juan-felipe-castilla/TP2_Analogica/FotosMed/Barrido de amplitud/E1/1m.jpeg

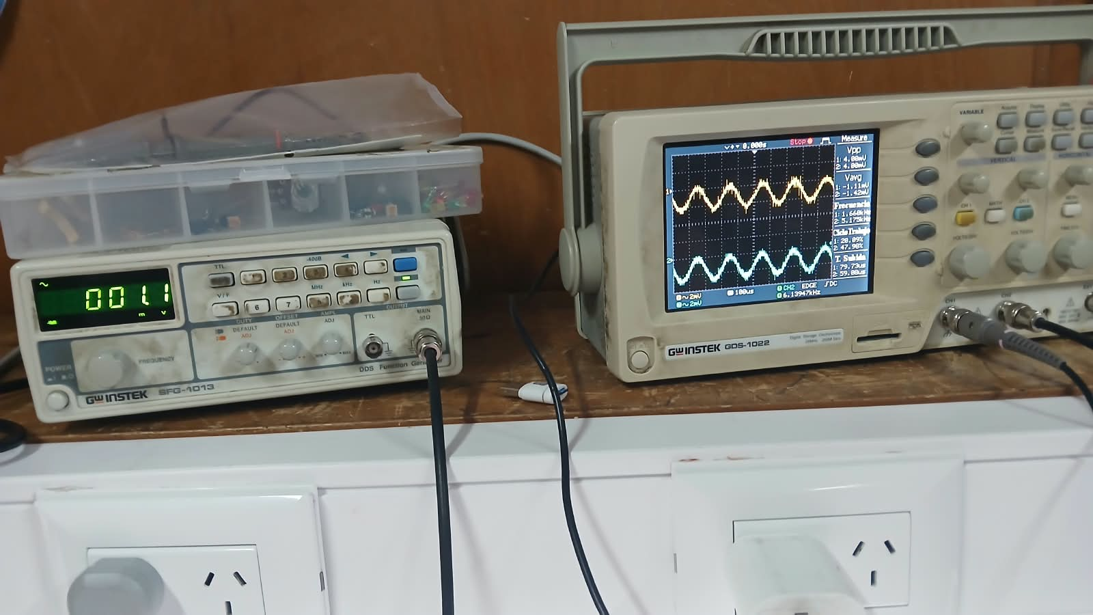
FotosMed/Barrido de amplitud/E1/1m.jpeg
