juan-felipe-castilla/TP2_Analogica/FotosMed/Barrido de amplitud/E1/2.5m.jpeg

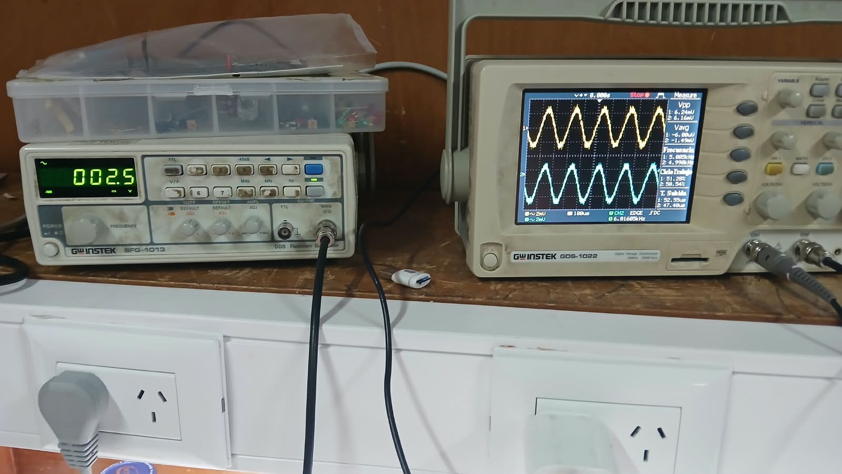
FotosMed/Barrido de amplitud/E1/2.5m.jpeg
