juan-felipe-castilla/TP2_Analogica/FotosMed/Barrido de amplitud/E1/5m.jpeg

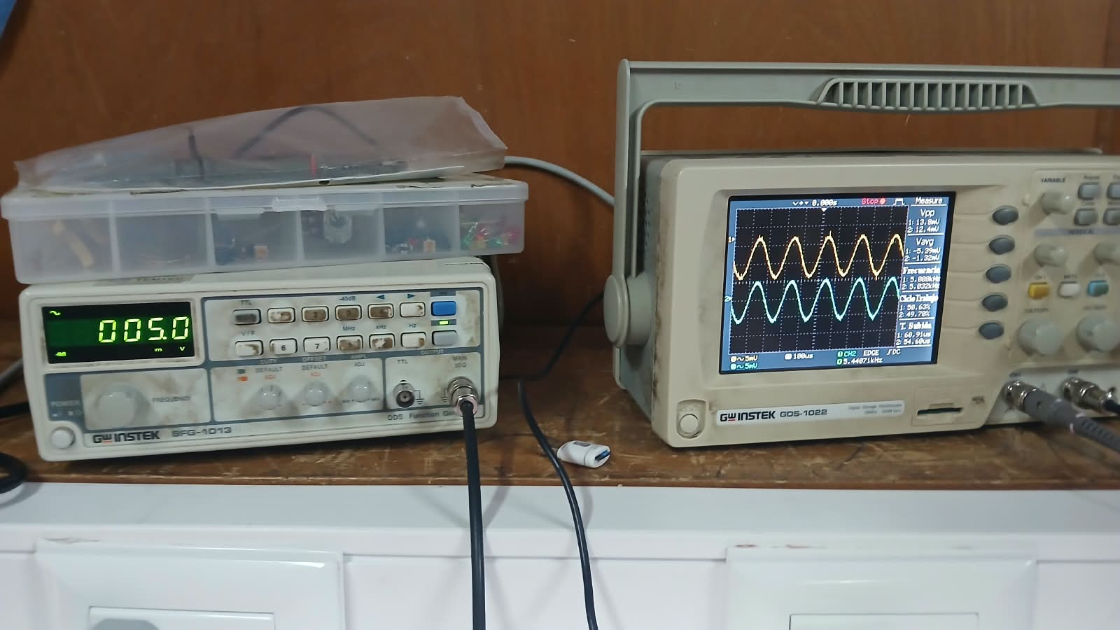
FotosMed/Barrido de amplitud/E1/5m.jpeg
