juan-felipe-castilla/TP2_Analogica/FotosMed/Barrido de amplitud/E1/7.5zoom.jpeg

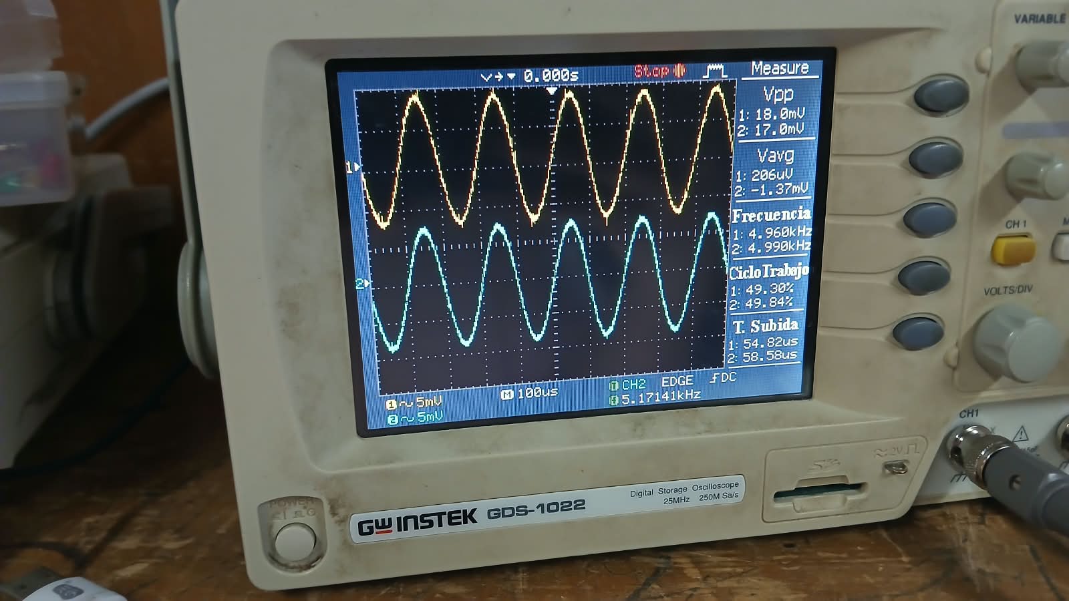
FotosMed/Barrido de amplitud/E1/7.5zoom.jpeg
