juan-felipe-castilla/TP2_Analogica/FotosMed/Barrido de amplitud/E1/10m.jpeg

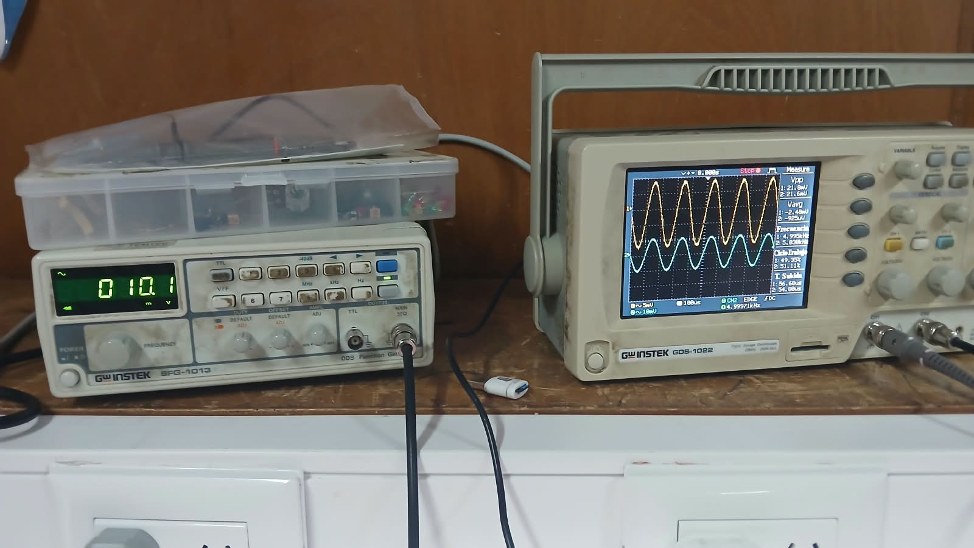
FotosMed/Barrido de amplitud/E1/10m.jpeg
