juan-felipe-castilla/TP2_Analogica/FotosMed/Barrido de amplitud/E1/12.jpeg

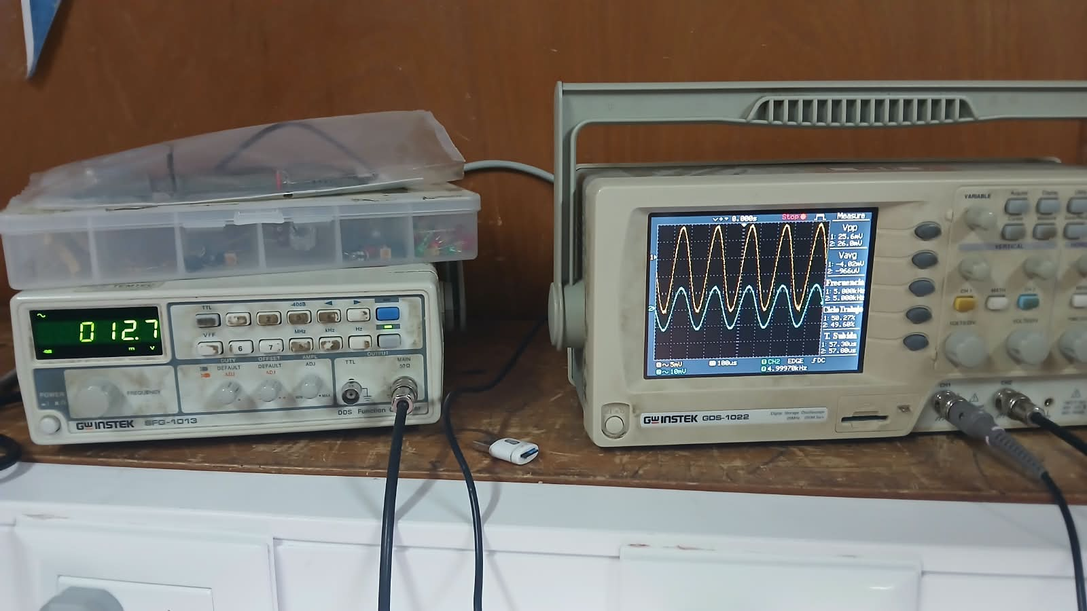
FotosMed/Barrido de amplitud/E1/12.jpeg
