juan-felipe-castilla/TP2_Analogica/FotosMed/Barrido de amplitud/E1/35m.jpeg

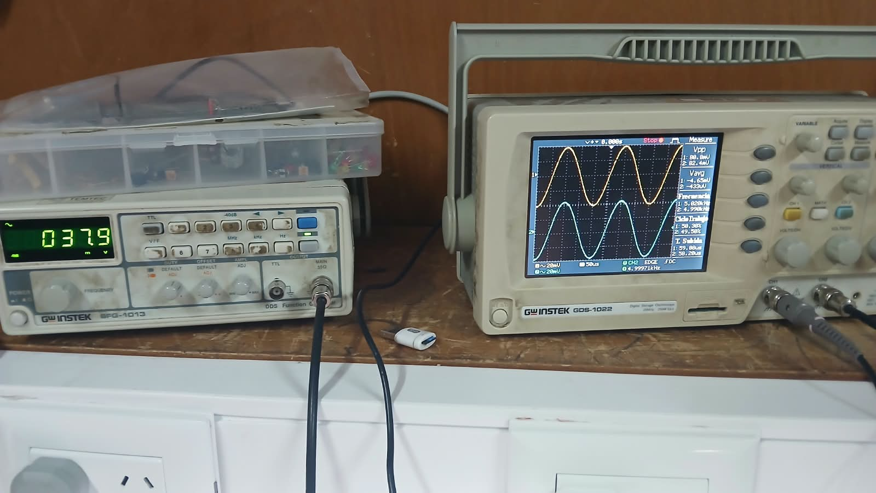
FotosMed/Barrido de amplitud/E1/35m.jpeg
