juan-felipe-castilla/TP2_Analogica/FotosMed/Barrido de amplitud/E1/37mzoom.jpeg

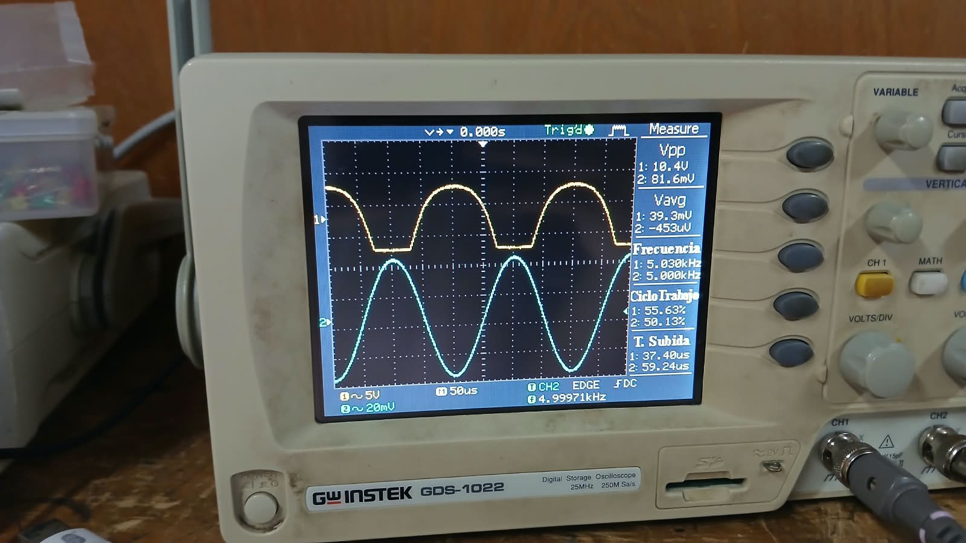
FotosMed/Barrido de amplitud/E1/37mzoom.jpeg
