juan-felipe-castilla/TP2_Analogica/FotosMed/Barrido de amplitud/E1/50m.jpeg

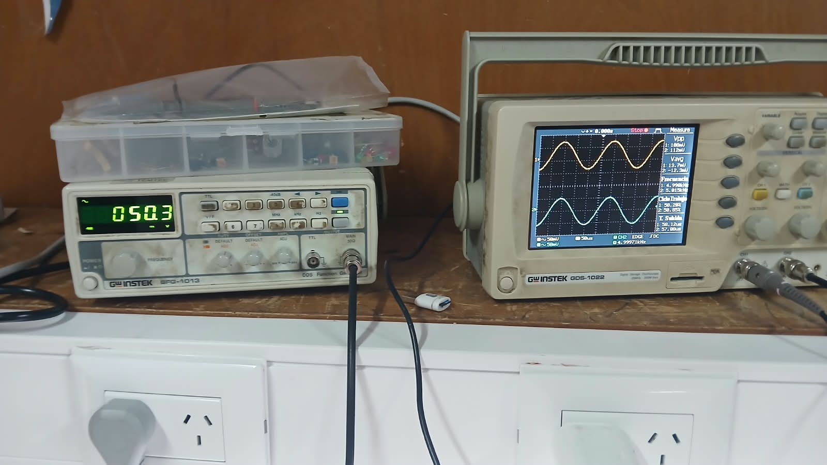
FotosMed/Barrido de amplitud/E1/50m.jpeg
