juan-felipe-castilla/TP2_Analogica/FotosMed/Barrido de amplitud/E12/1M.jpeg

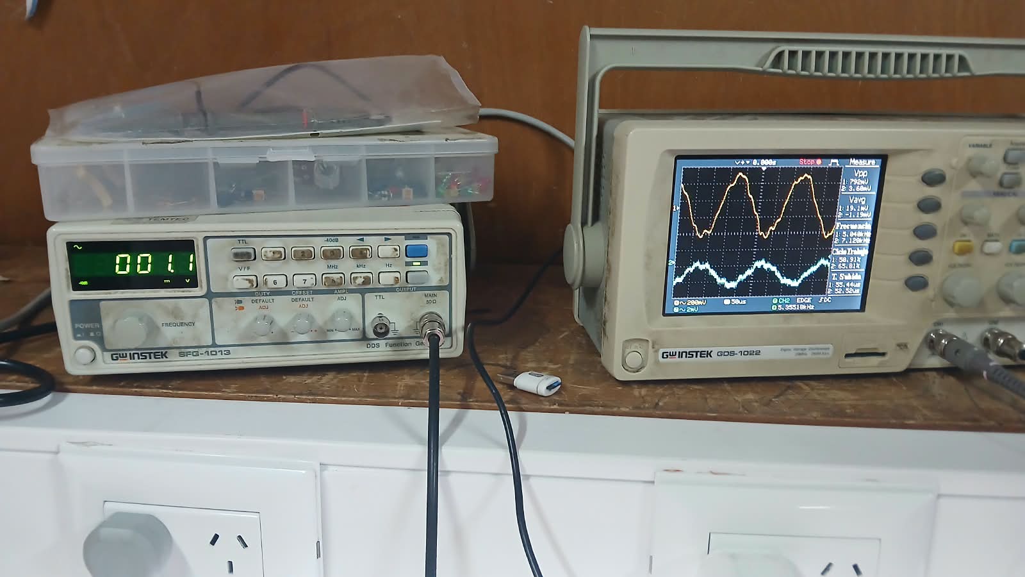
FotosMed/Barrido de amplitud/E12/1M.jpeg
