juan-felipe-castilla/TP2_Analogica/FotosMed/Barrido de amplitud/E12/5m.jpeg

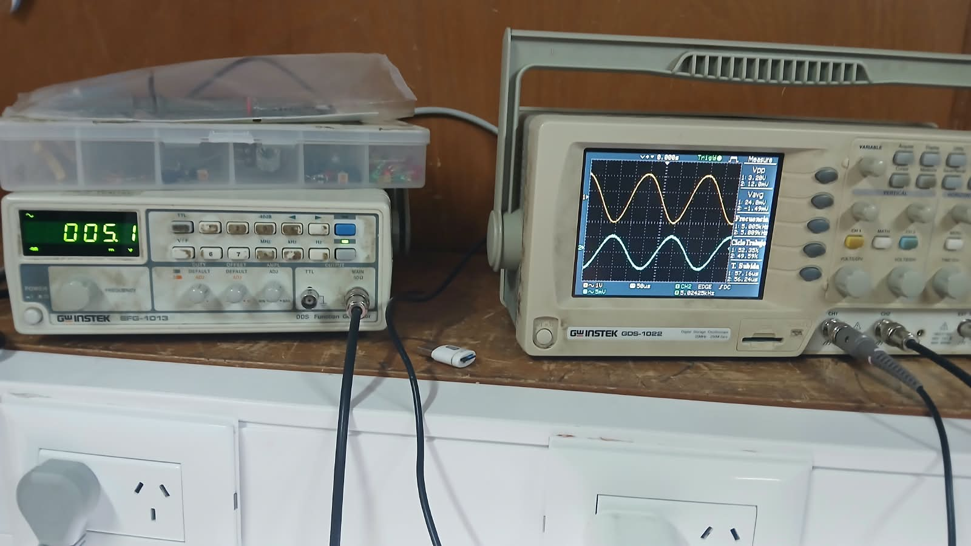
FotosMed/Barrido de amplitud/E12/5m.jpeg
