juan-felipe-castilla/TP2_Analogica/FotosMed/Barrido de amplitud/E12/7.5m.jpeg

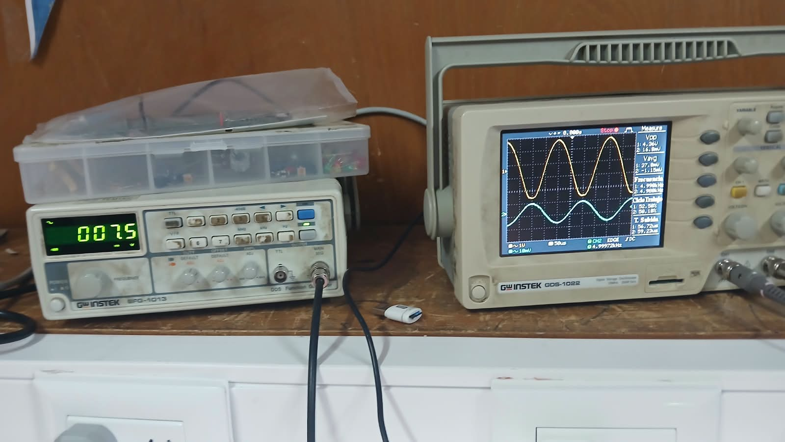
FotosMed/Barrido de amplitud/E12/7.5m.jpeg
