juan-felipe-castilla/TP2_Analogica/FotosMed/Barrido de amplitud/E12/8.5.jpeg

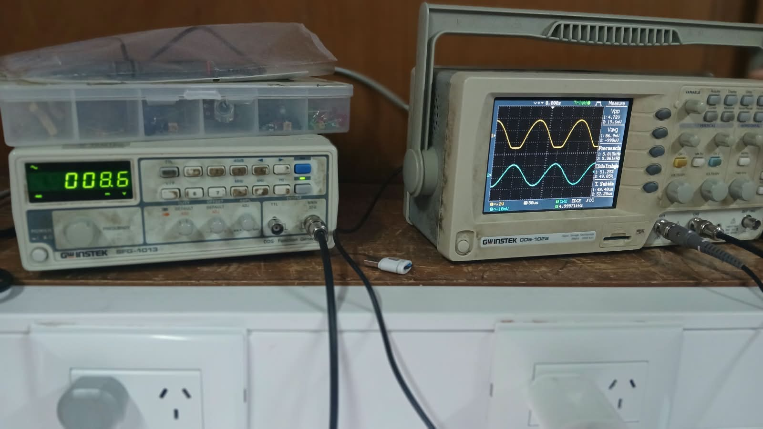
FotosMed/Barrido de amplitud/E12/8.5.jpeg
