juan-felipe-castilla/TP2_Analogica/FotosMed/Barrido de amplitud/E12/10mzoom.jpeg

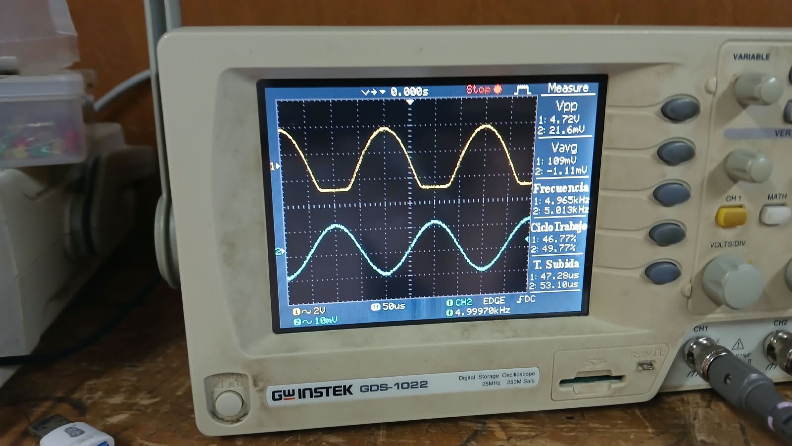
FotosMed/Barrido de amplitud/E12/10mzoom.jpeg
