juan-felipe-castilla/TP2_Analogica/FotosMed/Barrido de amplitud/E12/25m.jpeg

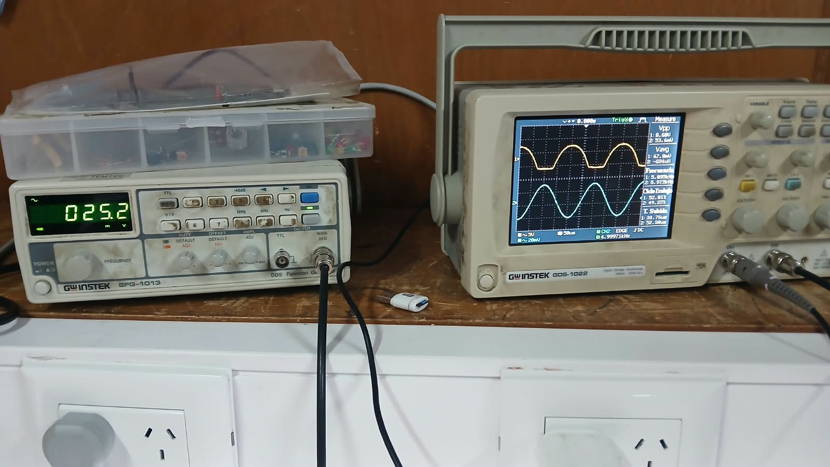
FotosMed/Barrido de amplitud/E12/25m.jpeg
