juan-felipe-castilla/TP2_Analogica/FotosMed/Barrido de amplitud/E12/50m.jpeg

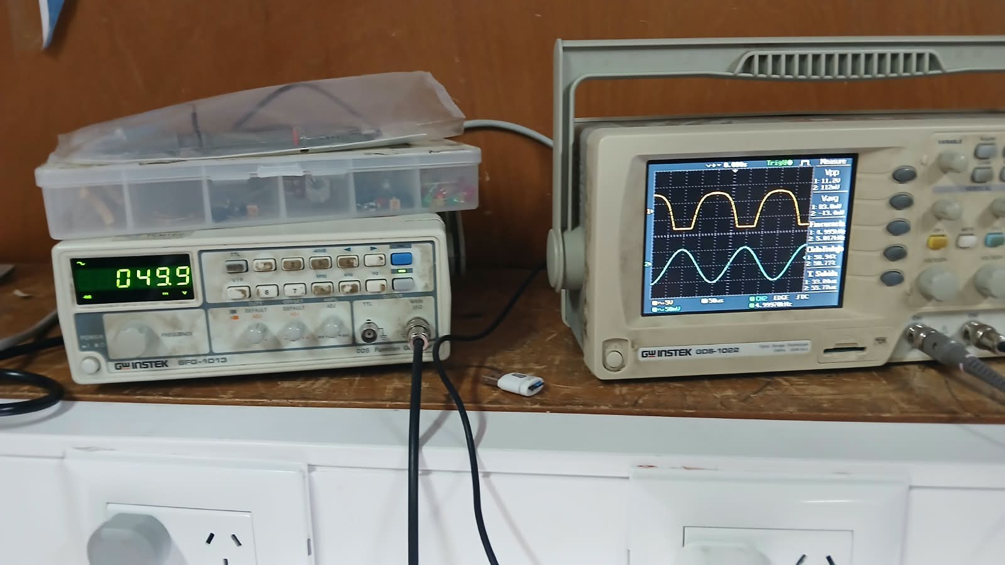
FotosMed/Barrido de amplitud/E12/50m.jpeg
