juan-felipe-castilla/TP2_Analogica/FotosMed/Barrido de amplitud/ETOTAL/1M.jpeg

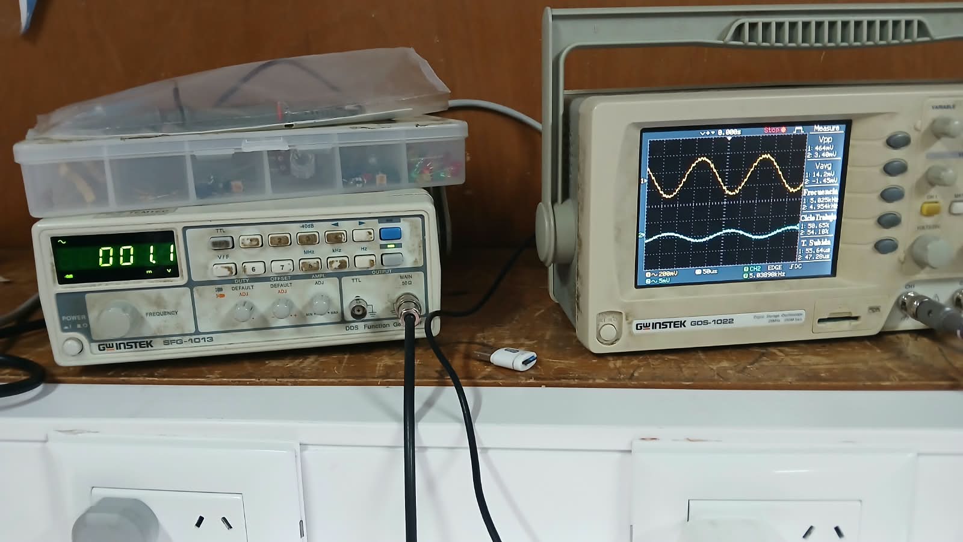
FotosMed/Barrido de amplitud/ETOTAL/1M.jpeg
