juan-felipe-castilla/TP2_Analogica/FotosMed/Barrido de amplitud/ETOTAL/1mzoom.jpeg

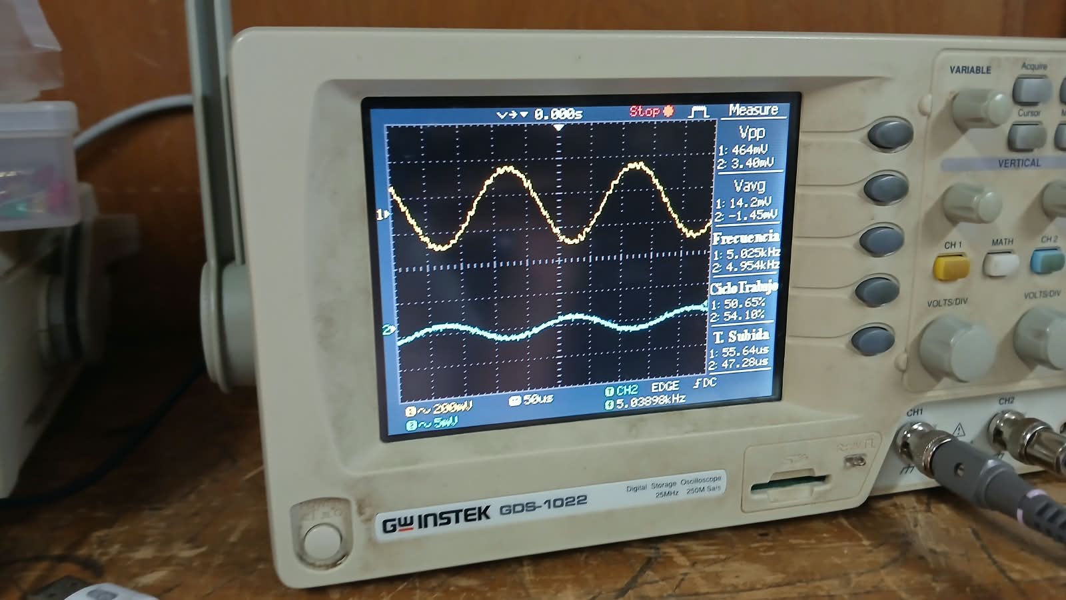
FotosMed/Barrido de amplitud/ETOTAL/1mzoom.jpeg
