juan-felipe-castilla/TP2_Analogica/FotosMed/Barrido de amplitud/ETOTAL/5m.jpeg

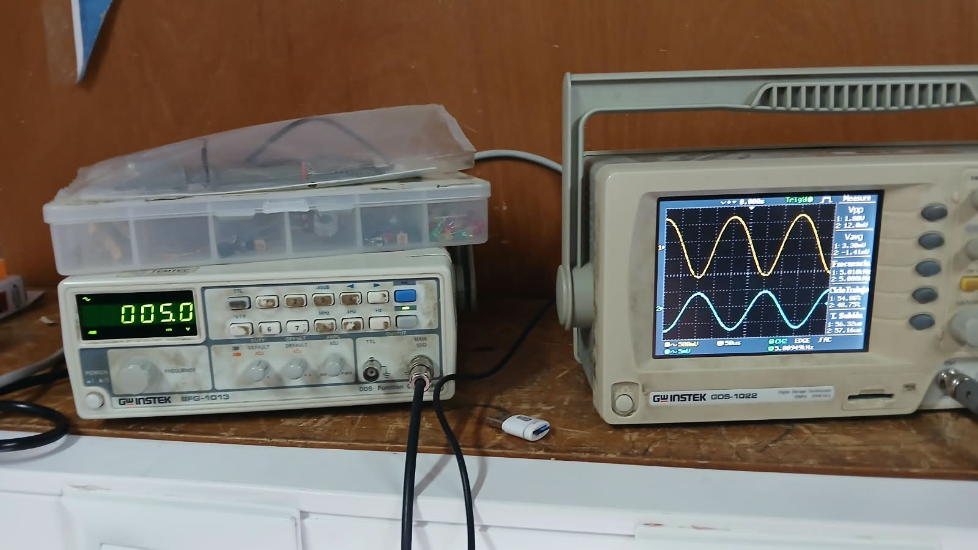
FotosMed/Barrido de amplitud/ETOTAL/5m.jpeg
