juan-felipe-castilla/TP2_Analogica/FotosMed/Barrido de amplitud/ETOTAL/7.5mzoom.jpeg

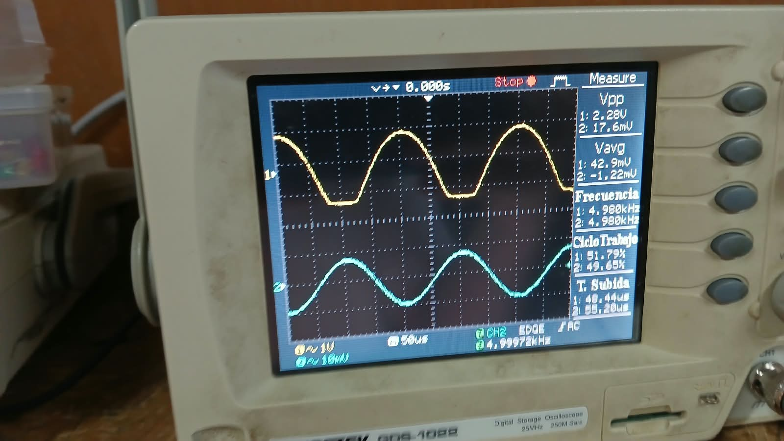
FotosMed/Barrido de amplitud/ETOTAL/7.5mzoom.jpeg
