juan-felipe-castilla/TP2_Analogica/FotosMed/Barrido de amplitud/ETOTAL/10m.jpeg

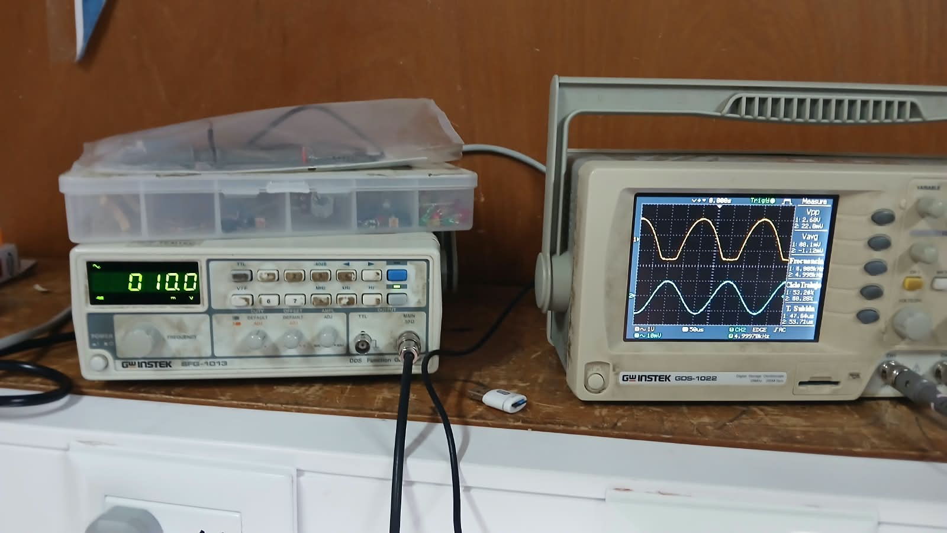
FotosMed/Barrido de amplitud/ETOTAL/10m.jpeg
