juan-felipe-castilla/TP2_Analogica/FotosMed/Barrido de amplitud/ETOTAL/12.5.jpeg

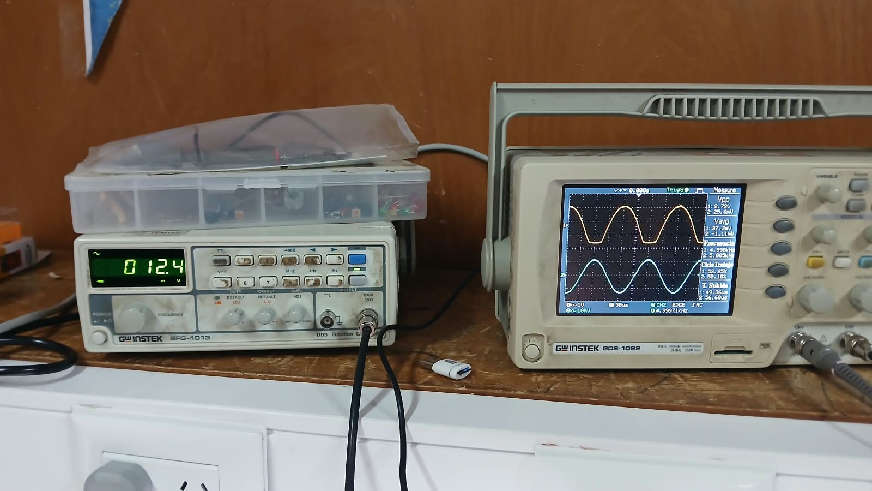
FotosMed/Barrido de amplitud/ETOTAL/12.5.jpeg
