juan-felipe-castilla/TP2_Analogica/FotosMed/Barrido de amplitud/ETOTAL/12.5zoom.jpeg

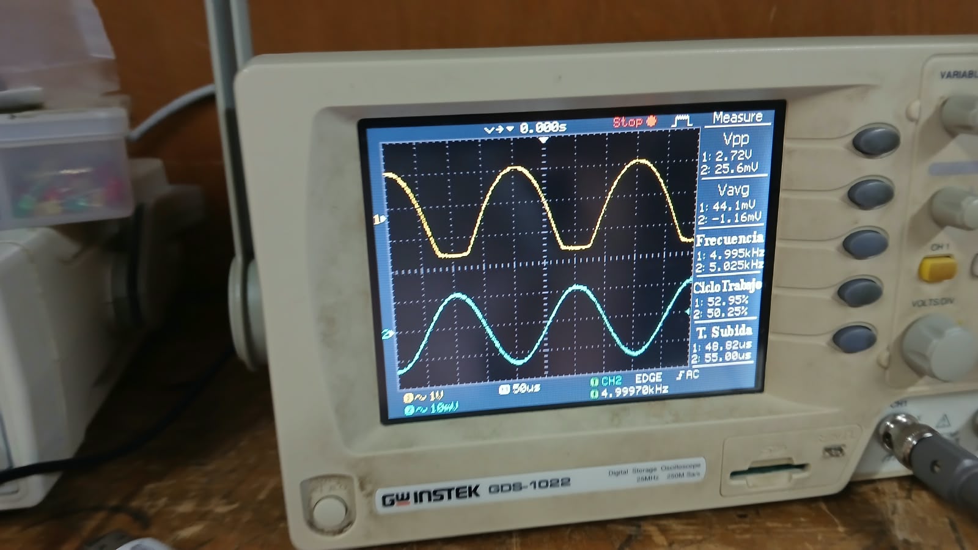
FotosMed/Barrido de amplitud/ETOTAL/12.5zoom.jpeg
