juan-felipe-castilla/TP2_Analogica/FotosMed/Barrido de amplitud/ETOTAL/25.jpeg

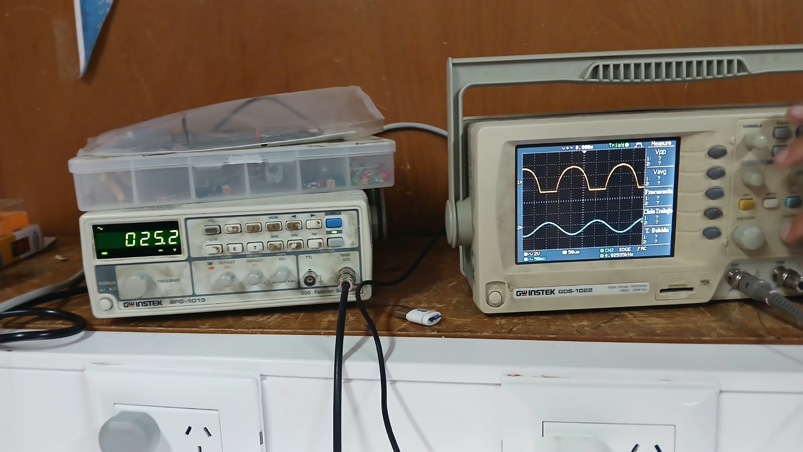
FotosMed/Barrido de amplitud/ETOTAL/25.jpeg
