juan-felipe-castilla/TP2_Analogica/FotosMed/Barrido de amplitud/ETOTAL/25zoom.jpeg

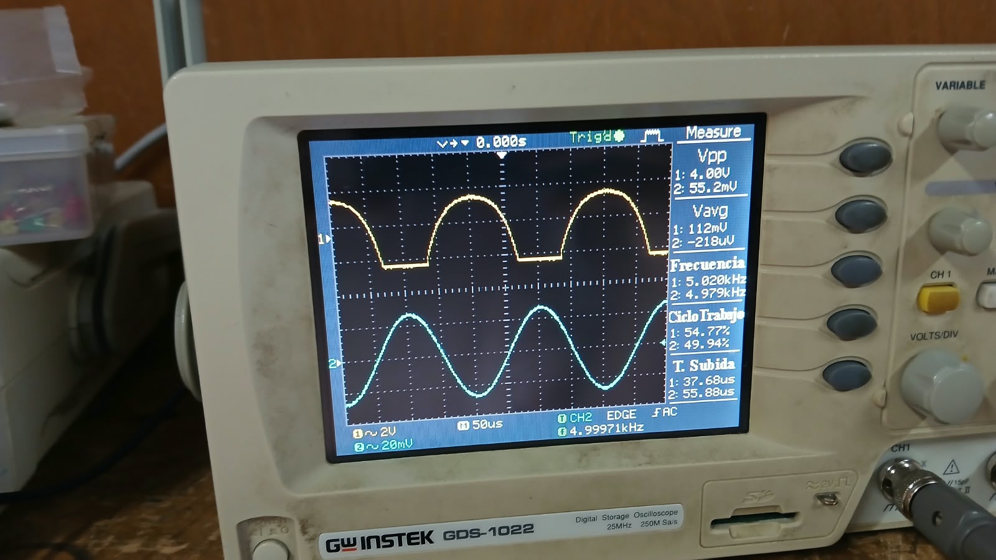
FotosMed/Barrido de amplitud/ETOTAL/25zoom.jpeg
