juan-felipe-castilla/TP2_Analogica/FotosMed/Barrido de amplitud/ETOTAL/37.5.jpeg

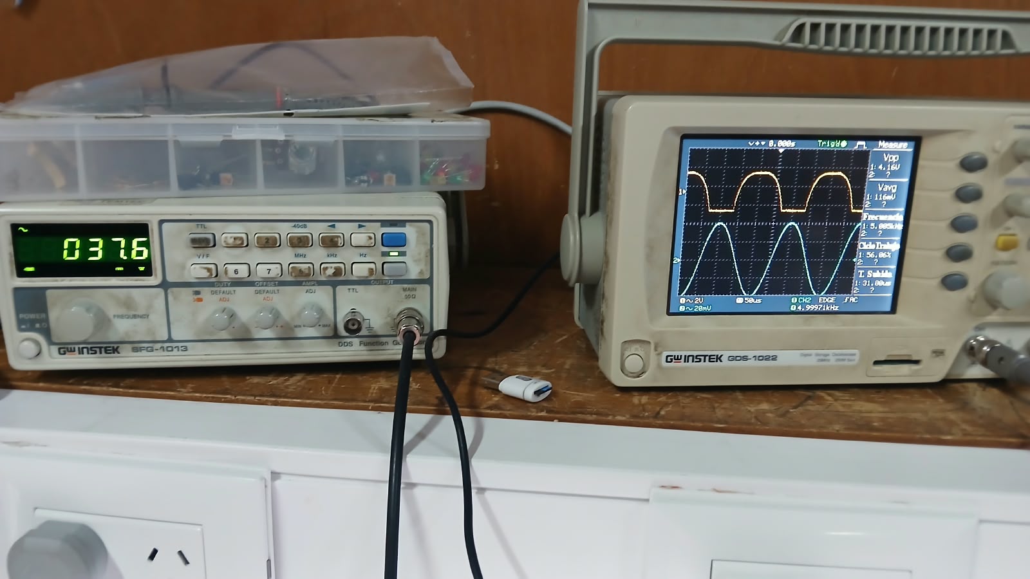
FotosMed/Barrido de amplitud/ETOTAL/37.5.jpeg
