juan-felipe-castilla/TP2_Analogica/FotosMed/Barrido de amplitud/ETOTAL/37.5zoom.jpeg

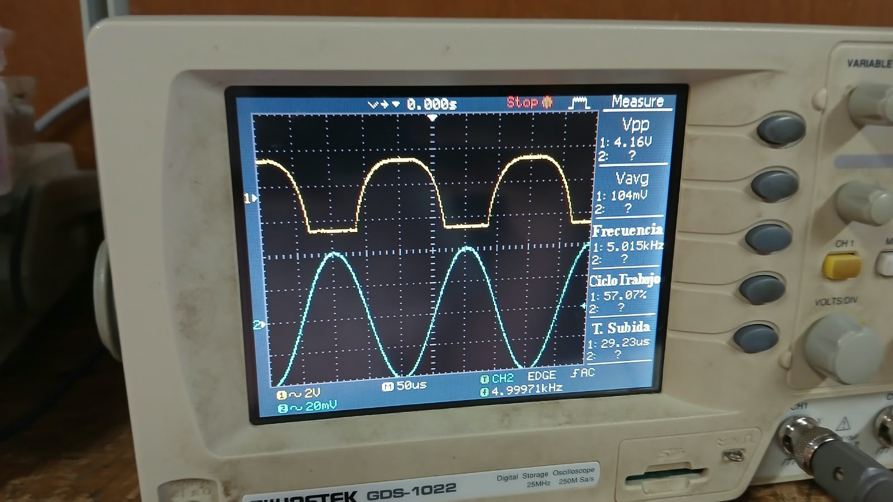
FotosMed/Barrido de amplitud/ETOTAL/37.5zoom.jpeg
