juan-felipe-castilla/TP2_Analogica/FotosMed/Barrido de amplitud/ETOTAL/50m.jpeg

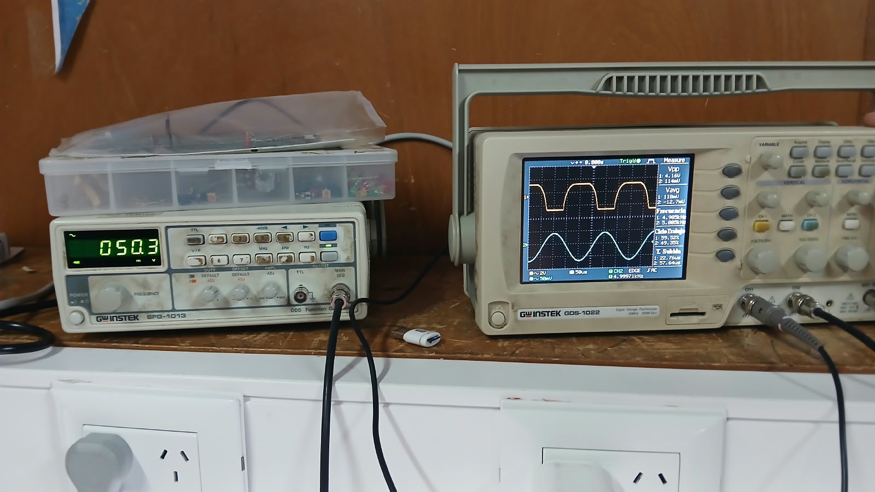
FotosMed/Barrido de amplitud/ETOTAL/50m.jpeg
