juan-felipe-castilla/TP2_Analogica/FotosMed/Barrido de frecuencia/Completo/1khzzoom.jpeg

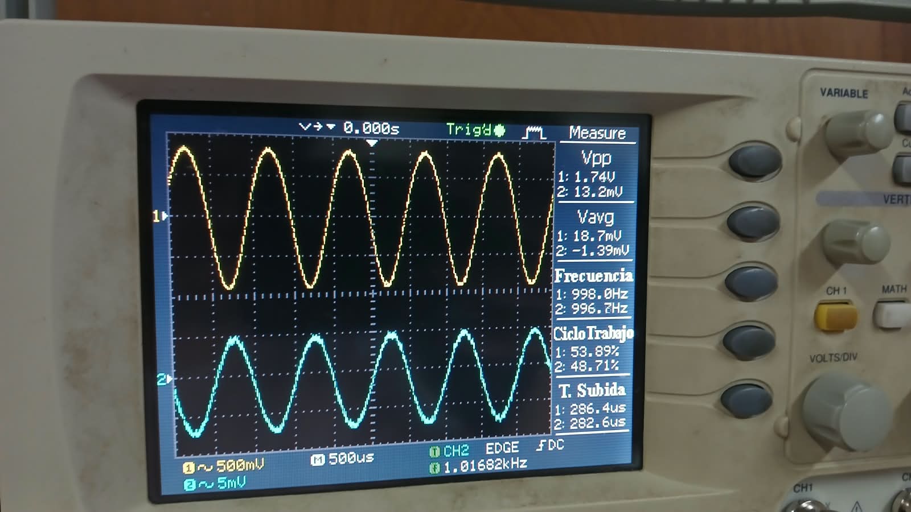
FotosMed/Barrido de frecuencia/Completo/1khzzoom.jpeg
