juan-felipe-castilla/TP2_Analogica/FotosMed/Barrido de frecuencia/Completo/1Mhz.jpeg

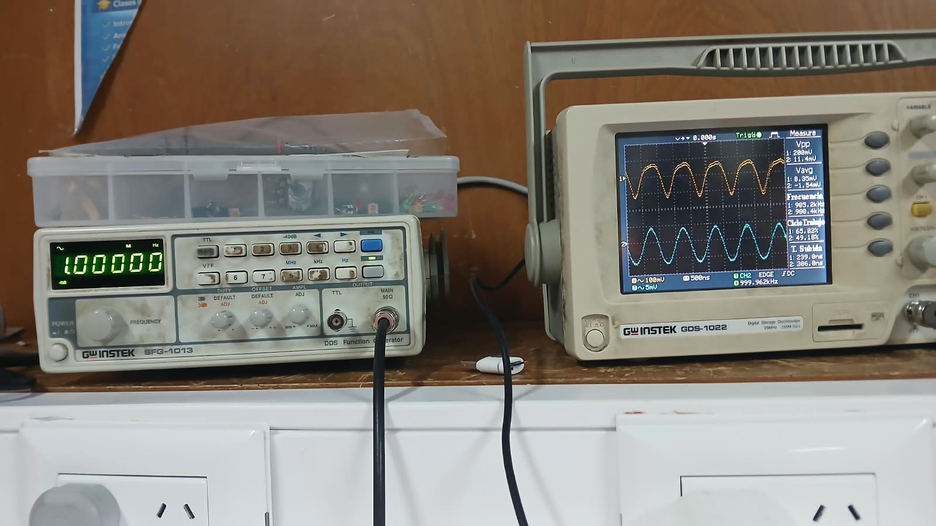
FotosMed/Barrido de frecuencia/Completo/1Mhz.jpeg
