juan-felipe-castilla/TP2_Analogica/FotosMed/Barrido de frecuencia/Completo/3M.jpeg

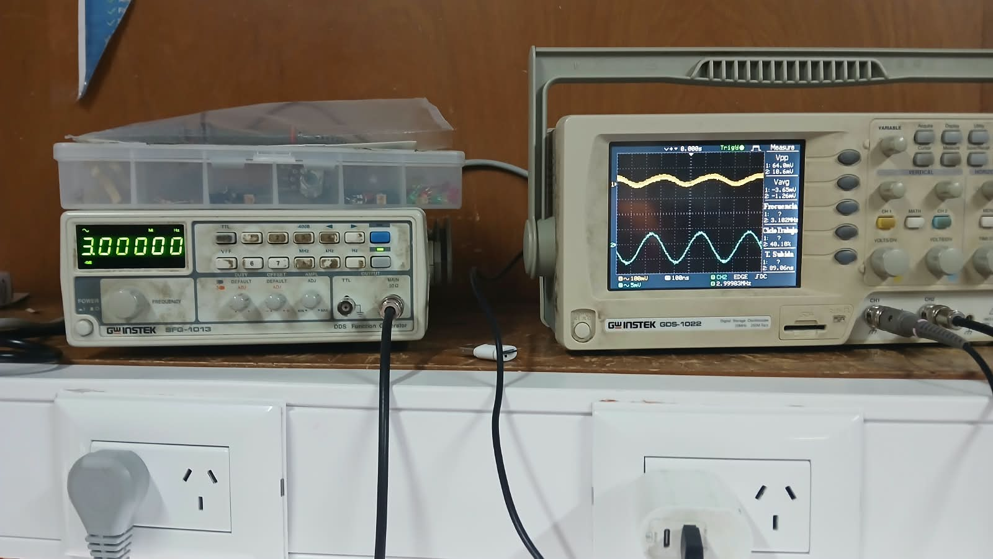
FotosMed/Barrido de frecuencia/Completo/3M.jpeg
