juan-felipe-castilla/TP2_Analogica/FotosMed/Barrido de frecuencia/Completo/10hz.jpeg

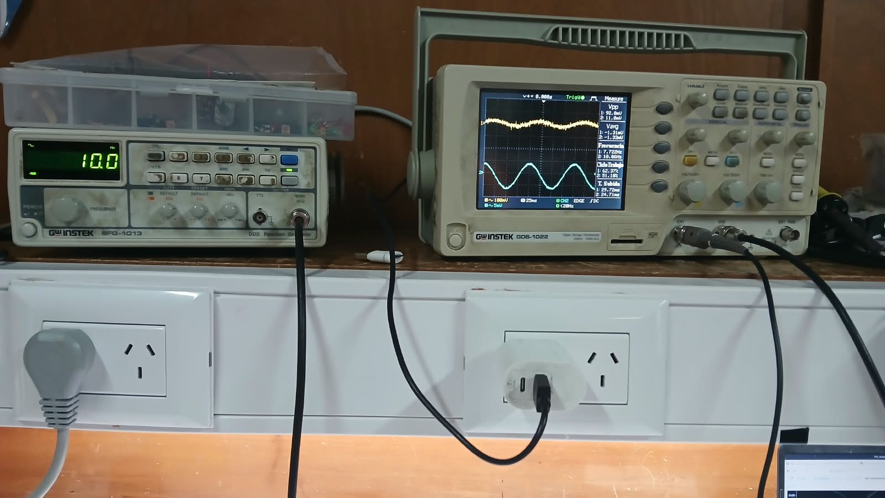
FotosMed/Barrido de frecuencia/Completo/10hz.jpeg
