juan-felipe-castilla/TP2_Analogica/FotosMed/Barrido de frecuencia/Completo/100hz.jpeg

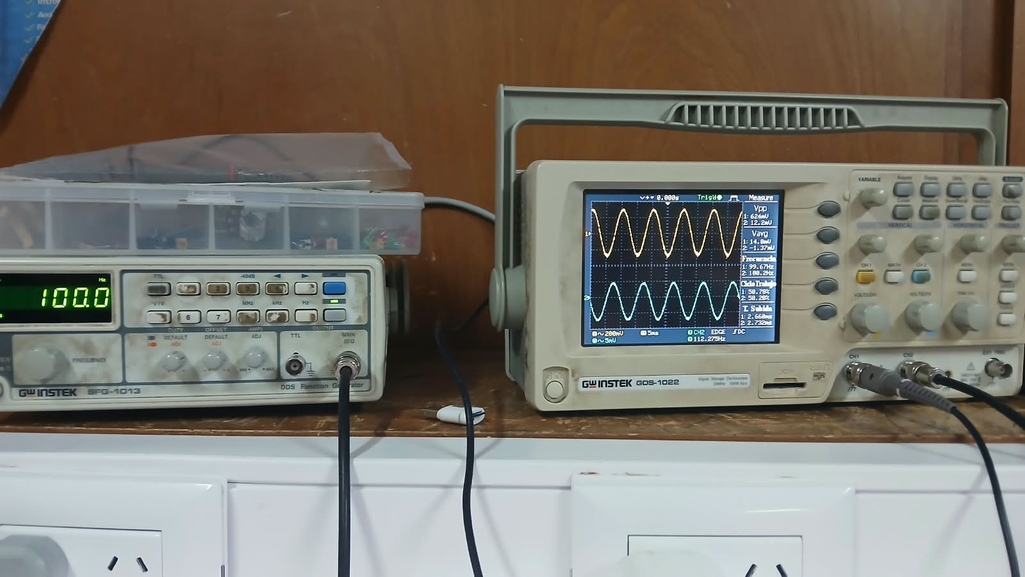
FotosMed/Barrido de frecuencia/Completo/100hz.jpeg
