juan-felipe-castilla/TP2_Analogica/FotosMed/Barrido de frecuencia/Completo/100hzzoom.jpeg

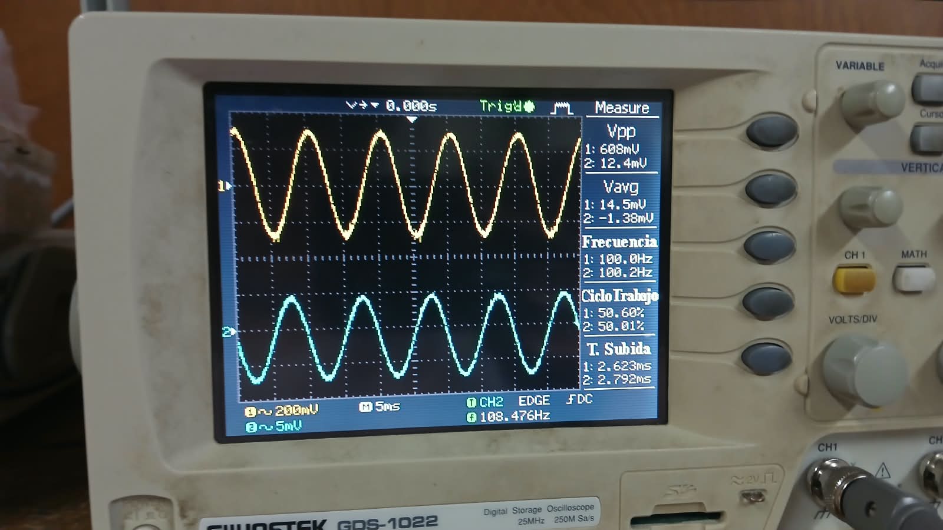
FotosMed/Barrido de frecuencia/Completo/100hzzoom.jpeg
