juan-felipe-castilla/TP2_Analogica/FotosMed/Barrido de frecuencia/E1/1kzoom.jpeg

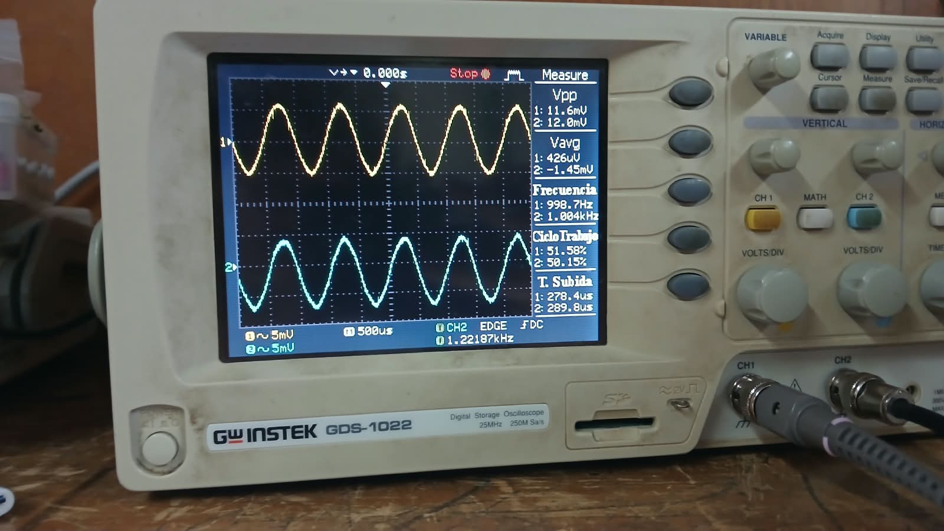
FotosMed/Barrido de frecuencia/E1/1kzoom.jpeg
