juan-felipe-castilla/TP2_Analogica/FotosMed/Barrido de frecuencia/E1/3m.jpeg

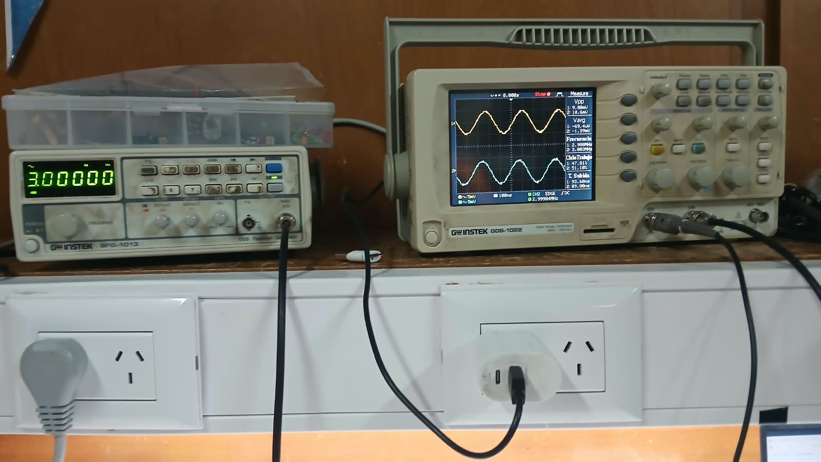
FotosMed/Barrido de frecuencia/E1/3m.jpeg
