juan-felipe-castilla/TP2_Analogica/FotosMed/Barrido de frecuencia/E1/10kzoom.jpeg

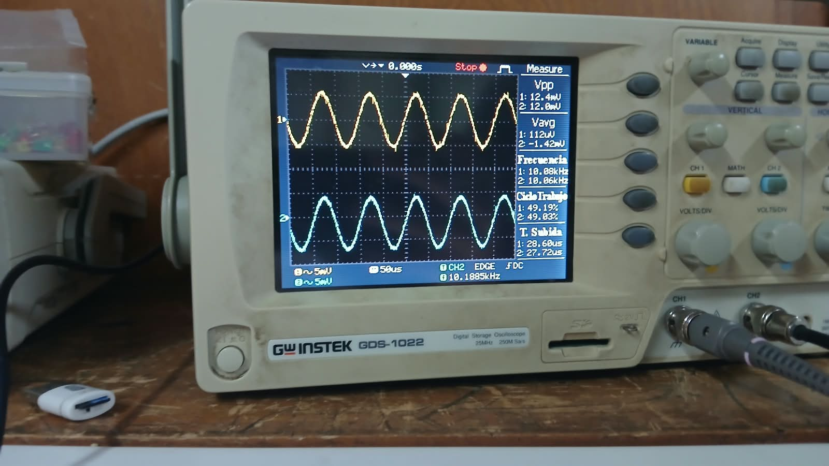
FotosMed/Barrido de frecuencia/E1/10kzoom.jpeg
