juan-felipe-castilla/TP2_Analogica/FotosMed/Barrido de frecuencia/E1/100k.jpeg

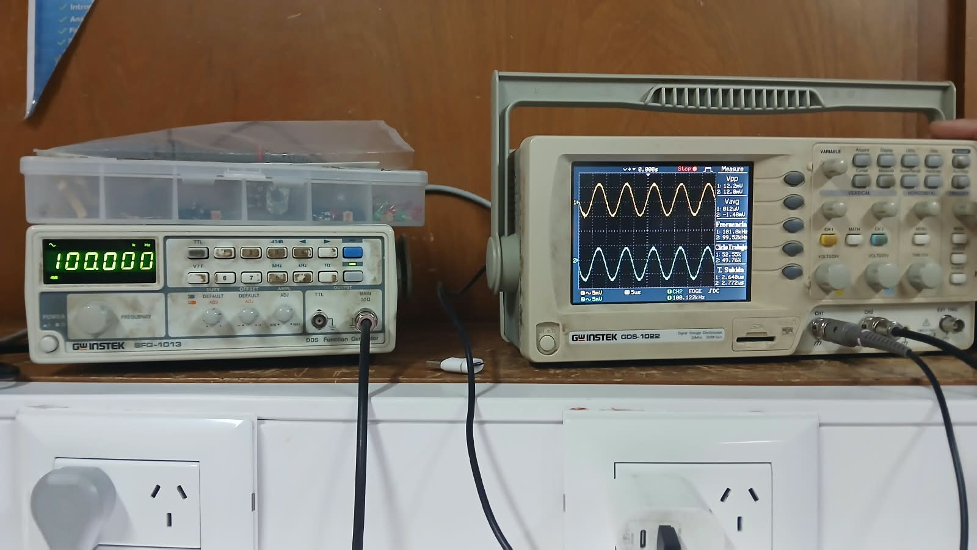
FotosMed/Barrido de frecuencia/E1/100k.jpeg
