juan-felipe-castilla/TP2_Analogica/FotosMed/Barrido de frecuencia/E1/forma de medir.jpeg

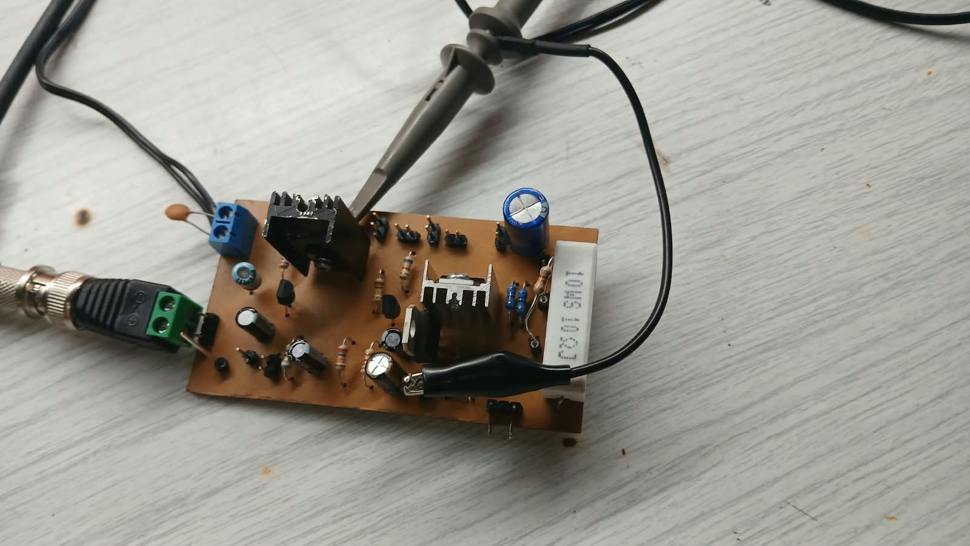
FotosMed/Barrido de frecuencia/E1/forma de medir.jpeg
