juan-felipe-castilla/TP2_Analogica/FotosMed/Barrido de frecuencia/E12/1M.jpeg

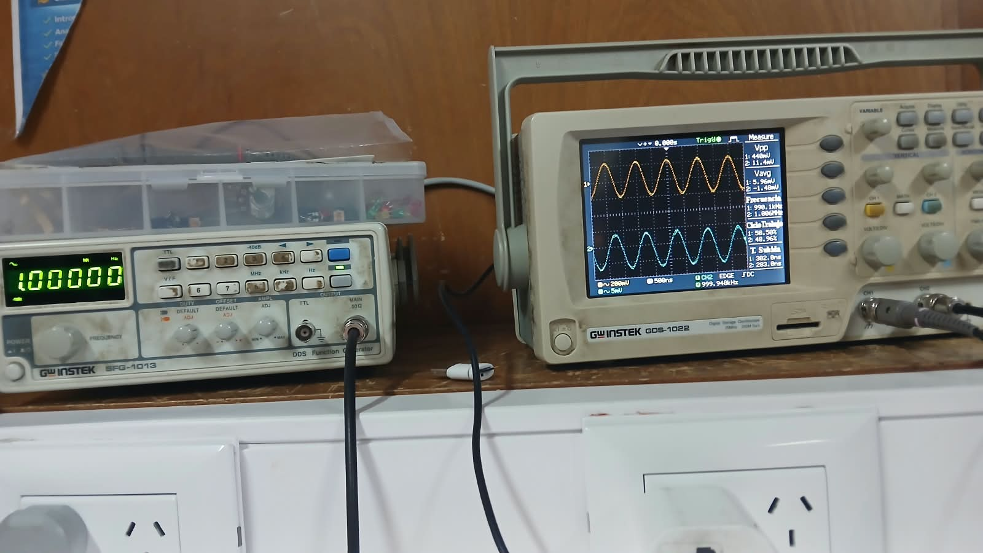
FotosMed/Barrido de frecuencia/E12/1M.jpeg
