juan-felipe-castilla/TP2_Analogica/FotosMed/Barrido de frecuencia/E12/3m.jpeg

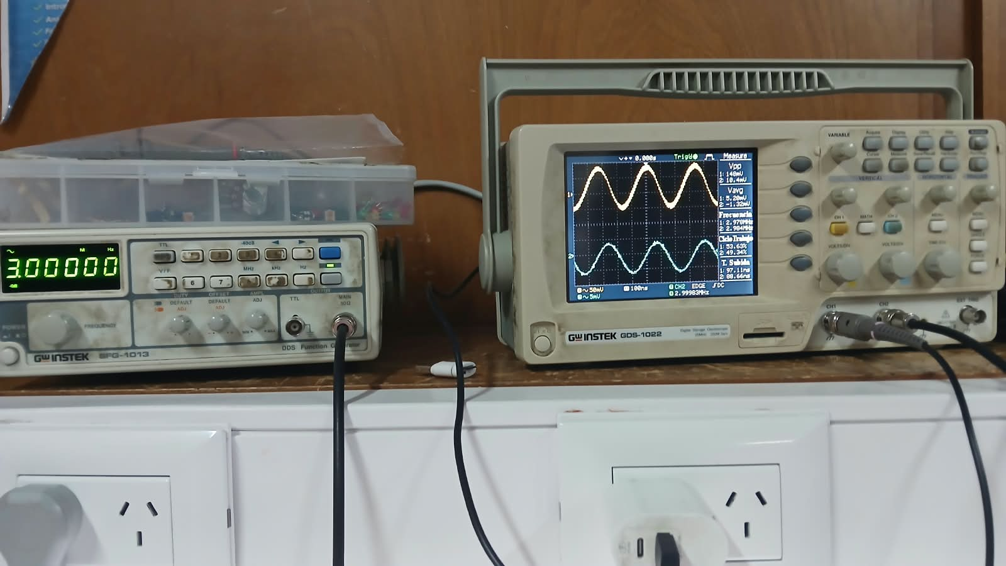
FotosMed/Barrido de frecuencia/E12/3m.jpeg
