juan-felipe-castilla/TP2_Analogica/FotosMed/Barrido de frecuencia/E12/10HZ.jpeg

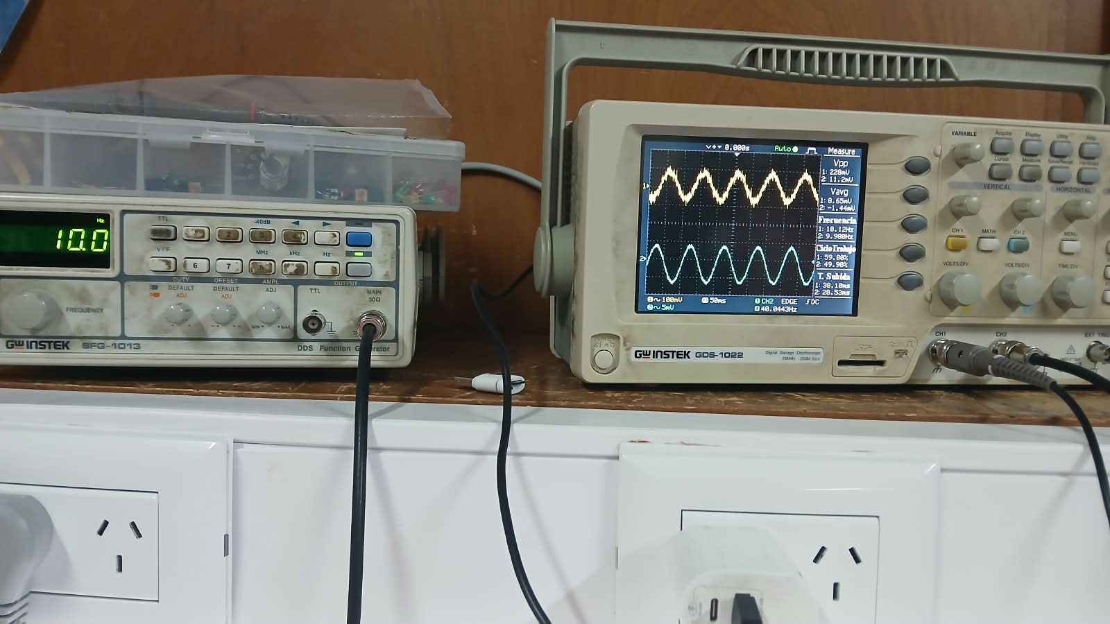
FotosMed/Barrido de frecuencia/E12/10HZ.jpeg
