juan-felipe-castilla/TP2_Analogica/FotosMed/Barrido de frecuencia/E12/10HZZOOM.jpeg

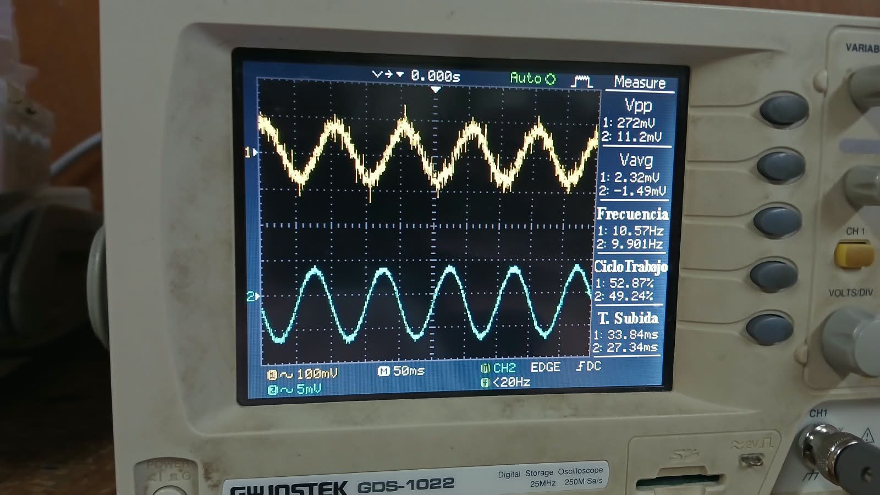
FotosMed/Barrido de frecuencia/E12/10HZZOOM.jpeg
