juan-felipe-castilla/TP2_Analogica/FotosMed/Barrido de frecuencia/E12/100hz.jpeg

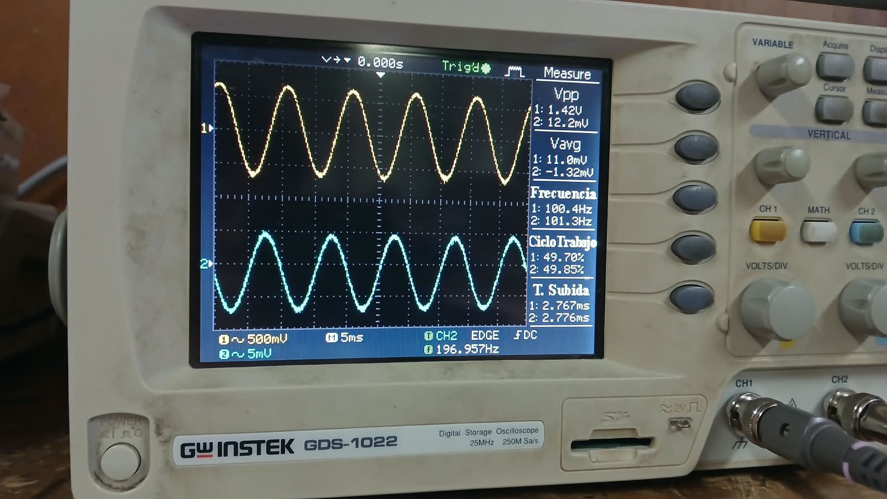
FotosMed/Barrido de frecuencia/E12/100hz.jpeg
