juan-felipe-castilla/TP2_Analogica/FotosMed/Barrido de frecuencia/E12/100k.jpeg

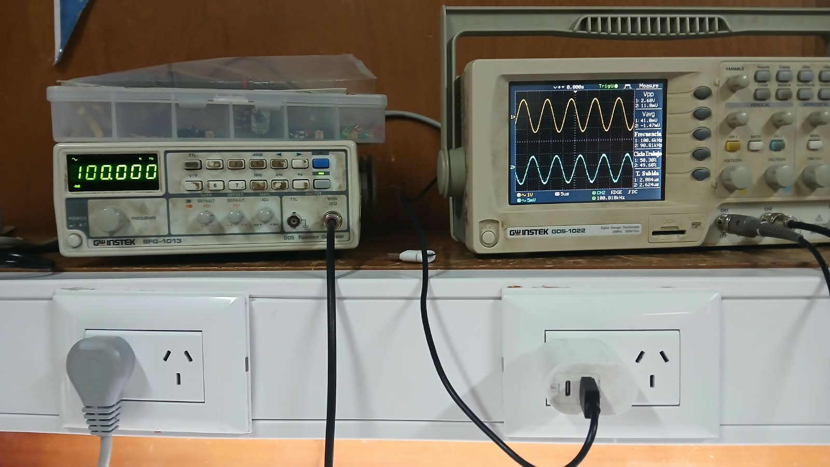
FotosMed/Barrido de frecuencia/E12/100k.jpeg
