juan-felipe-castilla/TP2_Analogica/FotosMed/FFT/Completo/2.5comzoom (2).jpeg

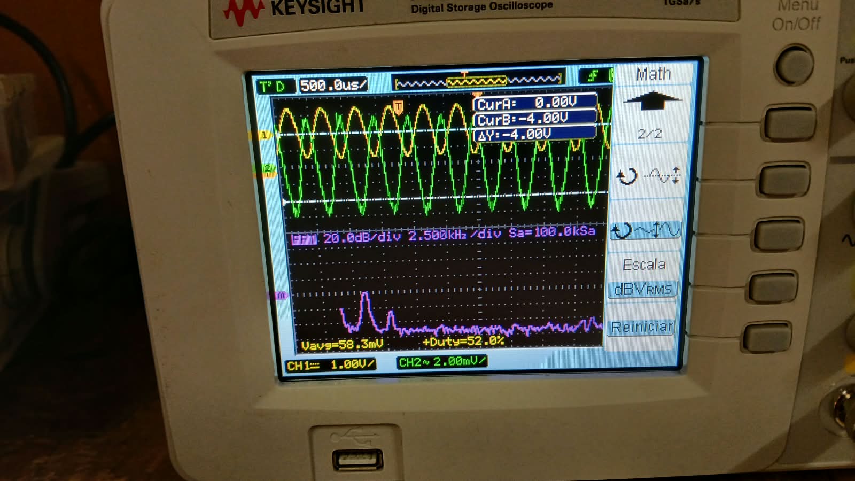
FotosMed/FFT/Completo/2.5comzoom (2).jpeg
