juan-felipe-castilla/TP2_Analogica/FotosMed/FFT/Completo/2.5comzoom.jpeg

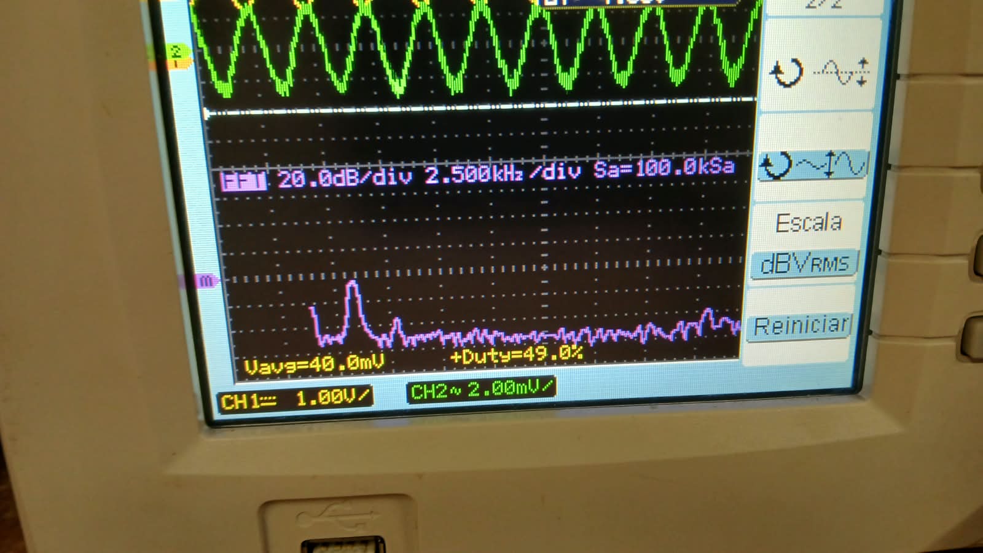
FotosMed/FFT/Completo/2.5comzoom.jpeg
