juan-felipe-castilla/TP2_Analogica/FotosMed/FFT/Completo/5com.jpeg

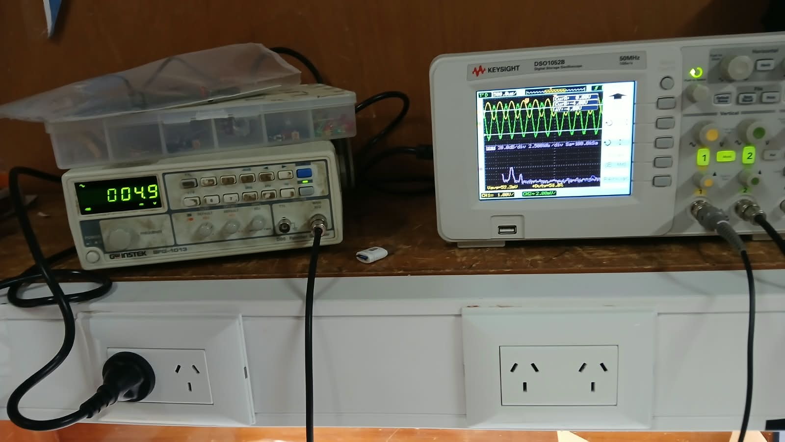
FotosMed/FFT/Completo/5com.jpeg
