juan-felipe-castilla/TP2_Analogica/FotosMed/FFT/Completo/5comzoom.jpeg

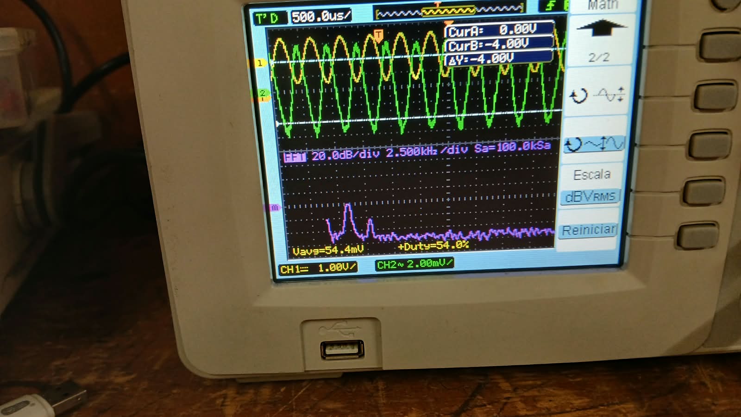
FotosMed/FFT/Completo/5comzoom.jpeg
