juan-felipe-castilla/TP2_Analogica/FotosMed/FFT/Completo/10comzoom.jpeg

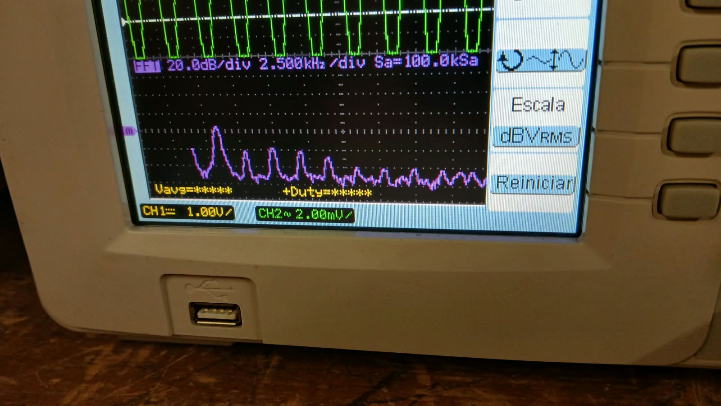
FotosMed/FFT/Completo/10comzoom.jpeg
