juan-felipe-castilla/TP2_Analogica/FotosMed/FFT/Completo/10zom.jpeg

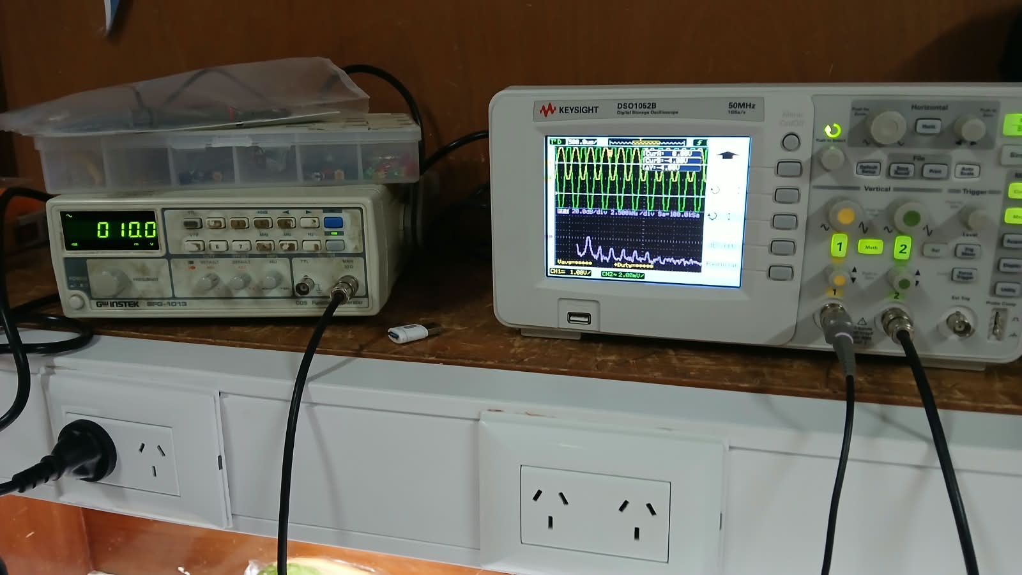
FotosMed/FFT/Completo/10zom.jpeg
