juan-felipe-castilla/TP2_Analogica/FotosMed/FFT/Completo/25com.jpeg

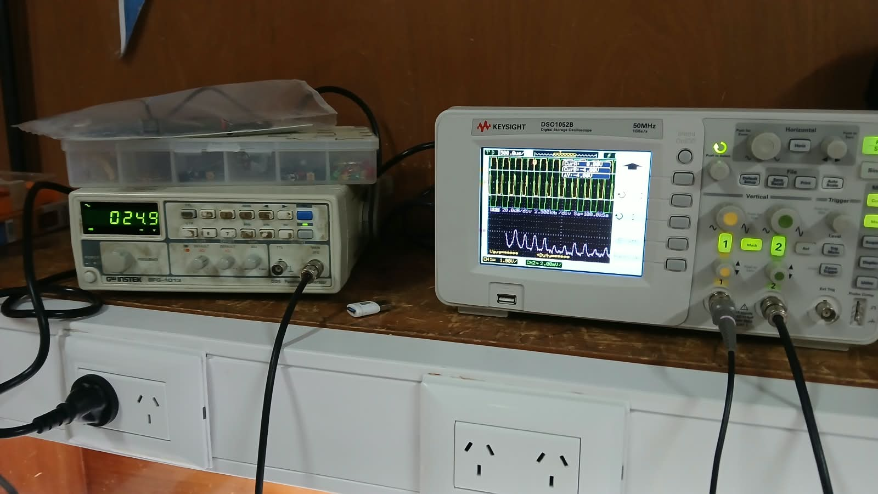
FotosMed/FFT/Completo/25com.jpeg
