juan-felipe-castilla/TP2_Analogica/FotosMed/FFT/Completo/25comzoom.jpeg

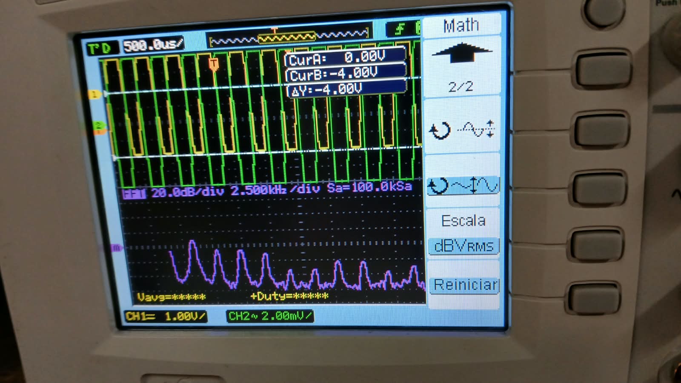
FotosMed/FFT/Completo/25comzoom.jpeg
