juan-felipe-castilla/TP2_Analogica/FotosMed/FFT/Completo/50com.jpeg

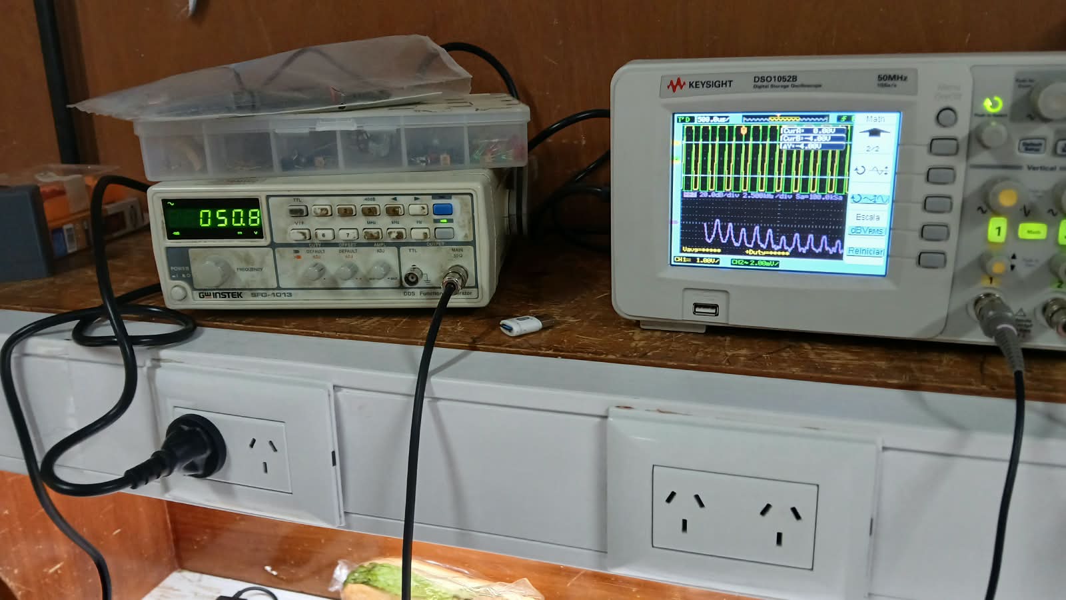
FotosMed/FFT/Completo/50com.jpeg
