juan-felipe-castilla/TP2_Analogica/FotosMed/FFT/Completo/50comzoom.jpeg

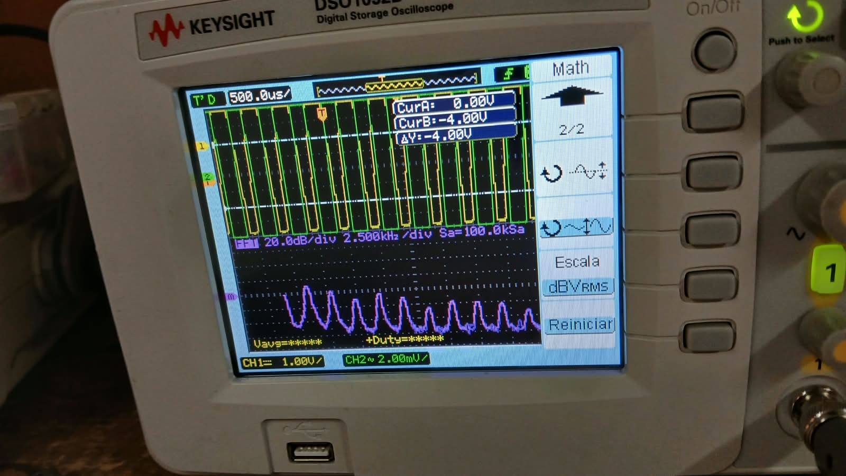
FotosMed/FFT/Completo/50comzoom.jpeg
