juan-felipe-castilla/TP2_Analogica/FotosMed/FFT/Dar/2.5Dar.jpeg

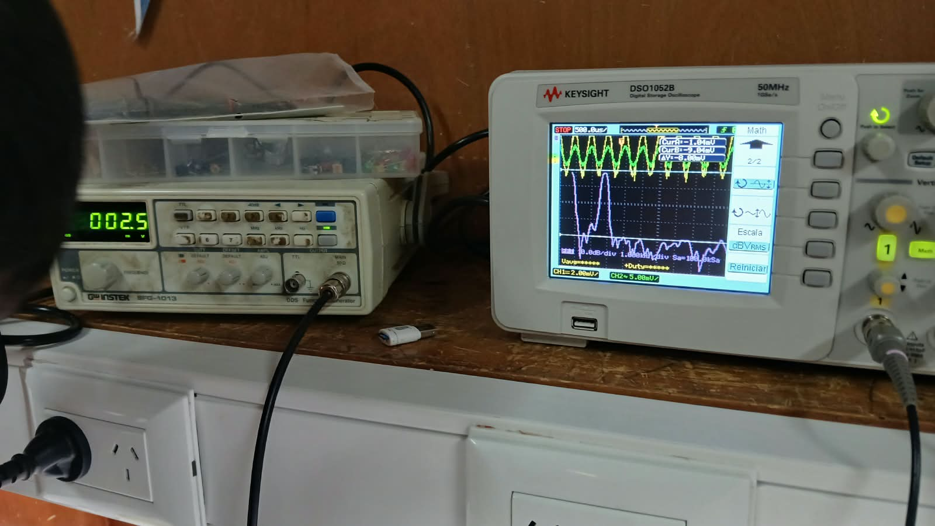
FotosMed/FFT/Dar/2.5Dar.jpeg
