juan-felipe-castilla/TP2_Analogica/FotosMed/FFT/Dar/5dar.jpeg

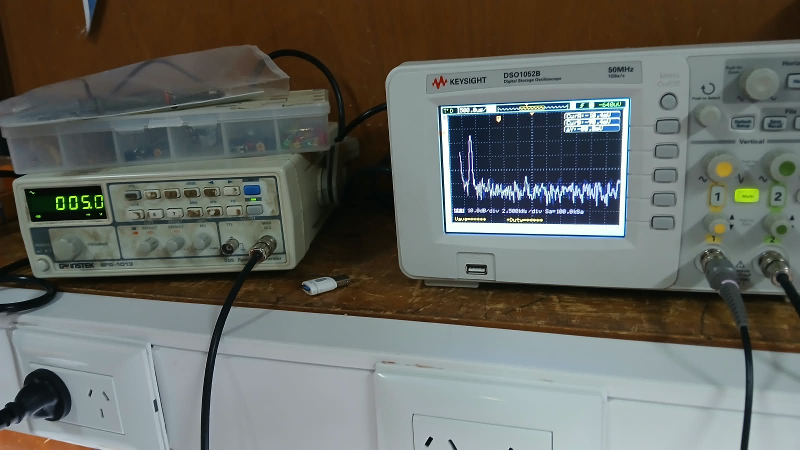
FotosMed/FFT/Dar/5dar.jpeg
