juan-felipe-castilla/TP2_Analogica/FotosMed/FFT/Dar/10Dar.jpeg

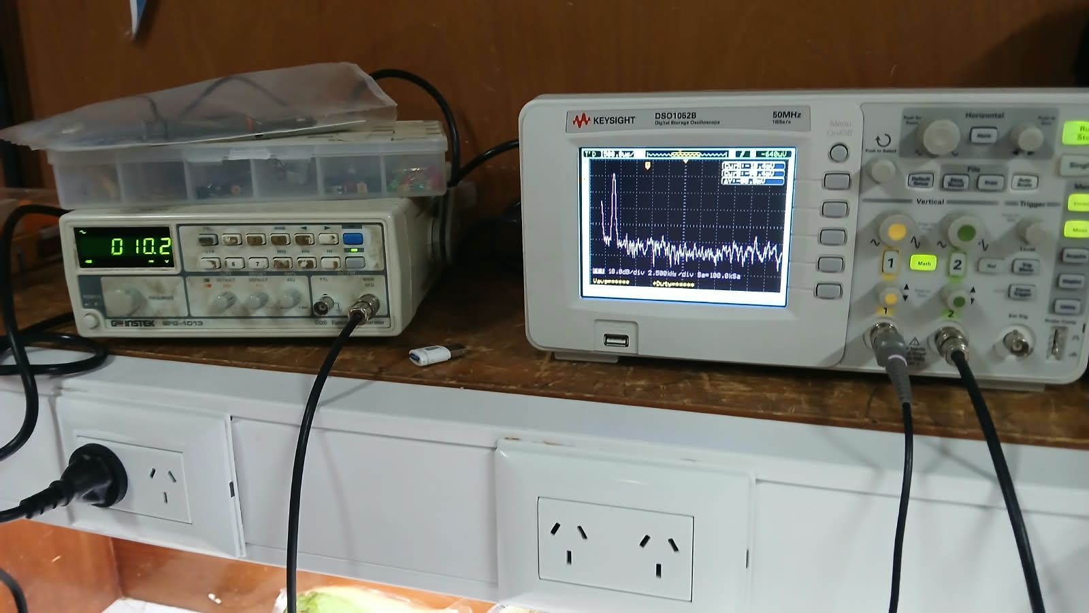
FotosMed/FFT/Dar/10Dar.jpeg
