juan-felipe-castilla/TP2_Analogica/FotosMed/FFT/Dar/10Darzoom.jpeg

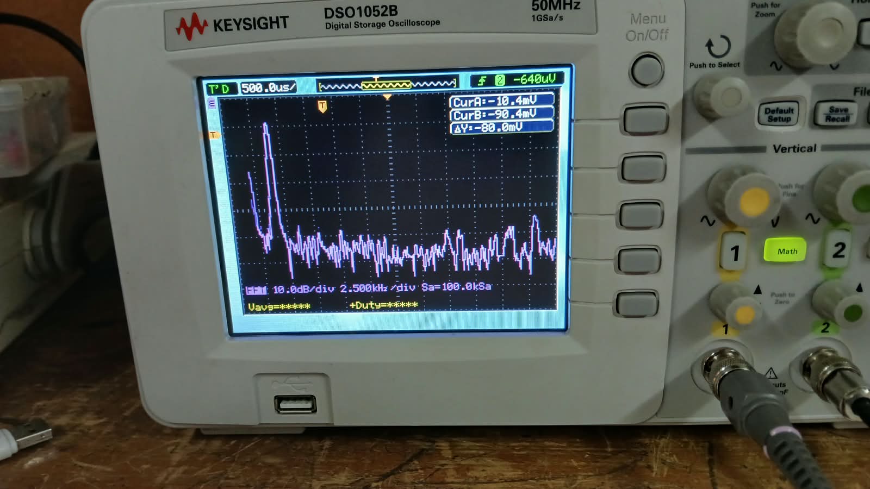
FotosMed/FFT/Dar/10Darzoom.jpeg
