juan-felipe-castilla/TP2_Analogica/FotosMed/FFT/Dar/25dar.jpeg

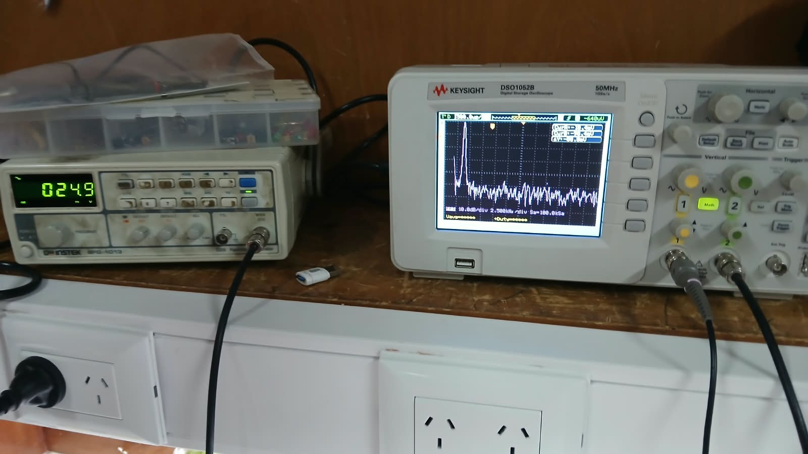
FotosMed/FFT/Dar/25dar.jpeg
