juan-felipe-castilla/TP2_Analogica/FotosMed/FFT/Dar/25darzoom.jpeg

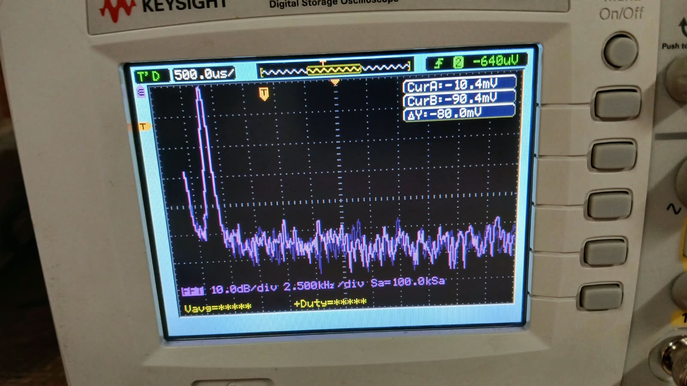
FotosMed/FFT/Dar/25darzoom.jpeg
