juan-felipe-castilla/TP2_Analogica/FotosMed/FFT/Dar/50dar.jpeg

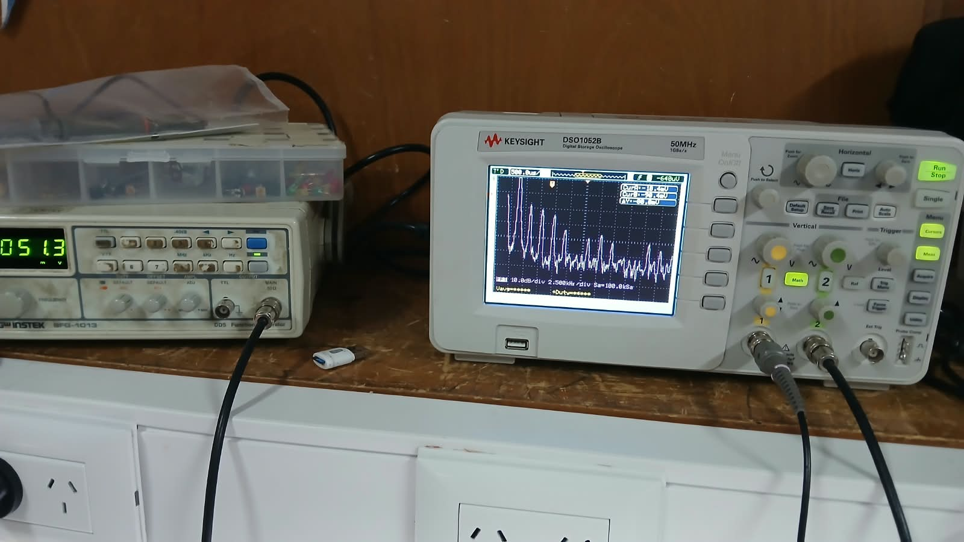
FotosMed/FFT/Dar/50dar.jpeg
