juan-felipe-castilla/TP2_Analogica/FotosMed/FFT/Dar/50darzoom.jpeg

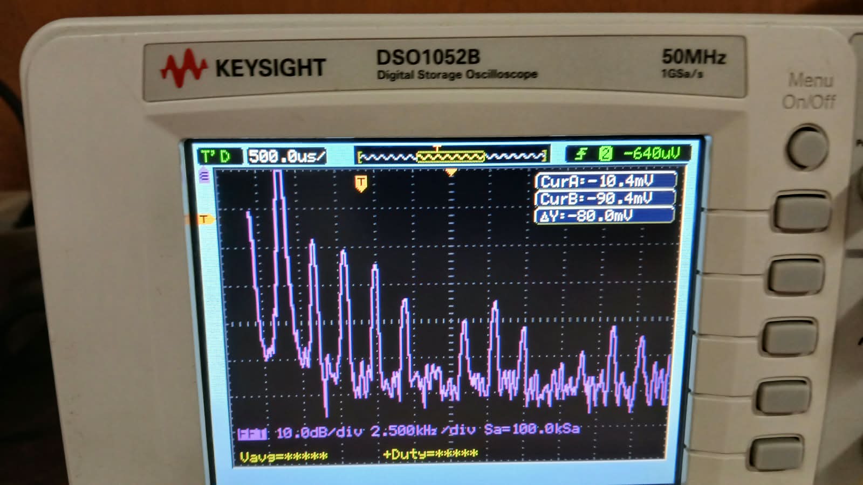
FotosMed/FFT/Dar/50darzoom.jpeg
