juan-felipe-castilla/TP2_Analogica/FotosMed/FFT/E12/2.5e12.jpeg

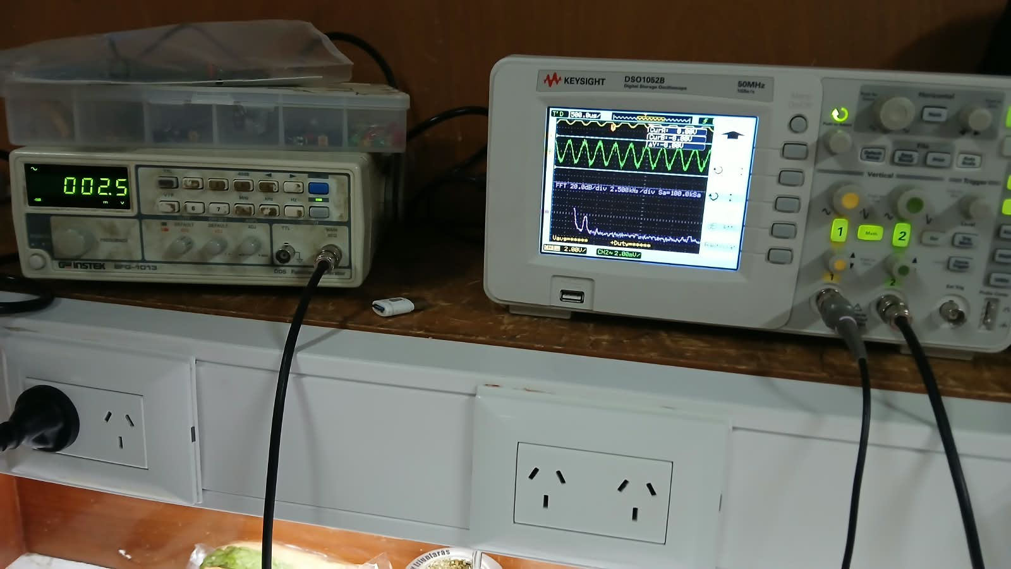
FotosMed/FFT/E12/2.5e12.jpeg
