juan-felipe-castilla/TP2_Analogica/FotosMed/FFT/E12/5e12aoom.jpeg

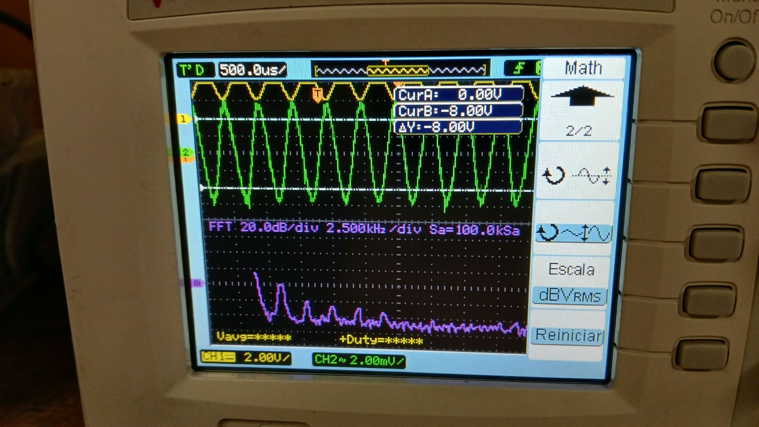
FotosMed/FFT/E12/5e12aoom.jpeg
