juan-felipe-castilla/TP2_Analogica/FotosMed/FFT/E12/10e12zoom.jpeg

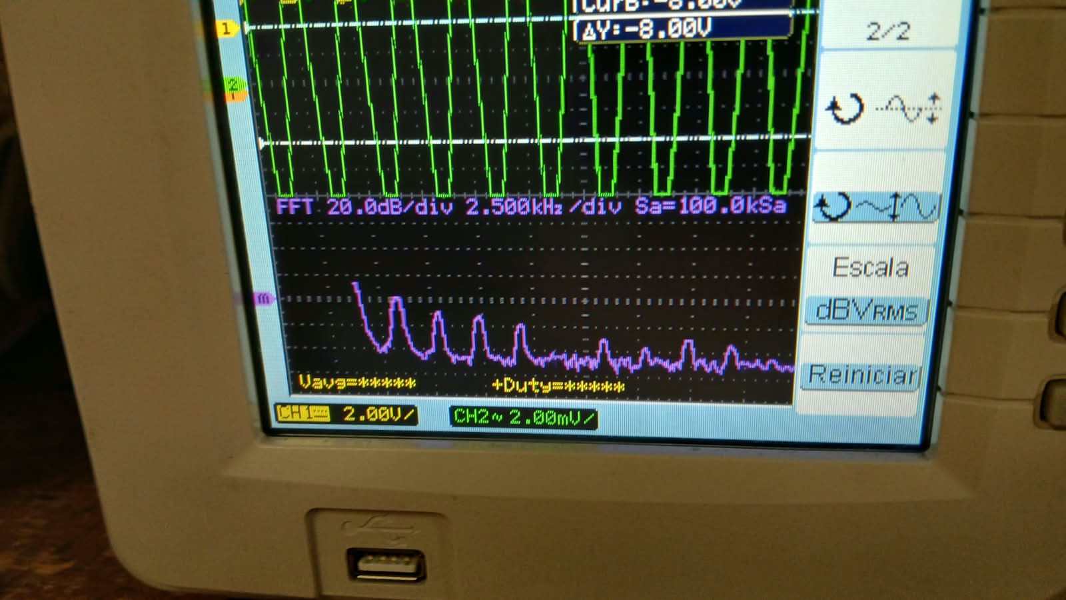
FotosMed/FFT/E12/10e12zoom.jpeg
