juan-felipe-castilla/TP2_Analogica/FotosMed/FFT/E12/25e12.jpeg

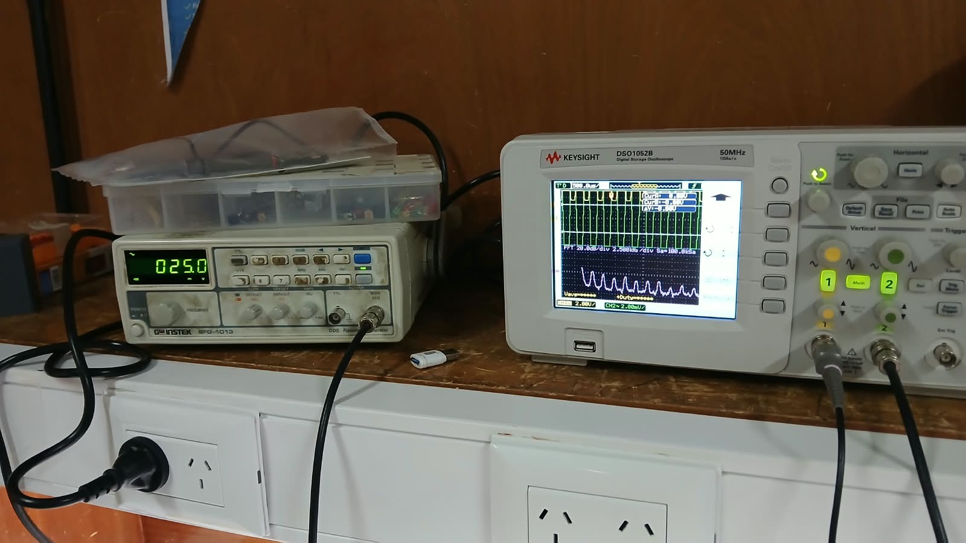
FotosMed/FFT/E12/25e12.jpeg
