juan-felipe-castilla/TP2_Analogica/FotosMed/FFT/E12/50e12.jpeg

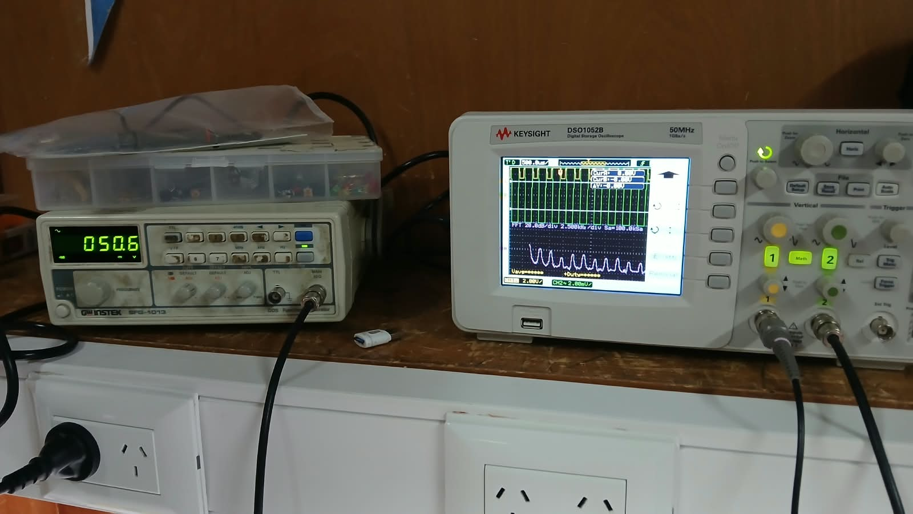
FotosMed/FFT/E12/50e12.jpeg
