juan-felipe-castilla/TP2_Analogica/FotosMed/FFT/E12/fotoMed.jpeg

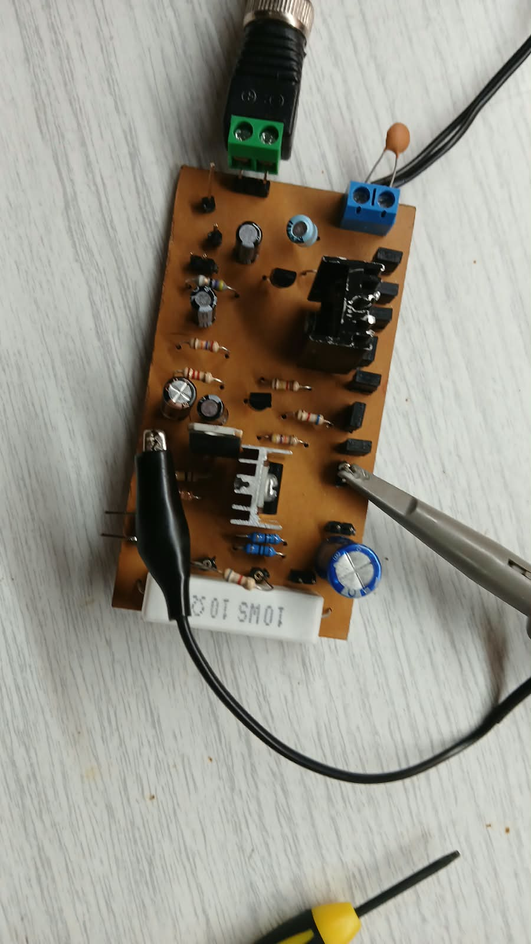
FotosMed/FFT/E12/fotoMed.jpeg
