juan-felipe-castilla/TP2_Analogica/FotosMed/Impedancias/z1ingen.jpeg

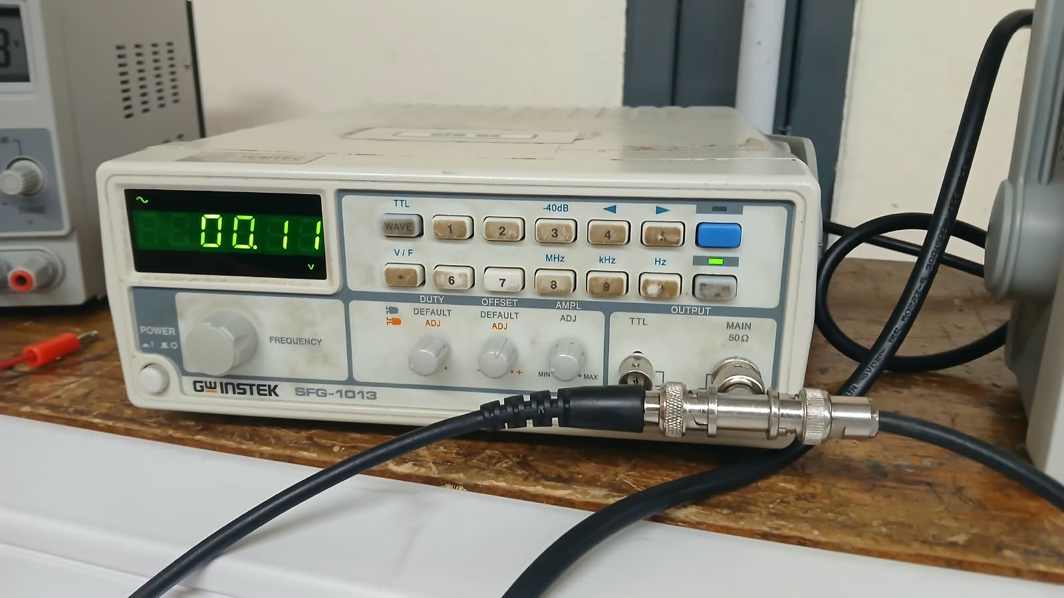
FotosMed/Impedancias/z1ingen.jpeg
