juan-felipe-castilla/TP2_Analogica/FotosMed/Impedancias/z1inmed.jpeg

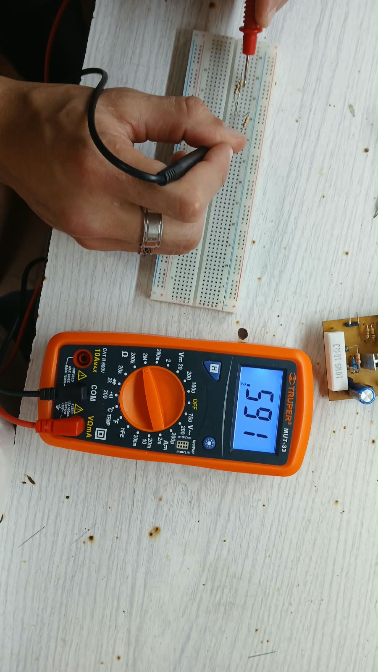
FotosMed/Impedancias/z1inmed.jpeg
