juan-felipe-castilla/TP2_Analogica/FotosMed/Impedancias/z1inoscilo.jpeg

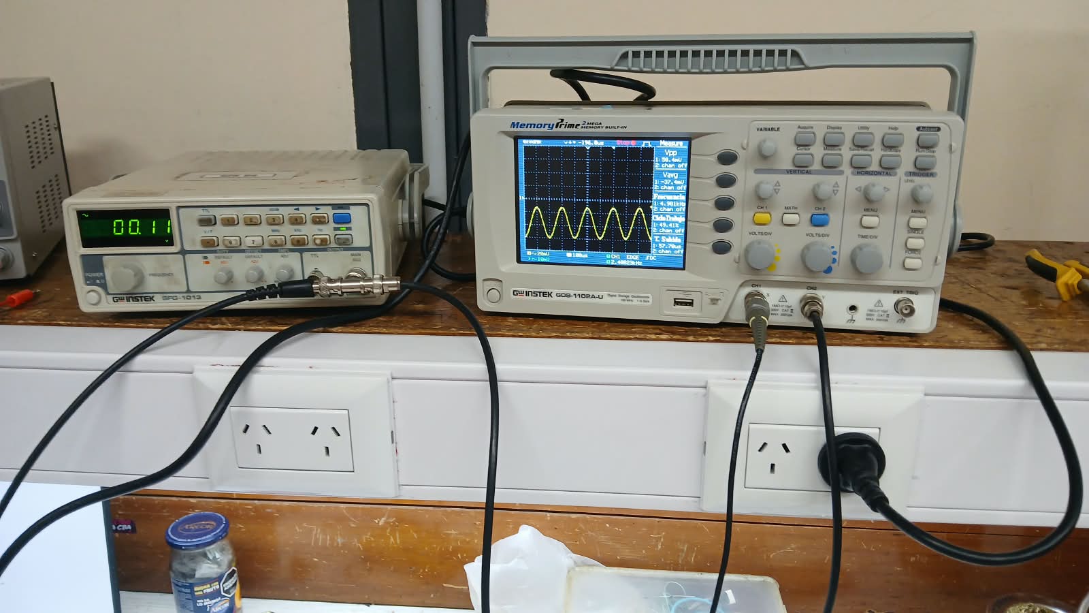
FotosMed/Impedancias/z1inoscilo.jpeg
