juan-felipe-castilla/TP2_Analogica/FotosMed/Impedancias/Z3INMED.jpeg

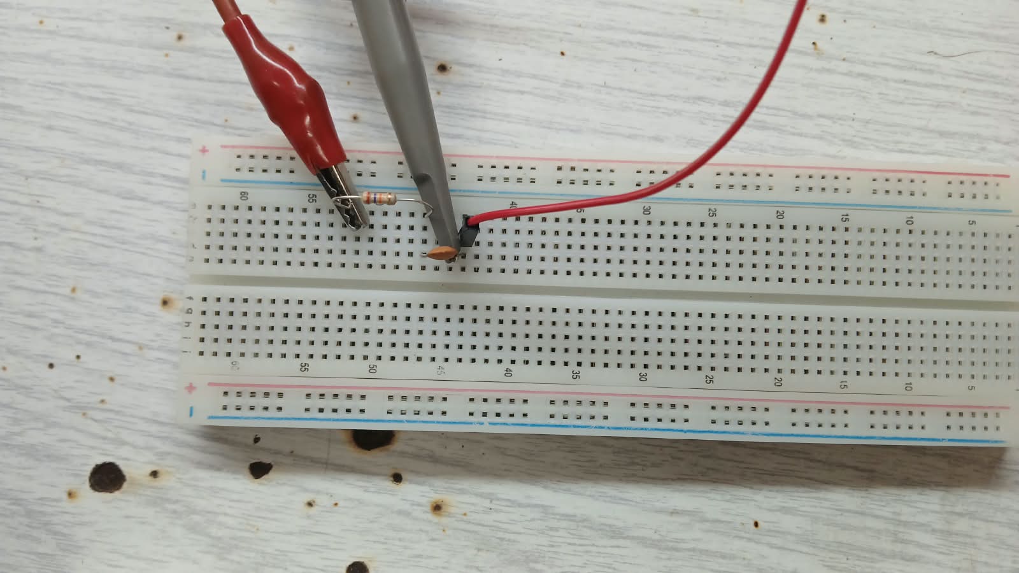
FotosMed/Impedancias/Z3INMED.jpeg
