juan-felipe-castilla/TP2_Analogica/FotosMed/Impedancias/Z3INOSCLI.jpeg

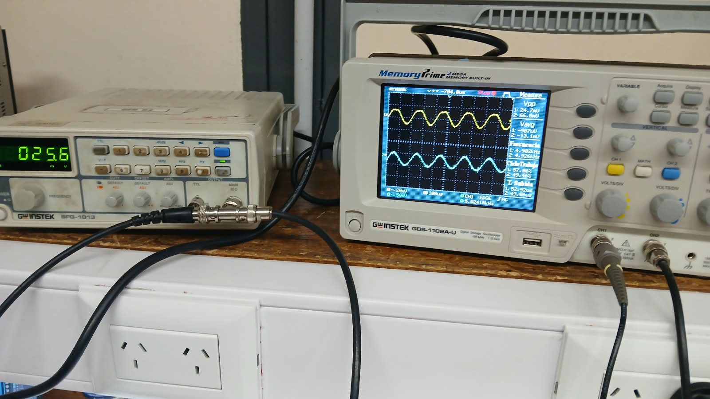
FotosMed/Impedancias/Z3INOSCLI.jpeg
