juan-felipe-castilla/TP2_Analogica/FotosMed/Impedancias/Z23INMED.jpeg

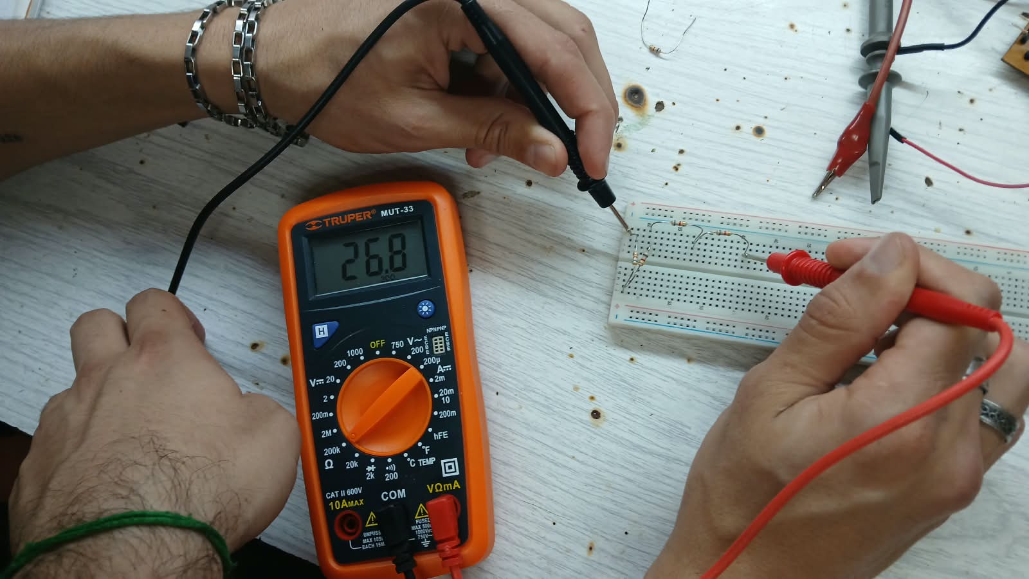
FotosMed/Impedancias/Z23INMED.jpeg
