juan-felipe-castilla/TP2_Analogica/FotosMed/Impedancias/Z23INOSCLI.jpeg

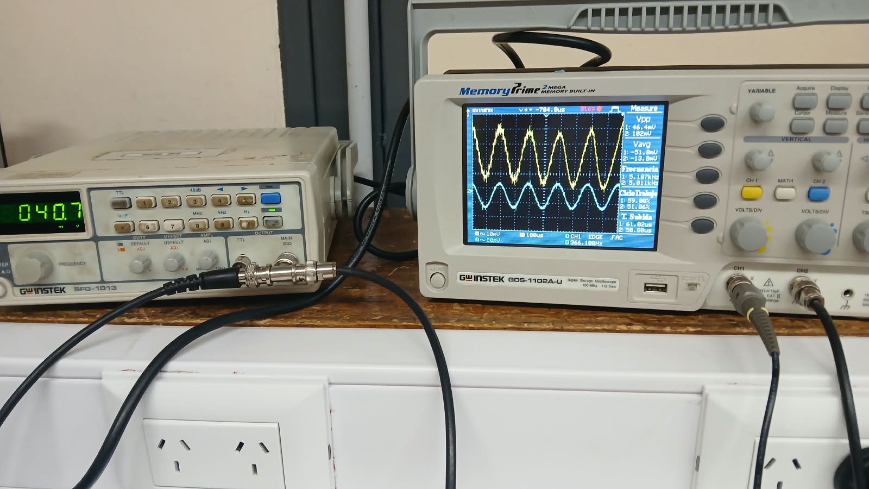
FotosMed/Impedancias/Z23INOSCLI.jpeg
