juan-felipe-castilla/TP2_Analogica/FotosMed/Impedancias/Z23INPLACA.jpeg

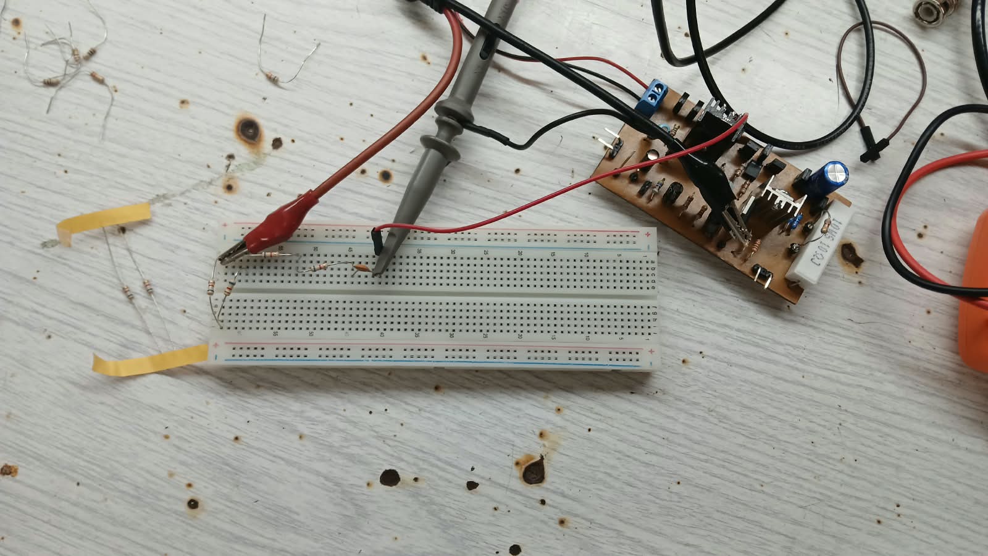
FotosMed/Impedancias/Z23INPLACA.jpeg
