juan-felipe-castilla/TP2_Analogica/FotosMed/Impedancias/ZIN1MED.jpeg

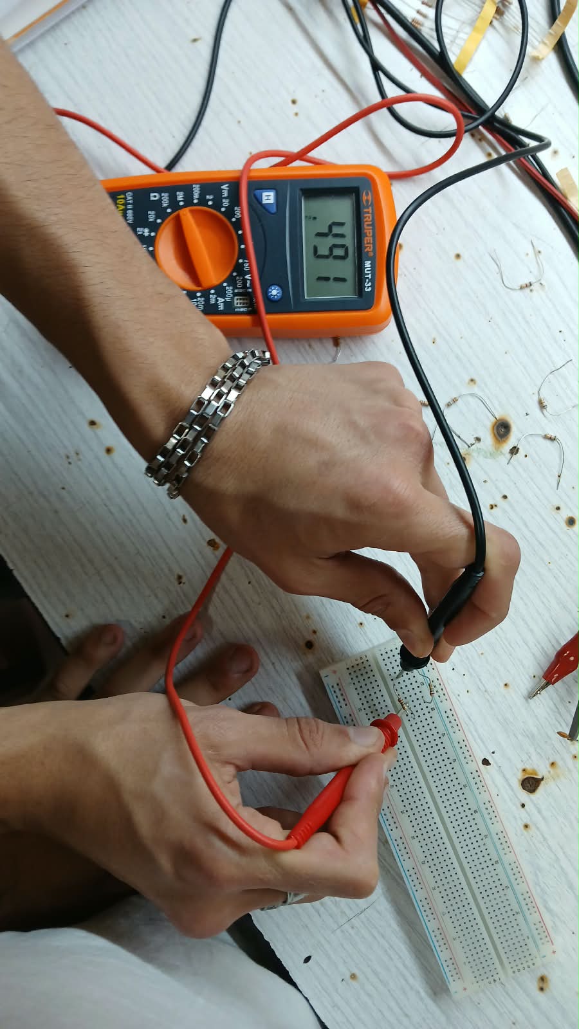
FotosMed/Impedancias/ZIN1MED.jpeg
