juan-felipe-castilla/TP2_Analogica/FotosMed/Impedancias/ZIN12.jpeg

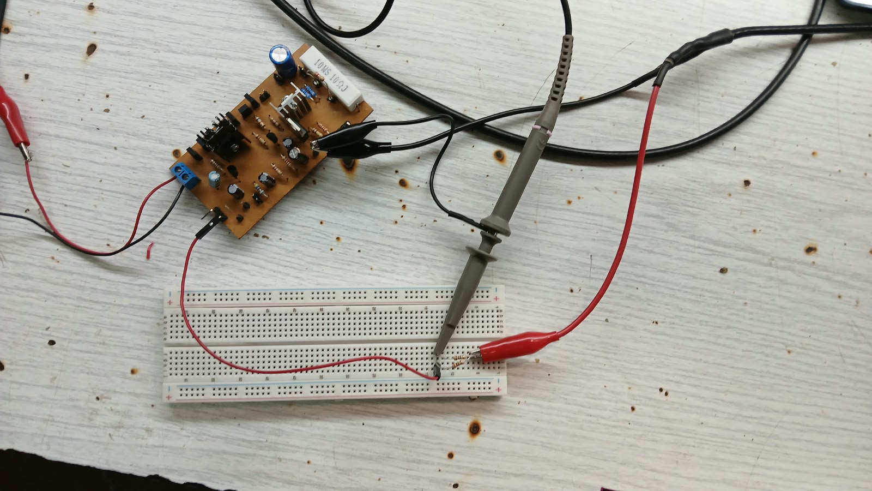
FotosMed/Impedancias/ZIN12.jpeg
