juan-felipe-castilla/TP2_Analogica/FotosMed/Impedancias/ZIN12MED.jpeg

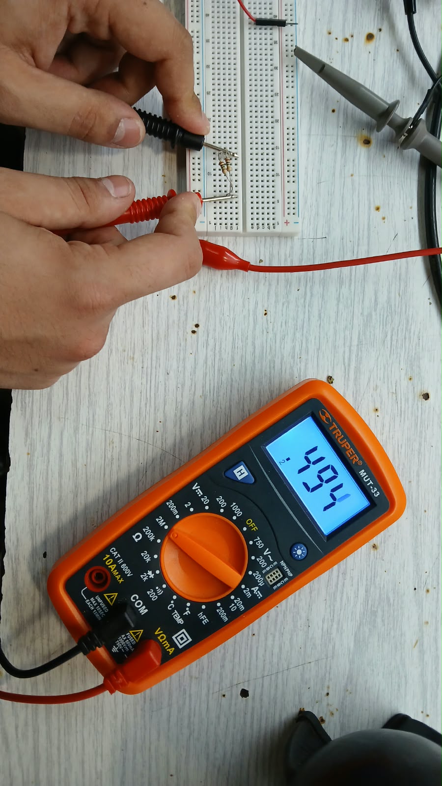
FotosMed/Impedancias/ZIN12MED.jpeg
