juan-felipe-castilla/TP2_Analogica/FotosMed/Impedancias/ZIN12OSCILO.jpeg

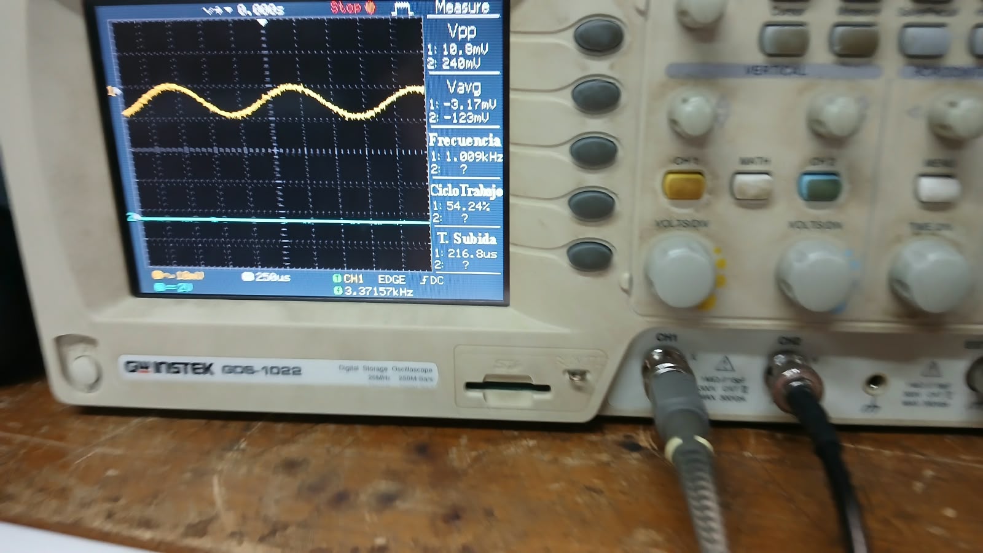
FotosMed/Impedancias/ZIN12OSCILO.jpeg
