juan-felipe-castilla/TP2_Analogica/FotosMed/Impedancias/zinMed.jpeg

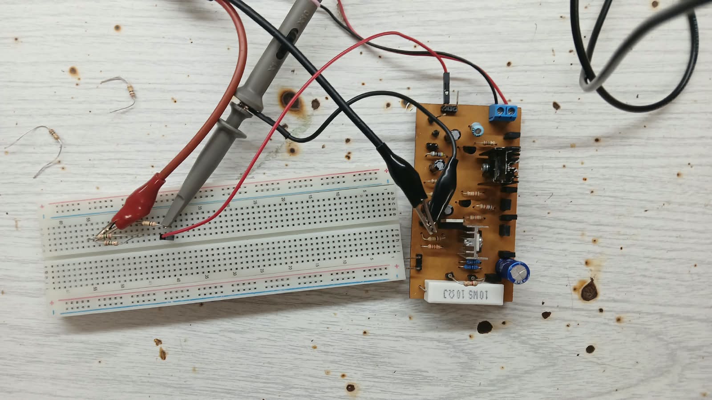
FotosMed/Impedancias/zinMed.jpeg
