juan-felipe-castilla/TP2_Analogica/FotosMed/Impedancias/ZINTOTAL.jpeg

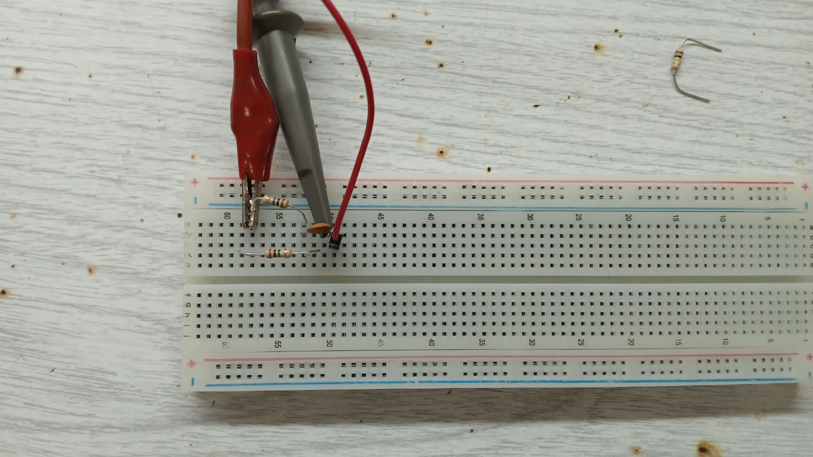
FotosMed/Impedancias/ZINTOTAL.jpeg
