juan-felipe-castilla/TP2_Analogica/FotosMed/Impedancias/ZINTOTALSOCLO.jpeg

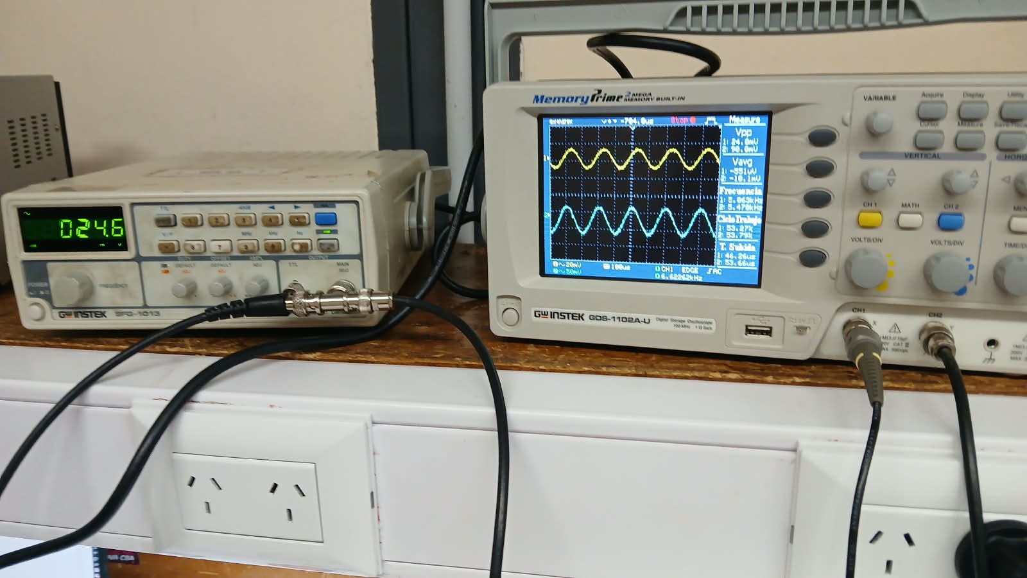
FotosMed/Impedancias/ZINTOTALSOCLO.jpeg
