juan-felipe-castilla/TP2_Analogica/FotosMed/Impedancias/ZINTOTALZOOM.jpeg

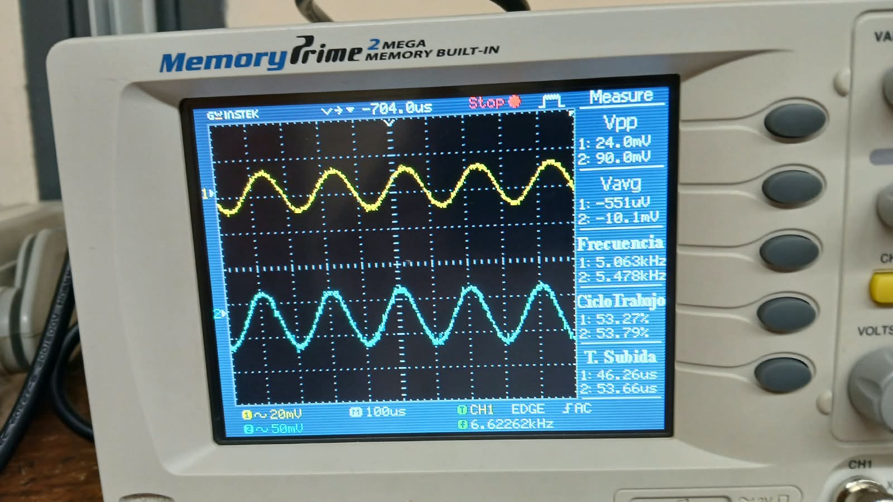
FotosMed/Impedancias/ZINTOTALZOOM.jpeg
