juan-felipe-castilla/TP2_Analogica/FotosMed/Impedancias/Zout1.jpeg

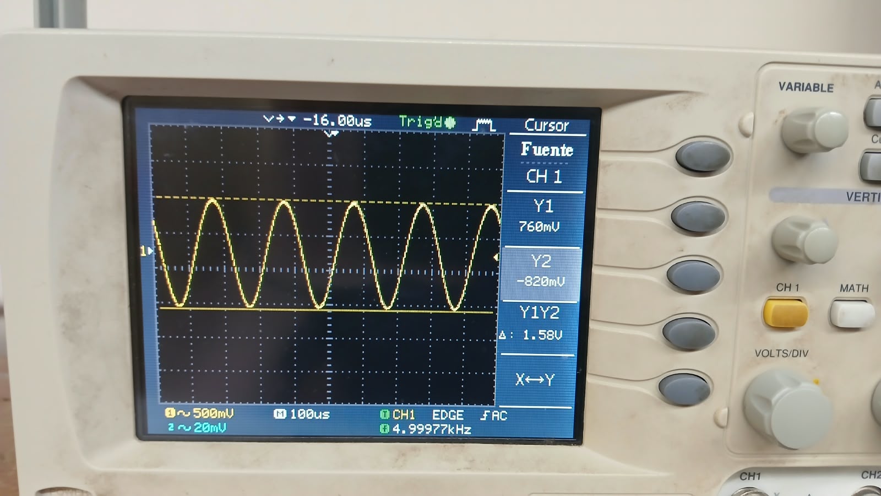
FotosMed/Impedancias/Zout1.jpeg
