juan-felipe-castilla/TP2_Analogica/FotosMed/Impedancias/Zout2.jpeg

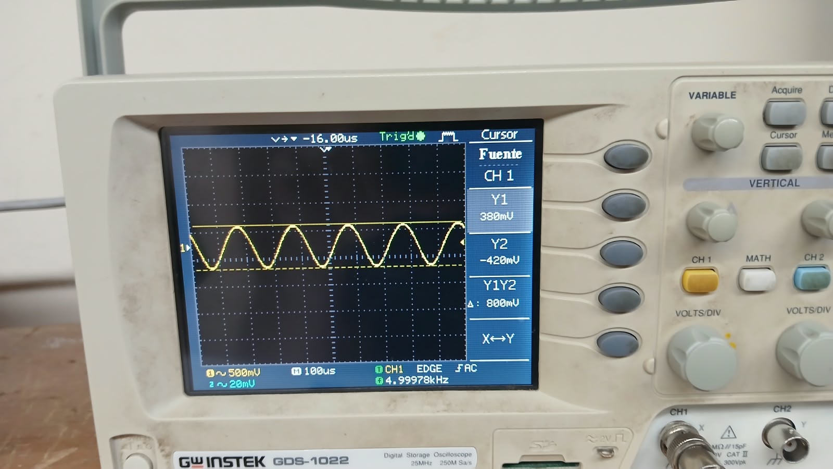
FotosMed/Impedancias/Zout2.jpeg
