juan-felipe-castilla/TP2_Analogica/FotosMed/Impedancias/Zoutmed.jpeg

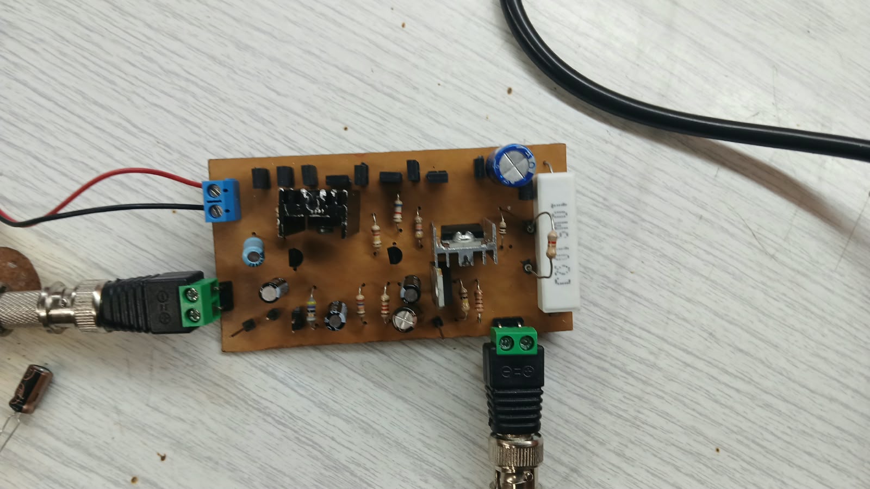
FotosMed/Impedancias/Zoutmed.jpeg
