juan-felipe-castilla/TP2_Analogica/FotosMed/Voltajesycargademuerte/ABAJOE1.jpeg

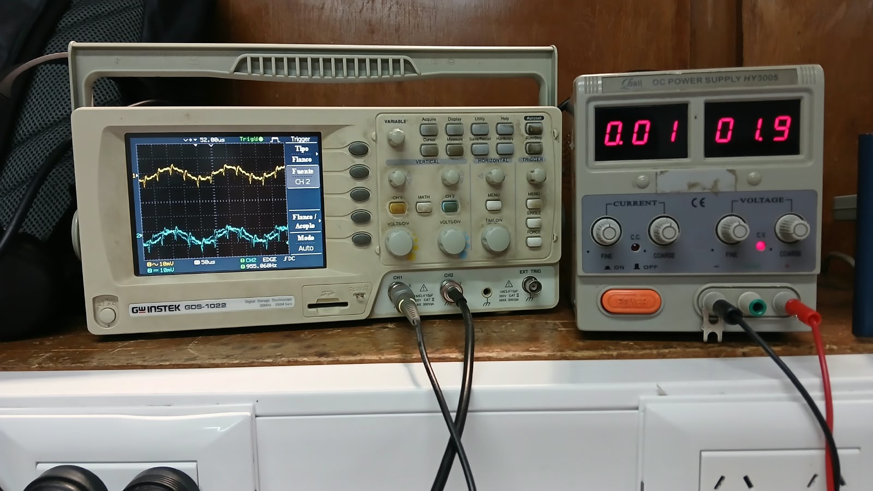
FotosMed/Voltajesycargademuerte/ABAJOE1.jpeg
