juan-felipe-castilla/TP2_Analogica/FotosMed/Voltajesycargademuerte/ABAJOE12.jpeg

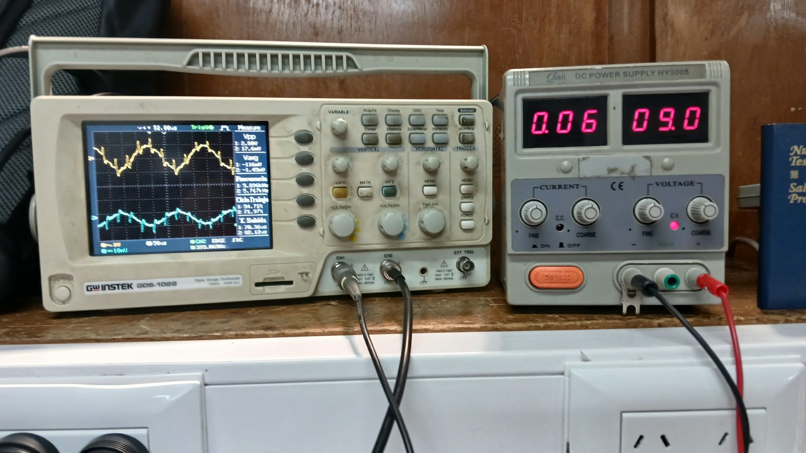
FotosMed/Voltajesycargademuerte/ABAJOE12.jpeg
