juan-felipe-castilla/TP2_Analogica/FotosMed/Voltajesycargademuerte/ABAJOE123.jpeg

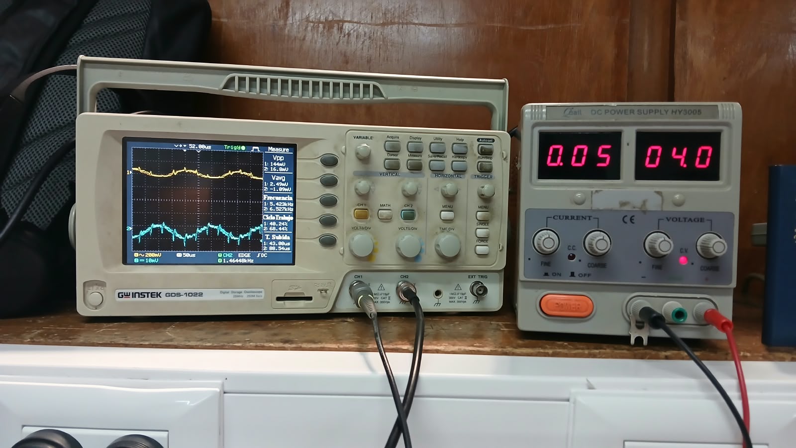
FotosMed/Voltajesycargademuerte/ABAJOE123.jpeg
