juan-felipe-castilla/TP2_Analogica/FotosMed/Voltajesycargademuerte/ARRIBAE1.jpeg

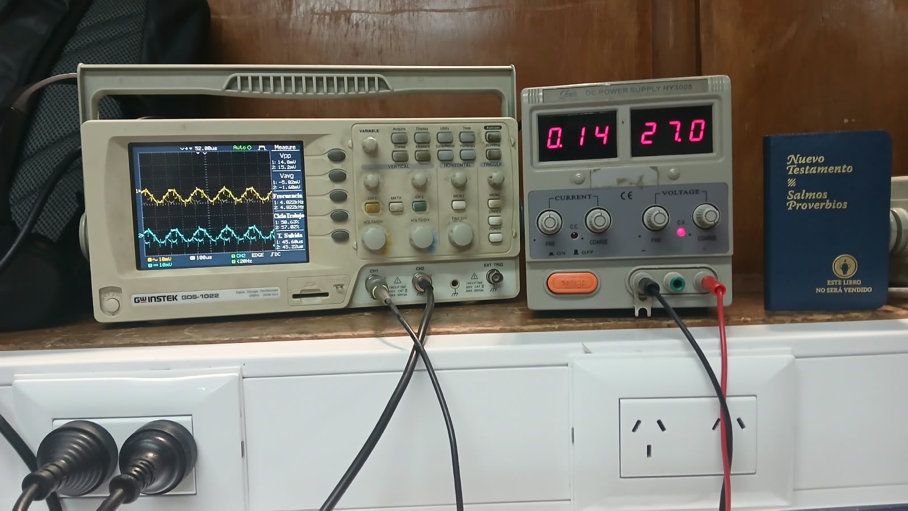
FotosMed/Voltajesycargademuerte/ARRIBAE1.jpeg
