juan-felipe-castilla/TP2_Analogica/FotosMed/Voltajesycargademuerte/ARRIBAE12.jpeg

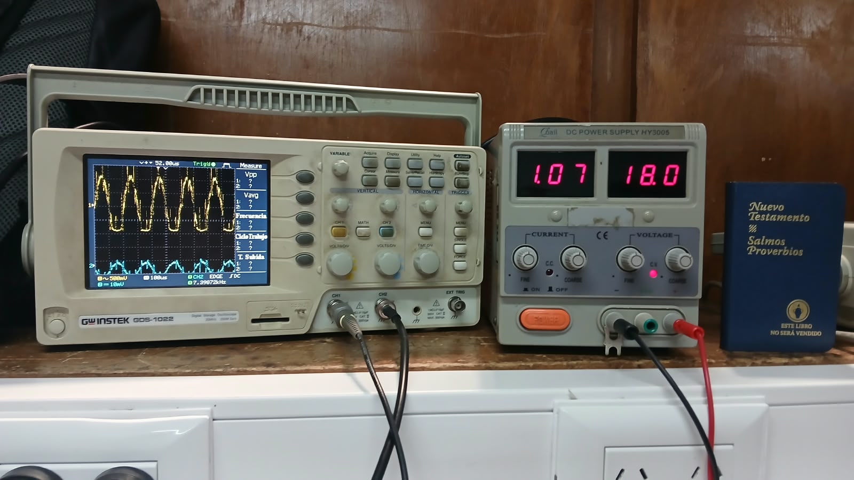
FotosMed/Voltajesycargademuerte/ARRIBAE12.jpeg
