juan-felipe-castilla/TP2_Analogica/FotosMed/Voltajesycargademuerte/ARRIBAE123.jpeg

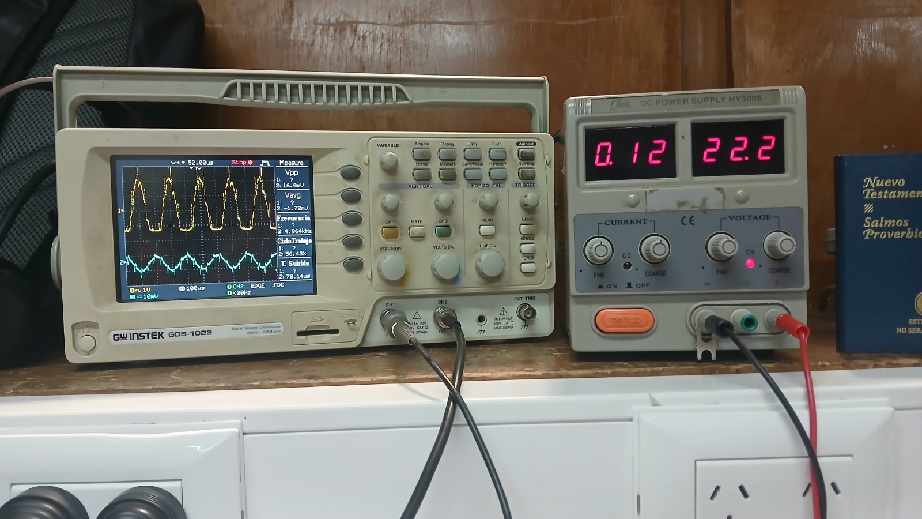
FotosMed/Voltajesycargademuerte/ARRIBAE123.jpeg
