juan-felipe-castilla/TP2_Analogica/FotosMed/Voltajesycargademuerte/BuenHombreExplotado.jpeg

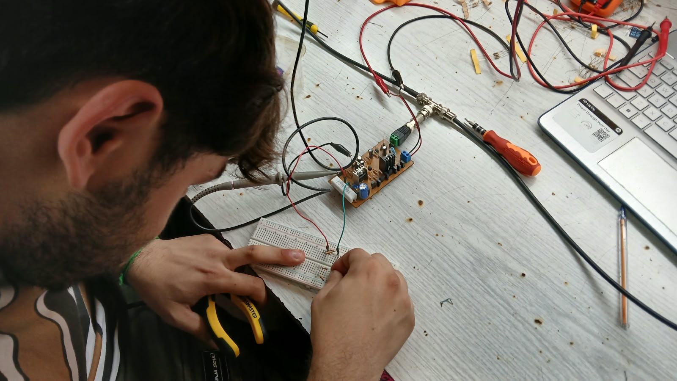
FotosMed/Voltajesycargademuerte/BuenHombreExplotado.jpeg
