juan-felipe-castilla/TP2_Analogica/FotosMed/Voltajesycargademuerte/OSCRMUERTE.jpeg

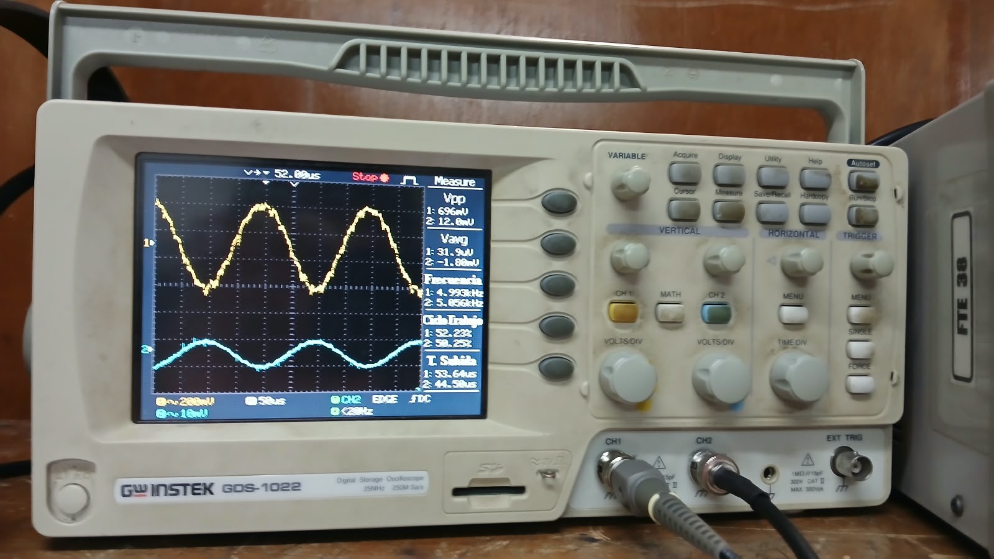
FotosMed/Voltajesycargademuerte/OSCRMUERTE.jpeg
