juan-felipe-castilla/TP2_Analogica/FotosMed/Voltajesycargademuerte/RMUERTE.jpeg

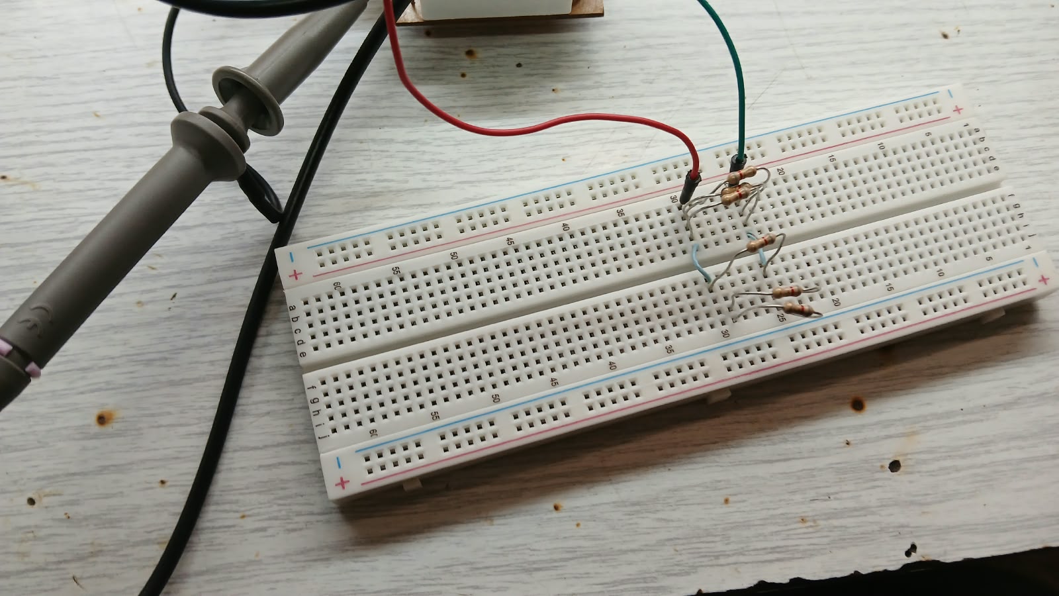
FotosMed/Voltajesycargademuerte/RMUERTE.jpeg
