juan-felipe-castilla/TP2_Analogica/FotosMed/Voltajesycargademuerte/RMUERTEIN.jpeg

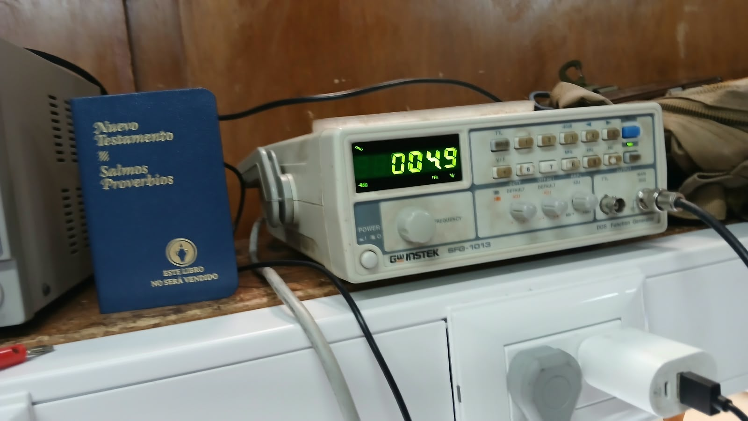
FotosMed/Voltajesycargademuerte/RMUERTEIN.jpeg
