juan-felipe-castilla/TP2_Analogica/Simu/BW-DARLINTONG-DB.jpg

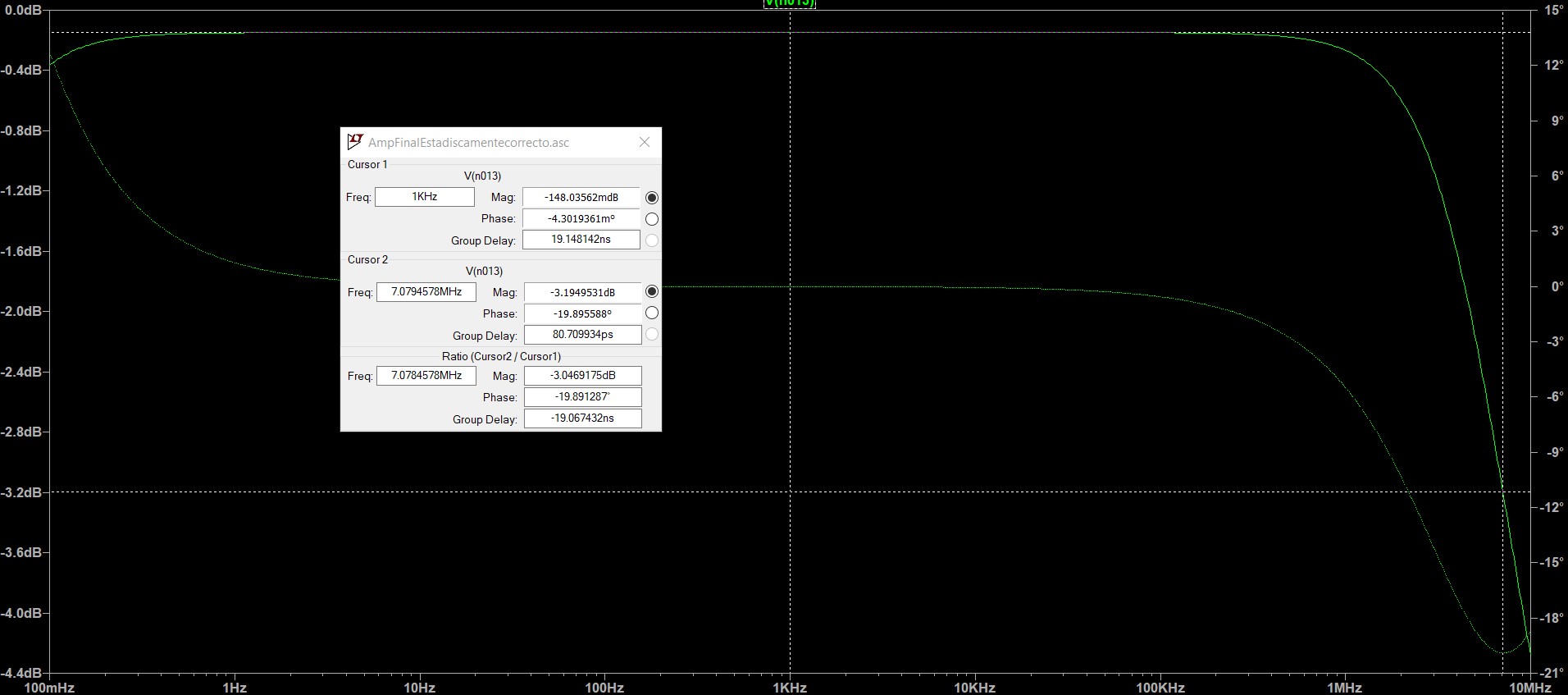
Simu/BW-DARLINTONG-DB.jpg
