juan-felipe-castilla/TP2_Analogica/Simu/BW-DARLINTONLINEAL.jpg

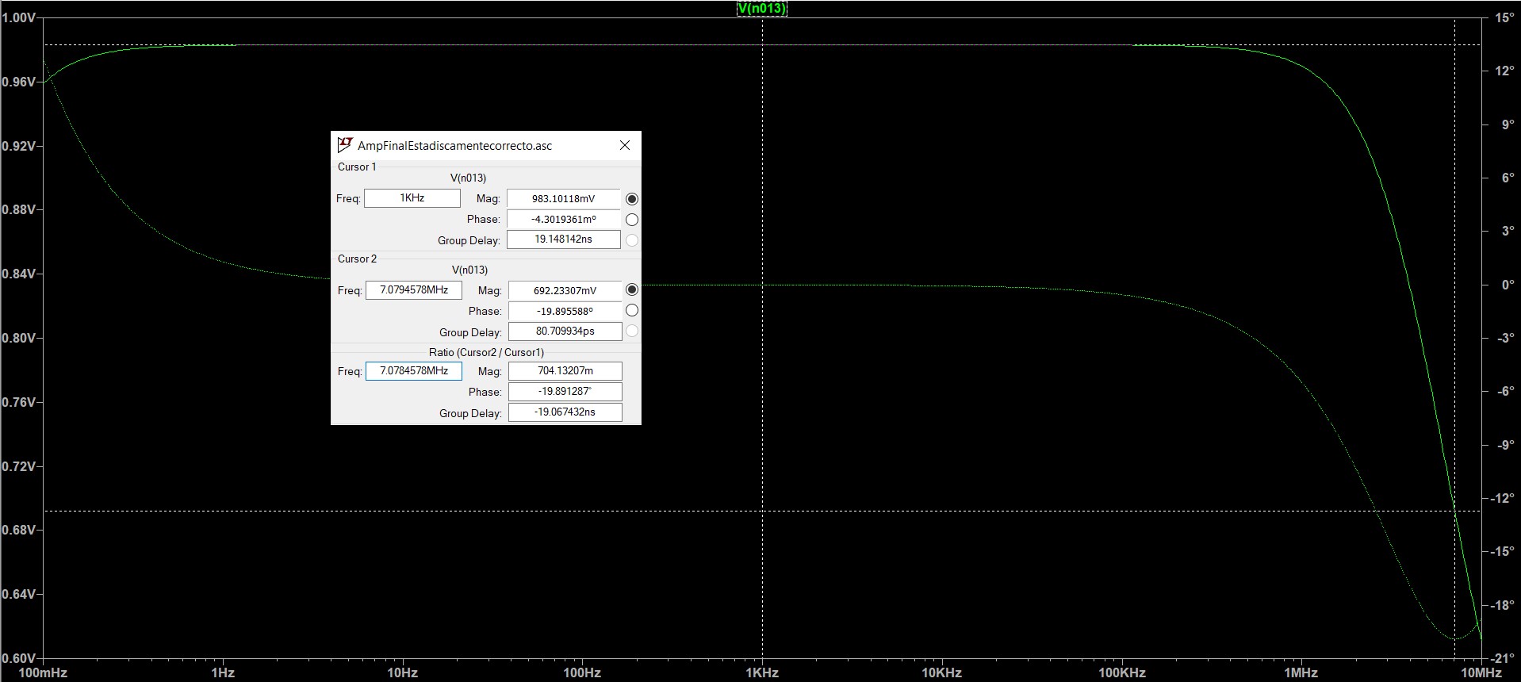
Simu/BW-DARLINTONLINEAL.jpg
