juan-felipe-castilla/TP2_Analogica/Simu/BW-EMISOR.jpg

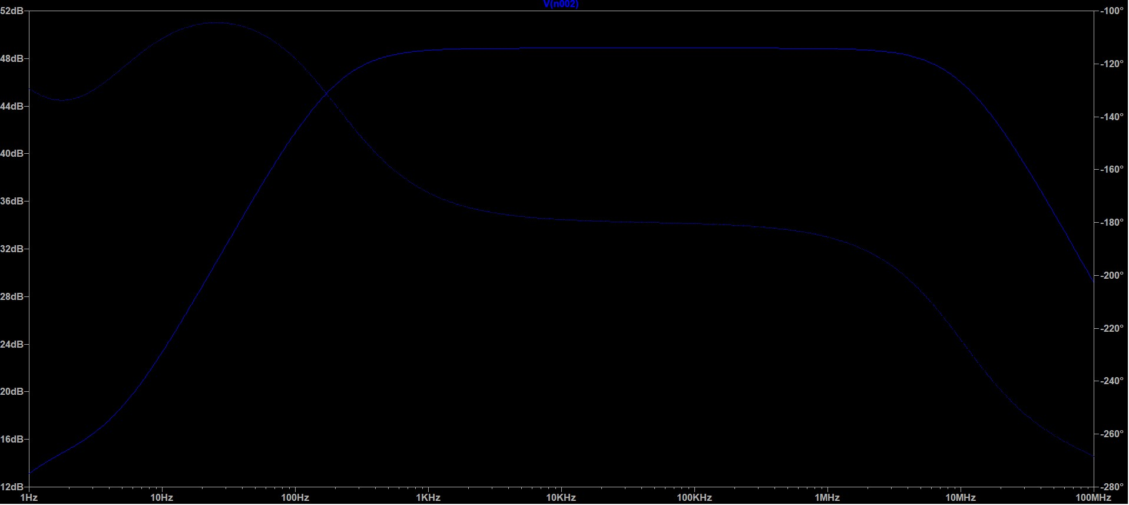
Simu/BW-EMISOR.jpg
