juan-felipe-castilla/TP2_Analogica/Simu/BW-LimiteDerecho.jpg

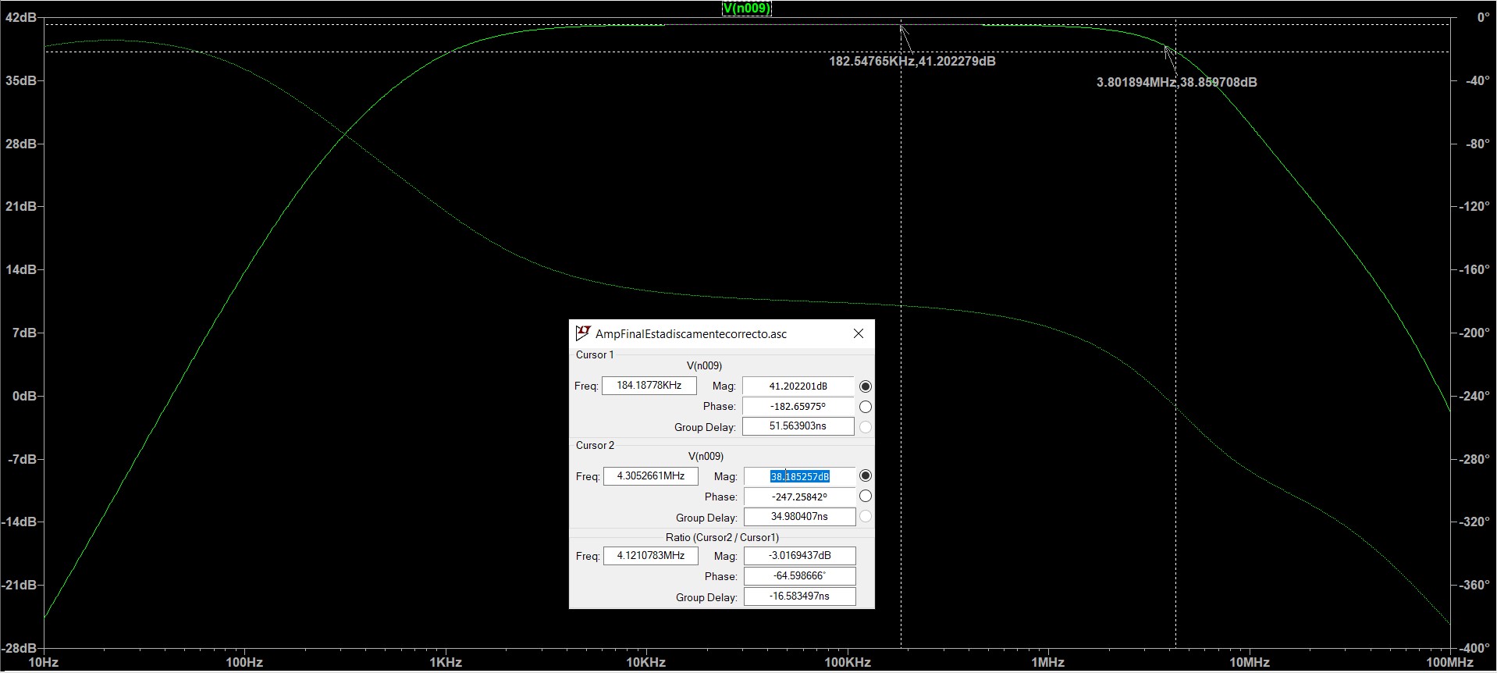
Simu/BW-LimiteDerecho.jpg
