juan-felipe-castilla/TP2_Analogica/Simu/BW-LimiteIzquierdo.jpg

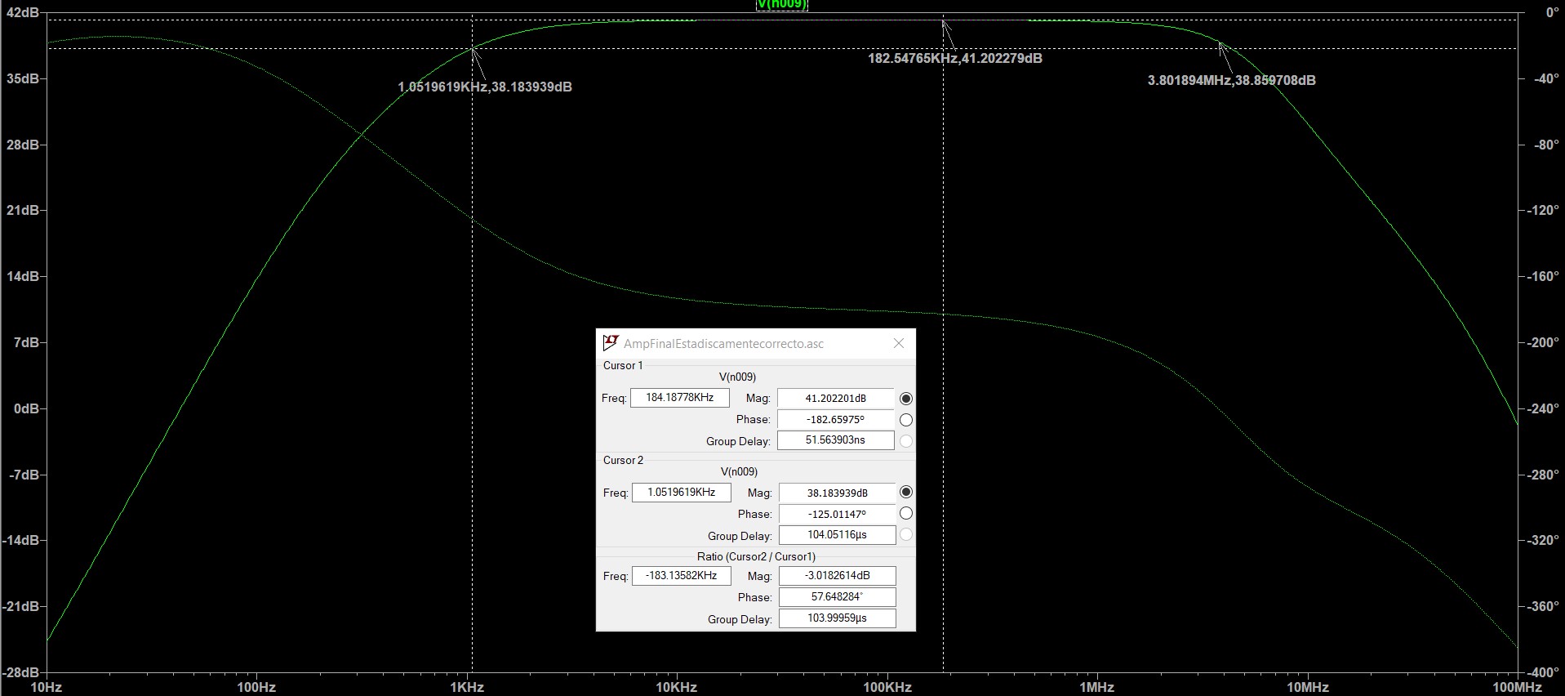
Simu/BW-LimiteIzquierdo.jpg
