juan-felipe-castilla/TP2_Analogica/Simu/BW-SQL.jpg

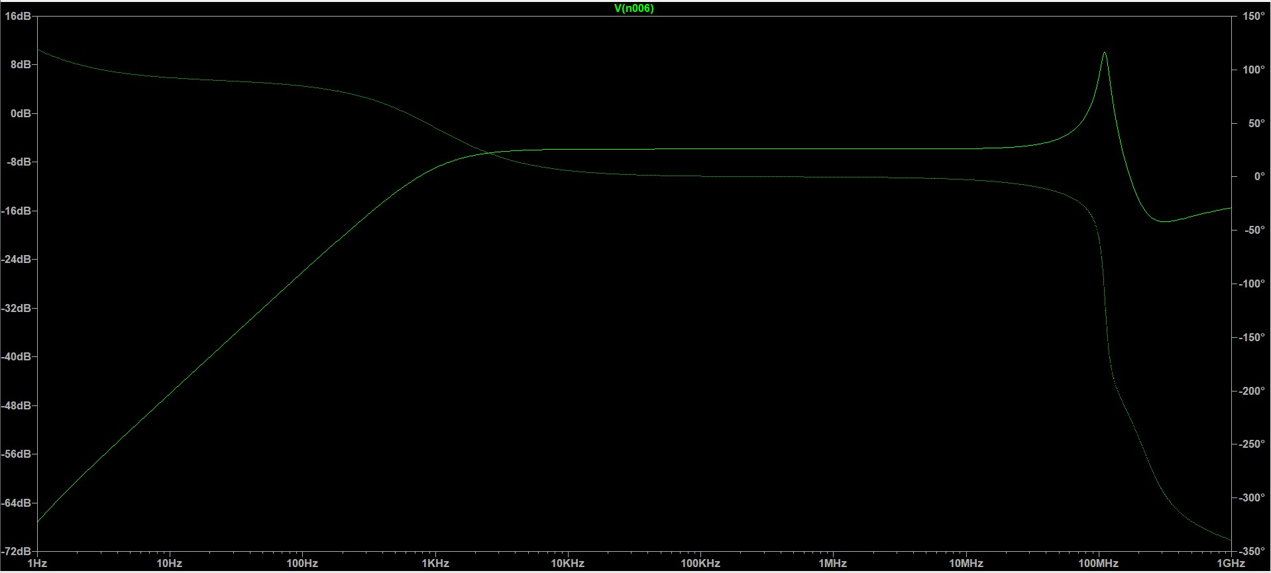
Simu/BW-SQL.jpg
