juan-felipe-castilla/TP2_Analogica/Simu/Circuito_fuenteoff.jpg

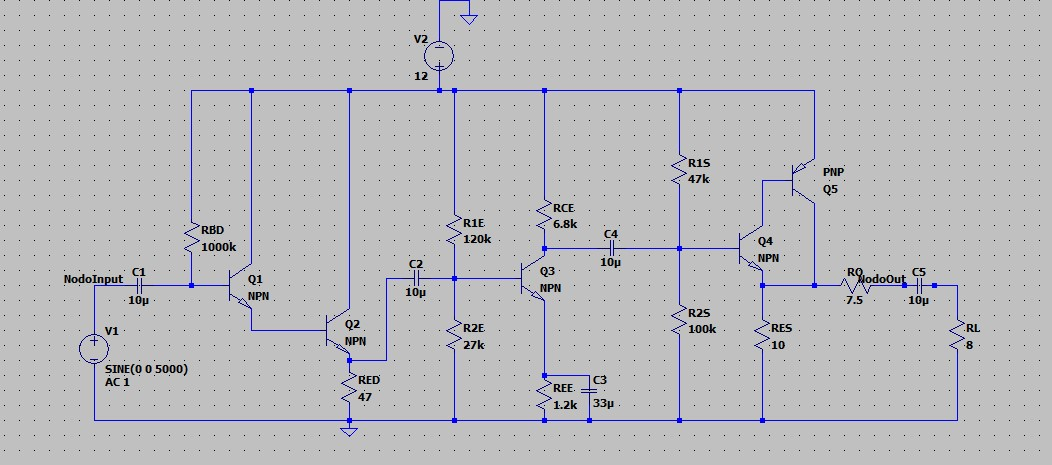
Simu/Circuito_fuenteoff.jpg
