juan-felipe-castilla/TP2_Analogica/Simu/CurvaZ23.jpg

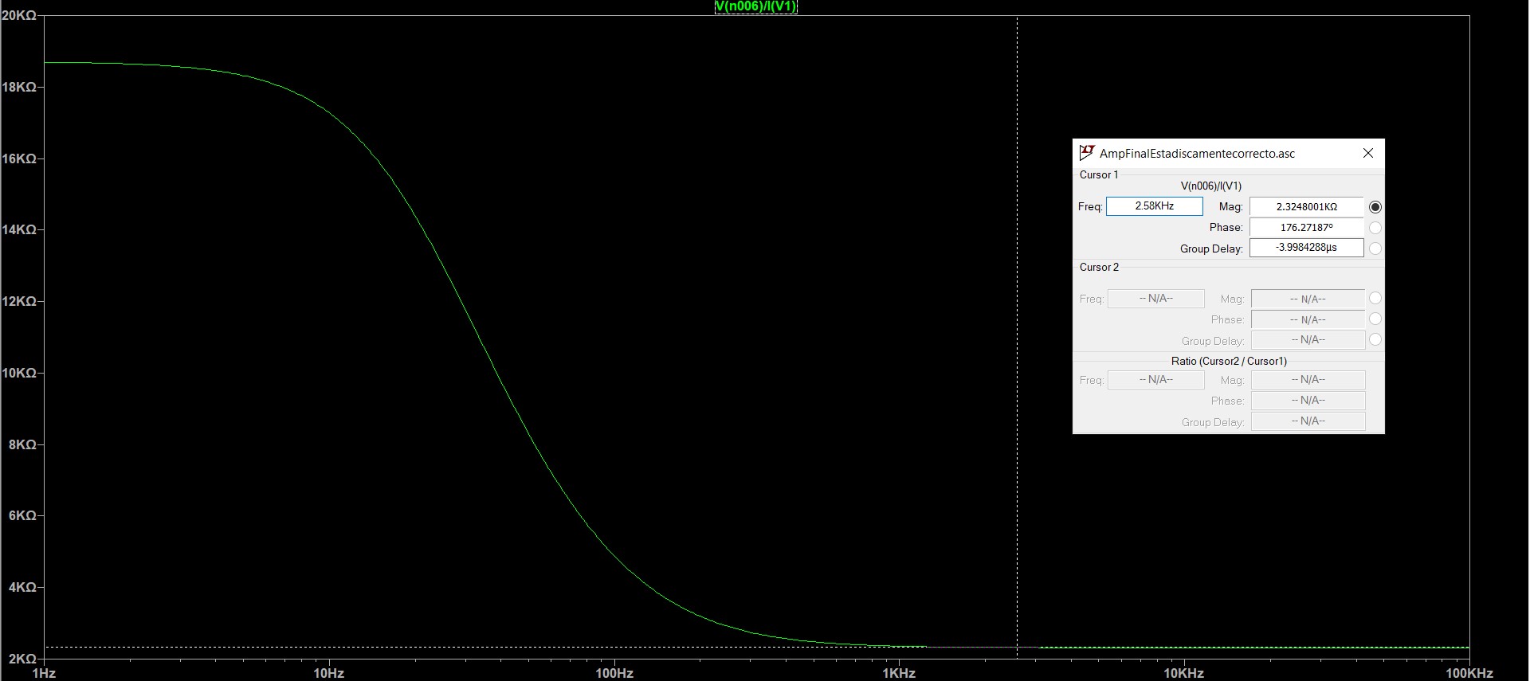
Simu/CurvaZ23.jpg
