juan-felipe-castilla/TP2_Analogica/Simu/Darlinton.jpg

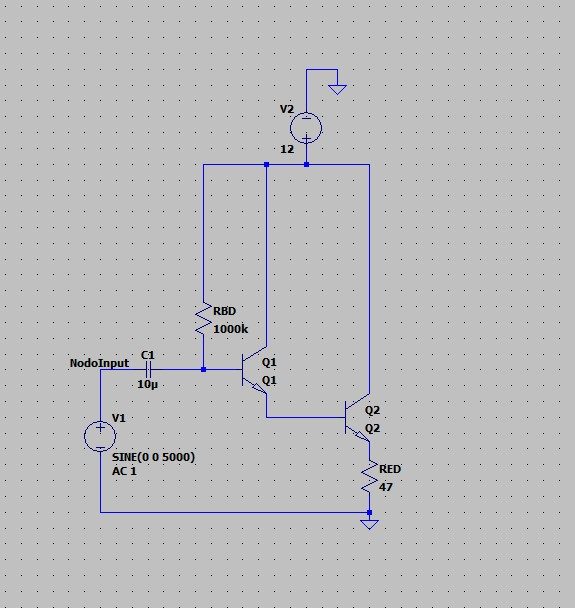
Simu/Darlinton.jpg
