juan-felipe-castilla/TP2_Analogica/Simu/E1E2_AISLADO.jpg

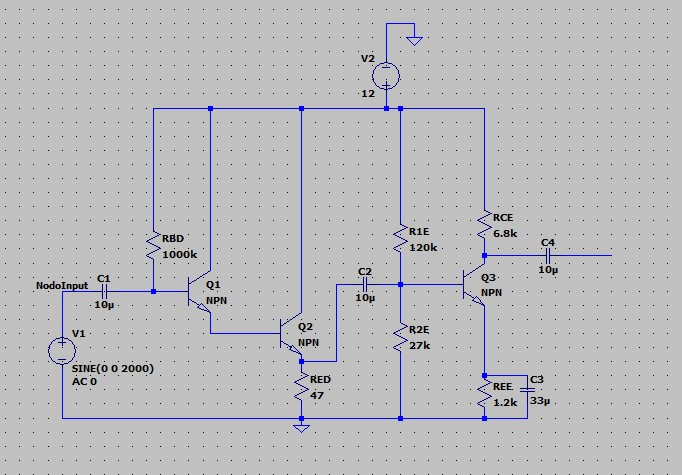
Simu/E1E2_AISLADO.jpg
