juan-felipe-castilla/TP2_Analogica/Simu/E1E2_ZIN.jpg

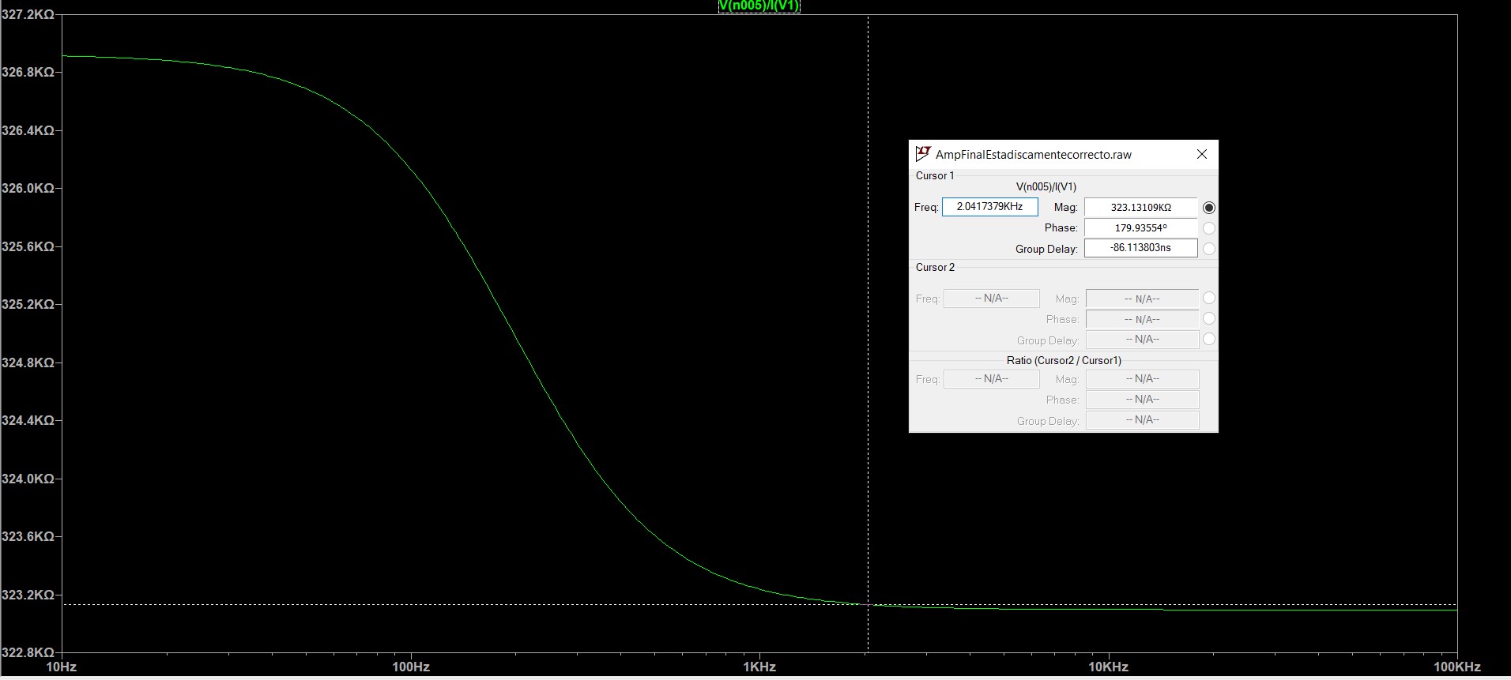
Simu/E1E2_ZIN.jpg
