juan-felipe-castilla/TP2_Analogica/Simu/E1E2_ZOUT.jpg

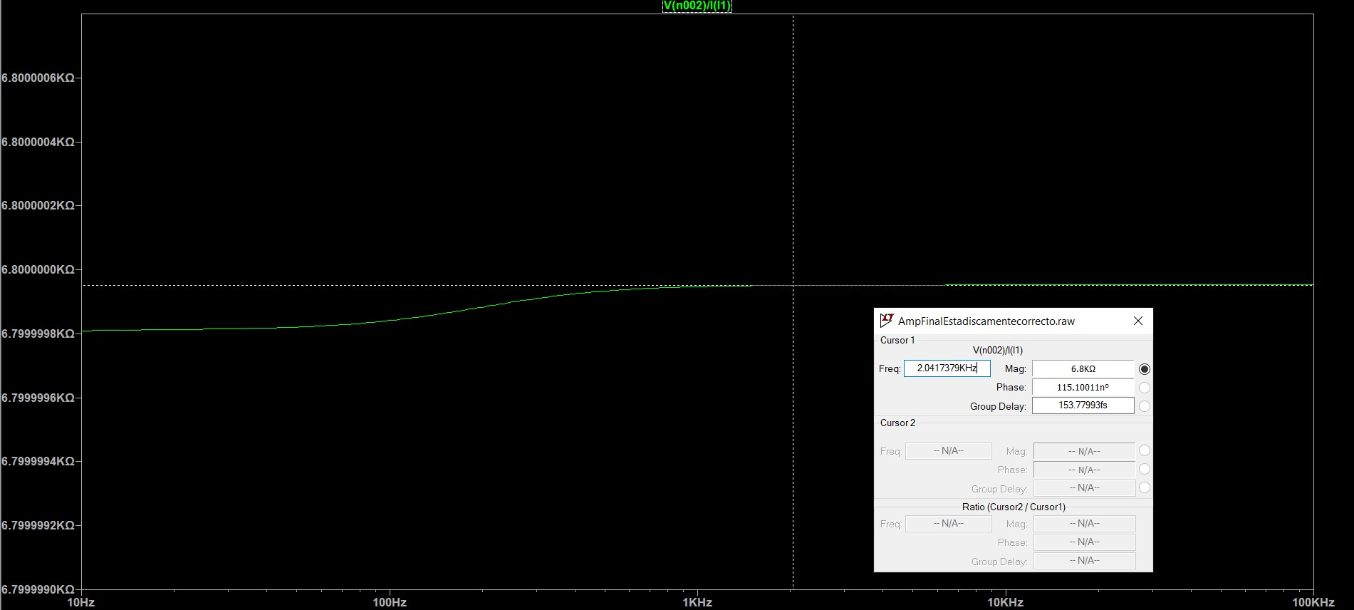
Simu/E1E2_ZOUT.jpg
