juan-felipe-castilla/TP2_Analogica/Simu/E1E2_ZOUTMED.jpg

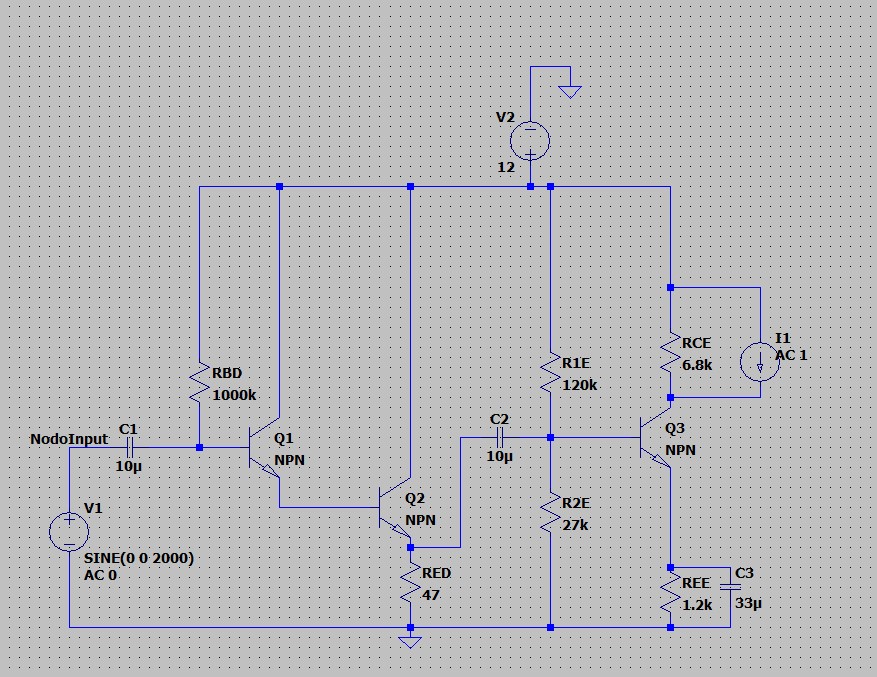
Simu/E1E2_ZOUTMED.jpg
