juan-felipe-castilla/TP2_Analogica/Simu/E23ZIN.jpg

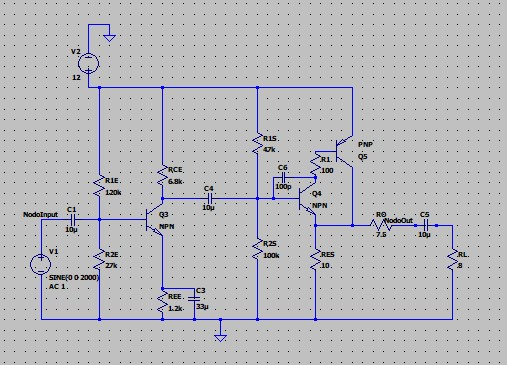
Simu/E23ZIN.jpg
