juan-felipe-castilla/TP2_Analogica/Simu/Emisor_Aislado.jpg

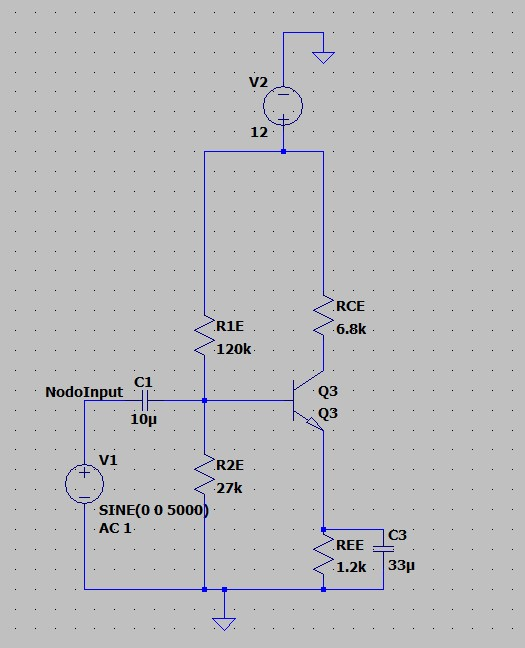
Simu/Emisor_Aislado.jpg
