juan-felipe-castilla/TP2_Analogica/Simu/Emisor_Zout.jpg

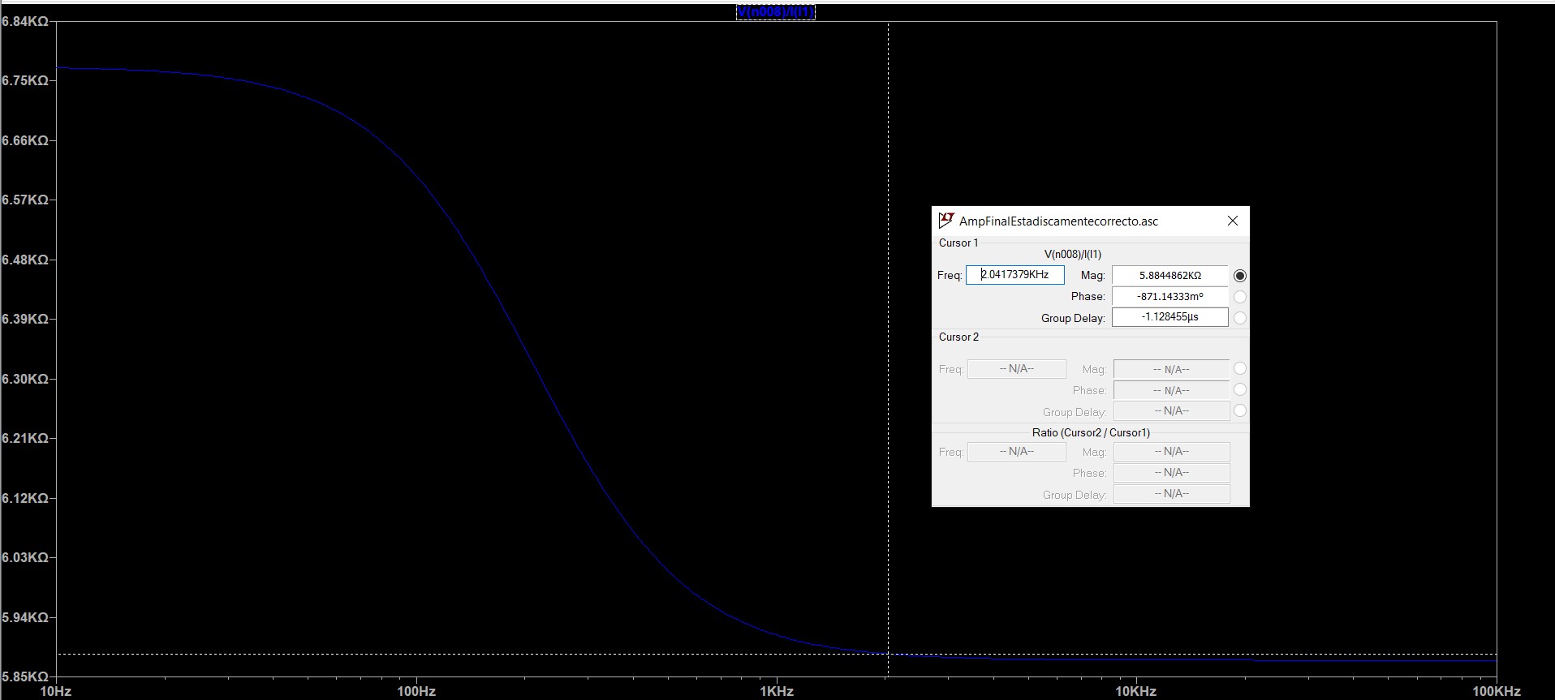
Simu/Emisor_Zout.jpg
