juan-felipe-castilla/TP2_Analogica/Simu/EmisorZOUT_CIRCUITO.jpg

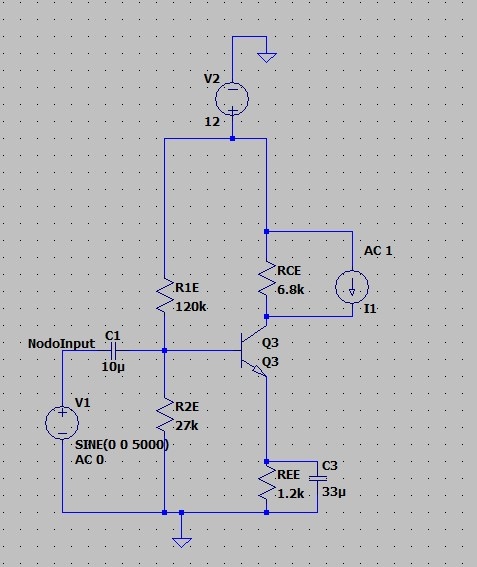
Simu/EmisorZOUT_CIRCUITO.jpg
