juan-felipe-castilla/TP2_Analogica/Simu/Ganancia_simulada.jpg

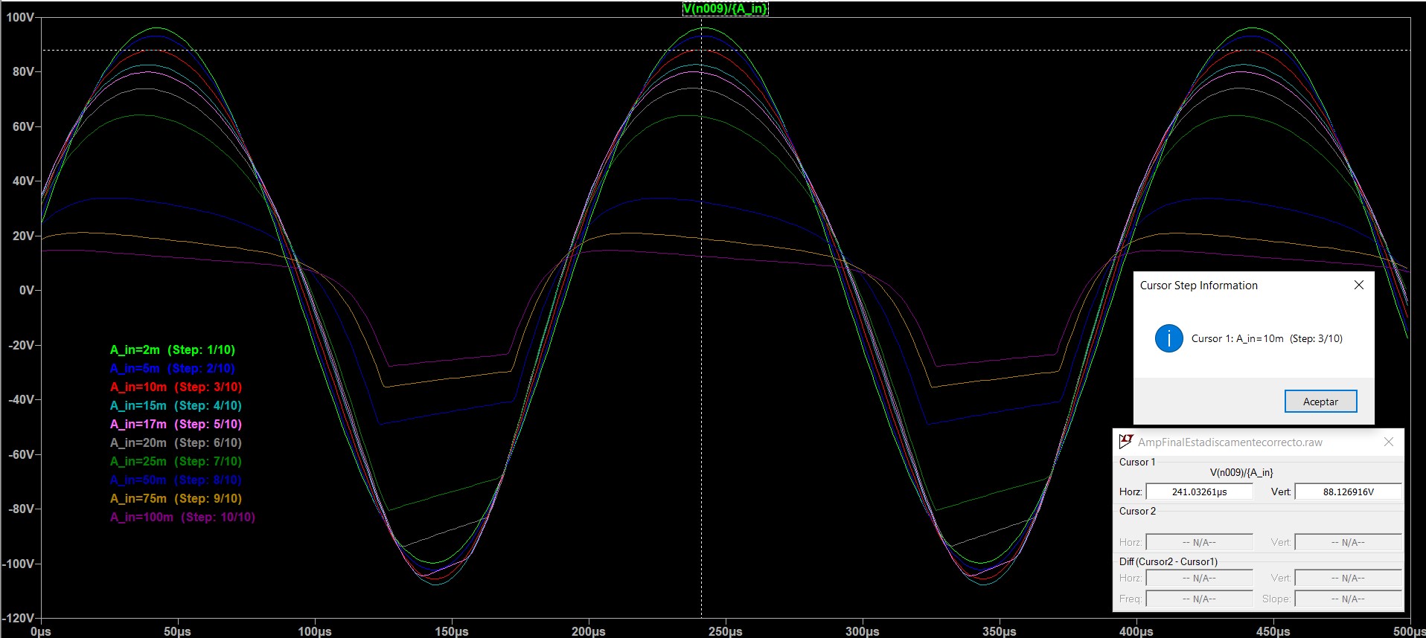
Simu/Ganancia_simulada.jpg
