juan-felipe-castilla/TP2_Analogica/Simu/Impedancia_Entrada_Total.jpg

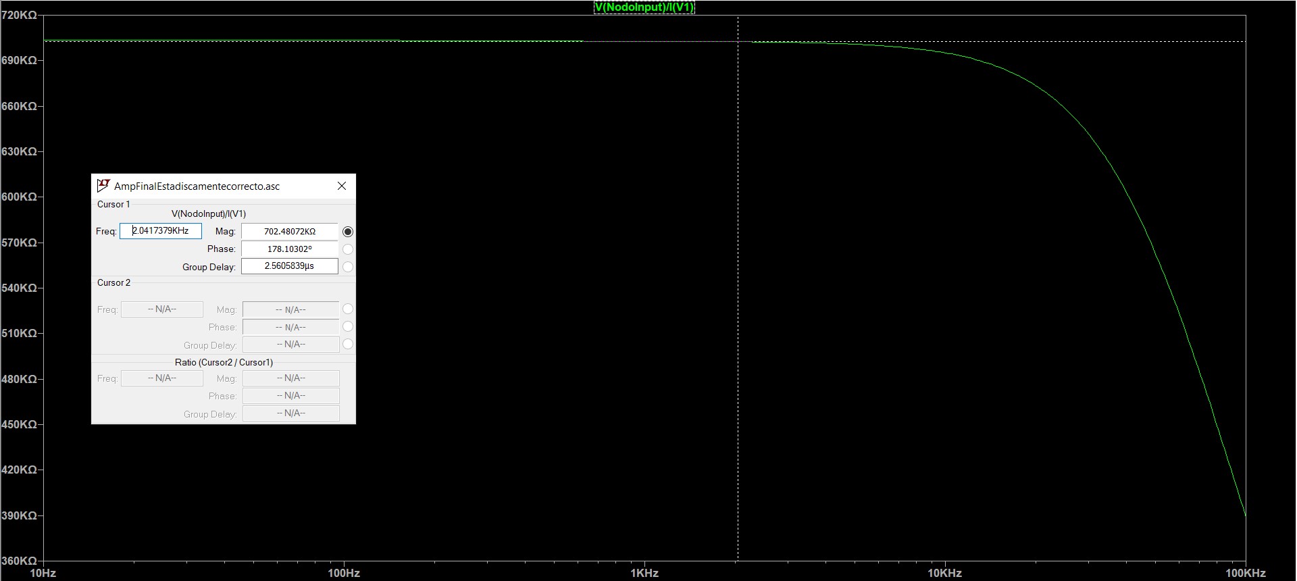
Simu/Impedancia_Entrada_Total.jpg
