juan-felipe-castilla/TP2_Analogica/Simu/Impedancia_Salida_Ciurcuito.jpg

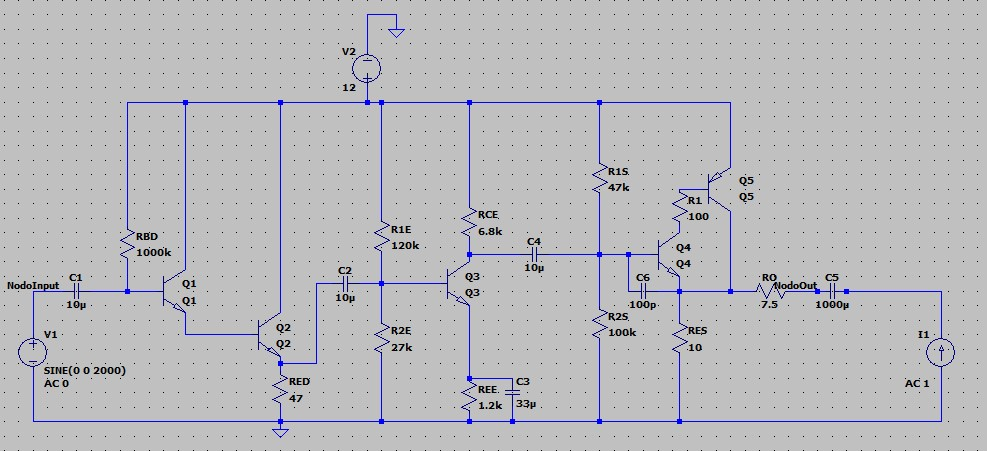
Simu/Impedancia_Salida_Ciurcuito.jpg
