juan-felipe-castilla/TP2_Analogica/Simu/ImpedanciaIN_Darlinton.jpg

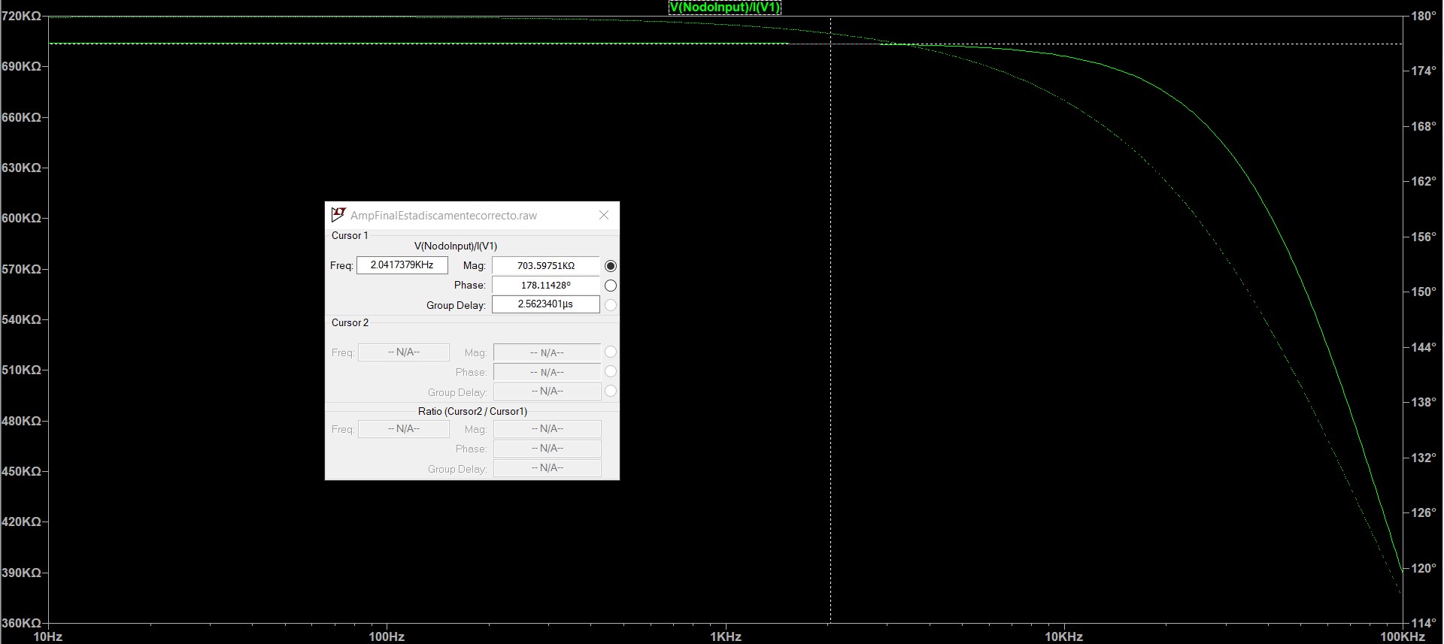
Simu/ImpedanciaIN_Darlinton.jpg
