juan-felipe-castilla/TP2_Analogica/Simu/ImpedanciaOUT_Darlinton.jpg

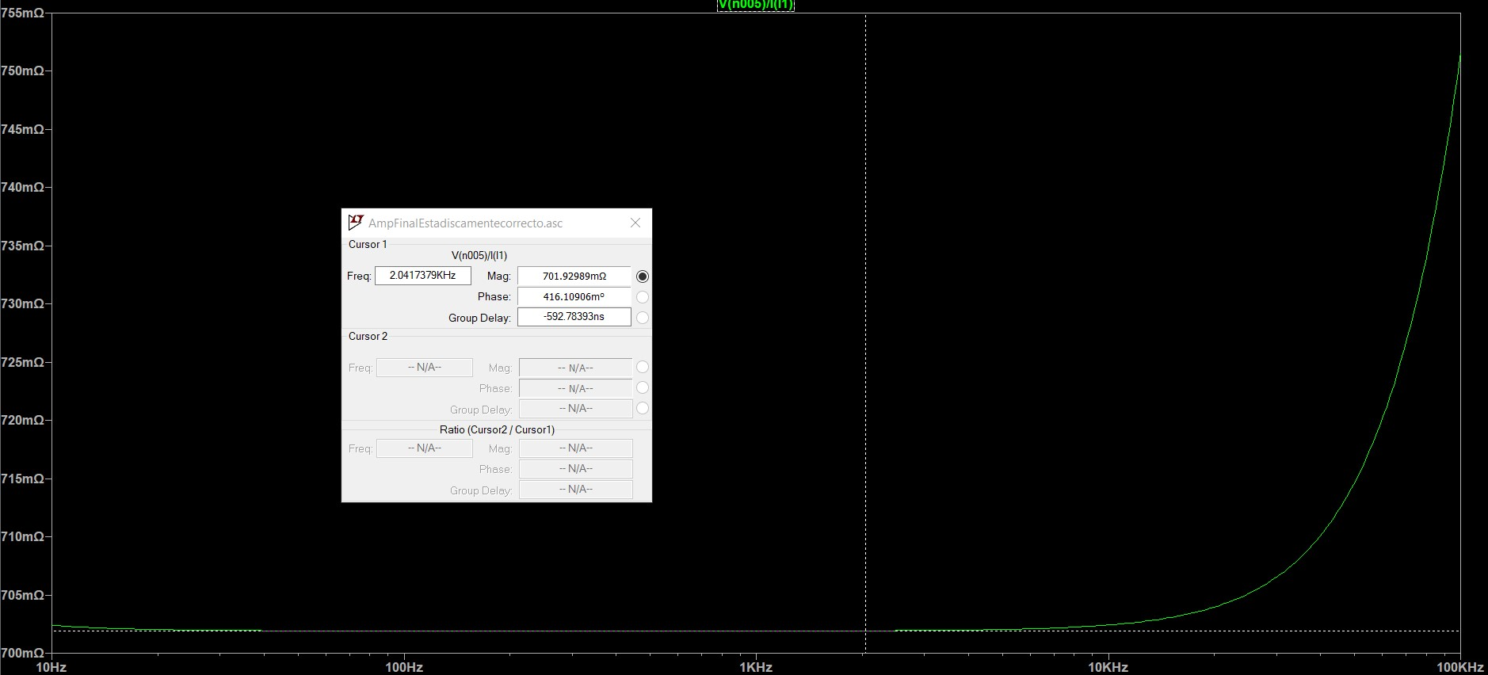
Simu/ImpedanciaOUT_Darlinton.jpg
