juan-felipe-castilla/TP2_Analogica/Simu/LINEALIDAD-DAR.jpg

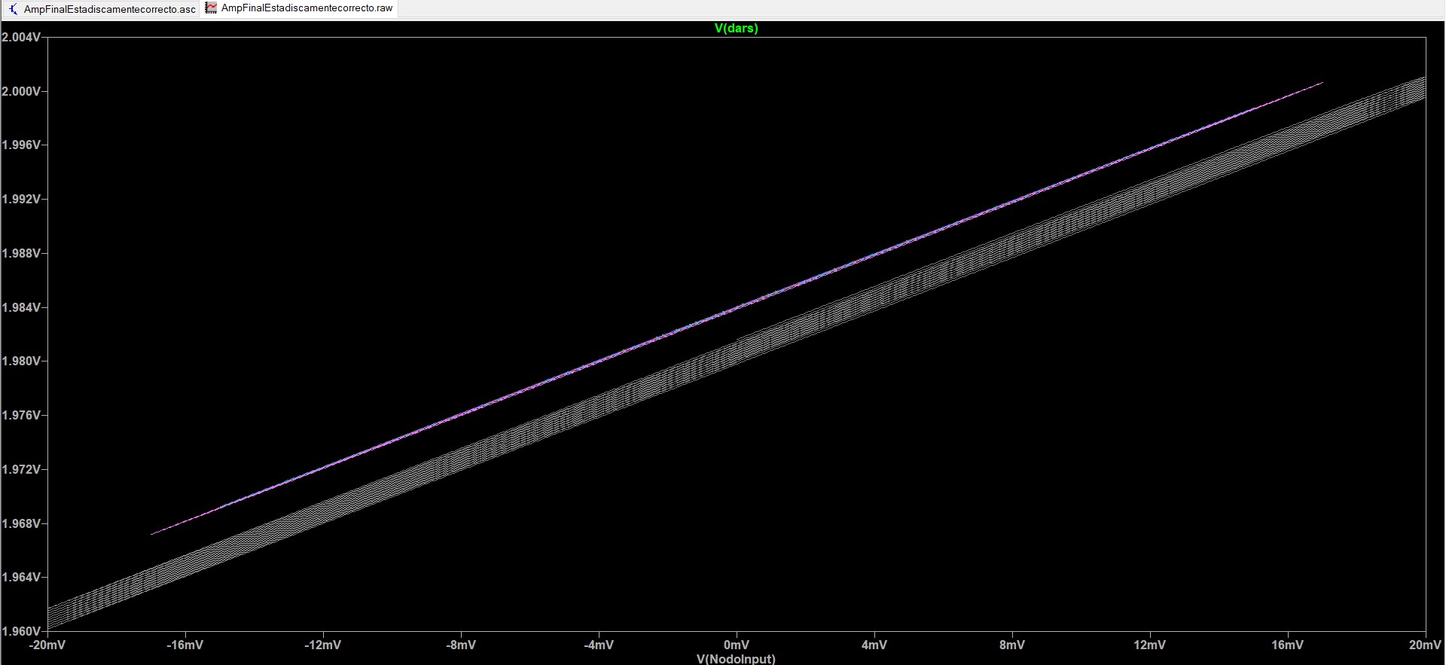
Simu/LINEALIDAD-DAR.jpg
