juan-felipe-castilla/TP2_Analogica/Simu/Linealidad-em.jpg

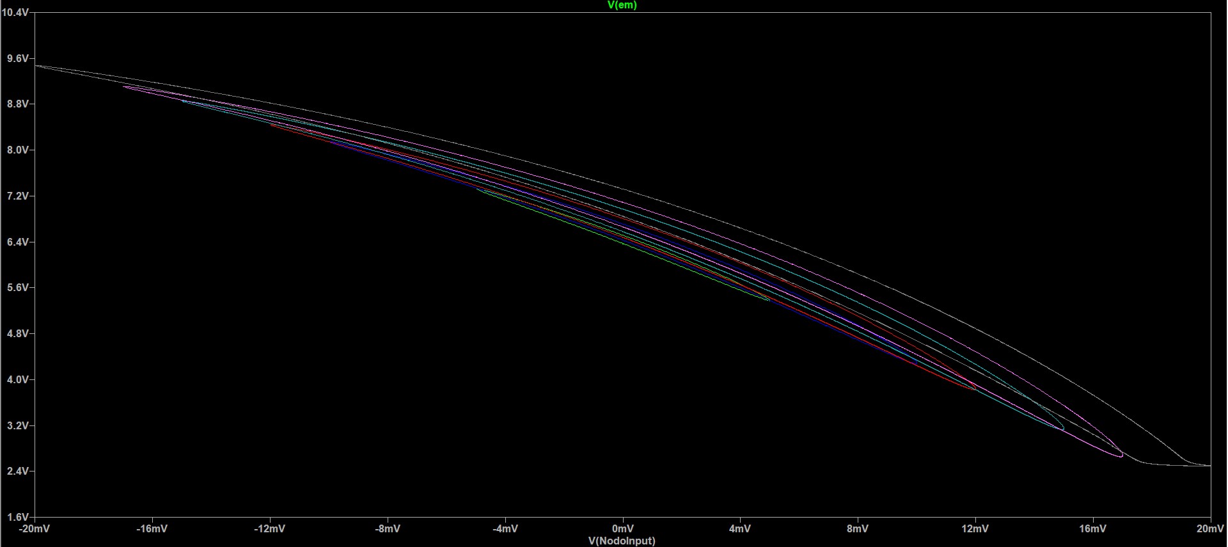
Simu/Linealidad-em.jpg
