juan-felipe-castilla/TP2_Analogica/Simu/Linealidad-sql.jpg

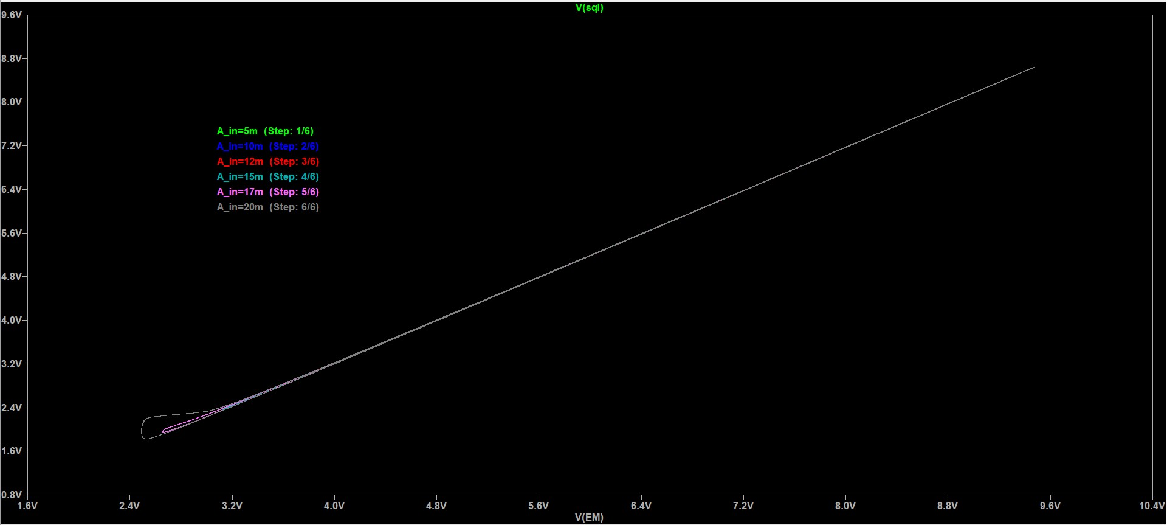
Simu/Linealidad-sql.jpg
