juan-felipe-castilla/TP2_Analogica/Simu/Linealidad.jpg

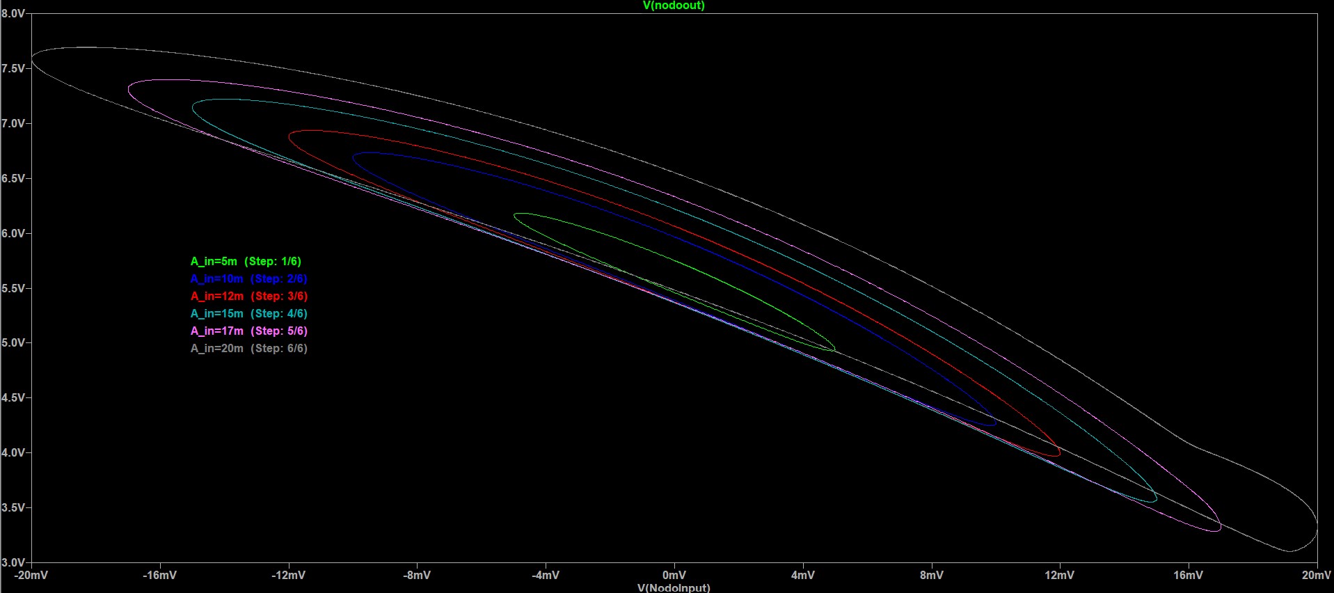
Simu/Linealidad.jpg
