juan-felipe-castilla/TP2_Analogica/Simu/Med-THD.jpg

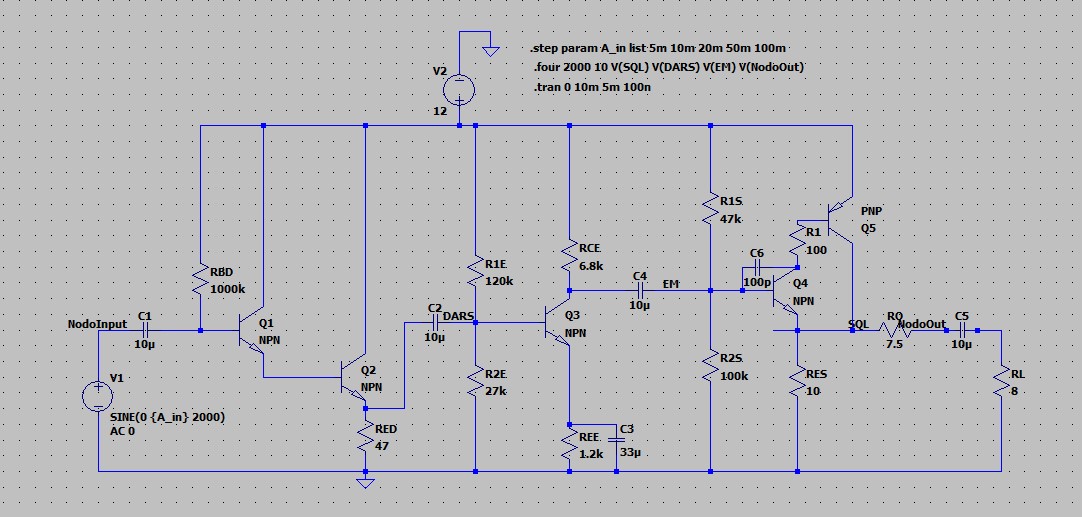
Simu/Med-THD.jpg
