juan-felipe-castilla/TP2_Analogica/Simu/Modelo_spice.jpg

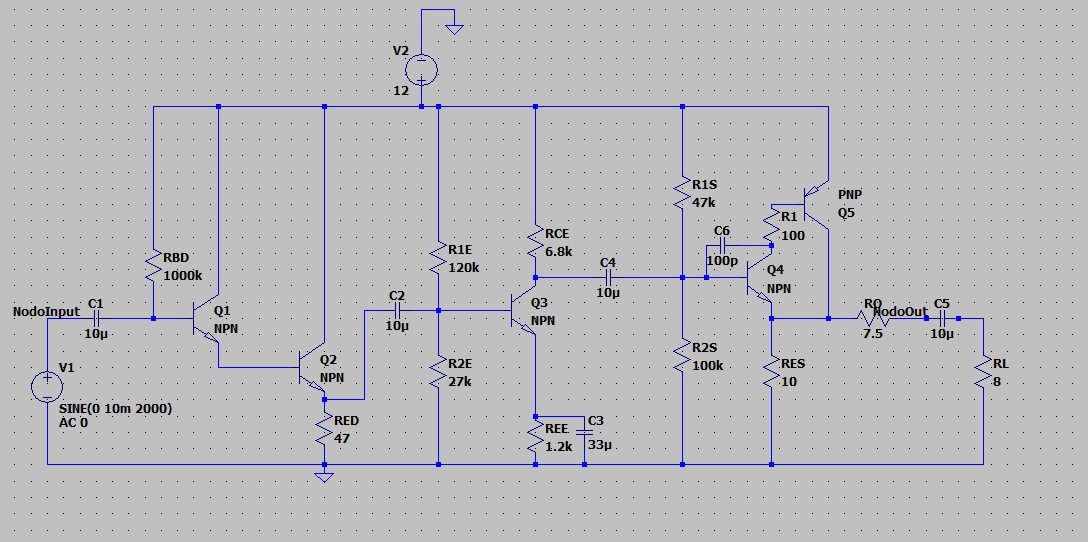
Simu/Modelo_spice.jpg
