juan-felipe-castilla/TP2_Analogica/Simu/Noise-dar.jpg

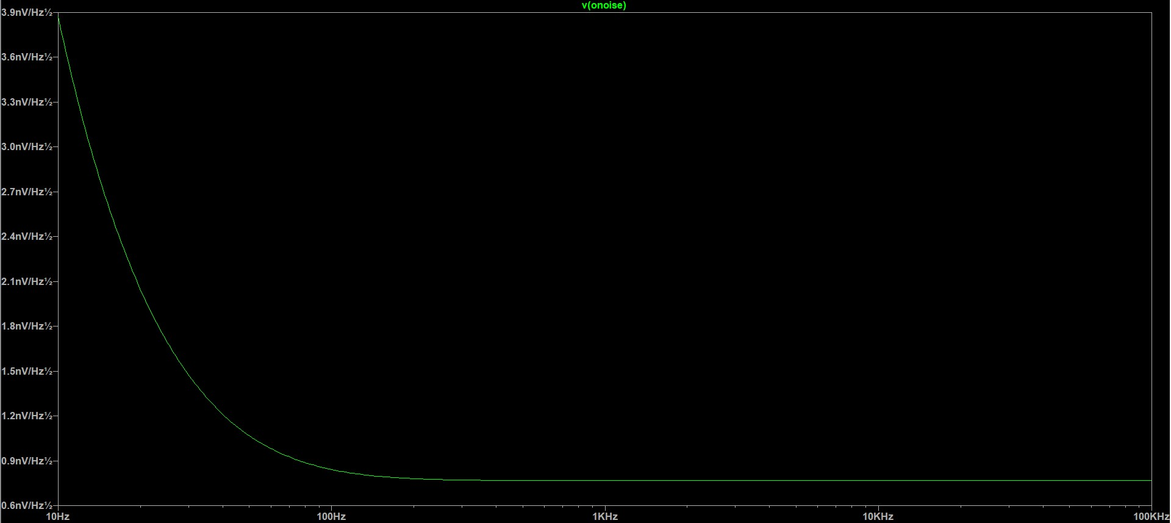
Simu/Noise-dar.jpg
