juan-felipe-castilla/TP2_Analogica/Simu/NOISE-EM.jpg

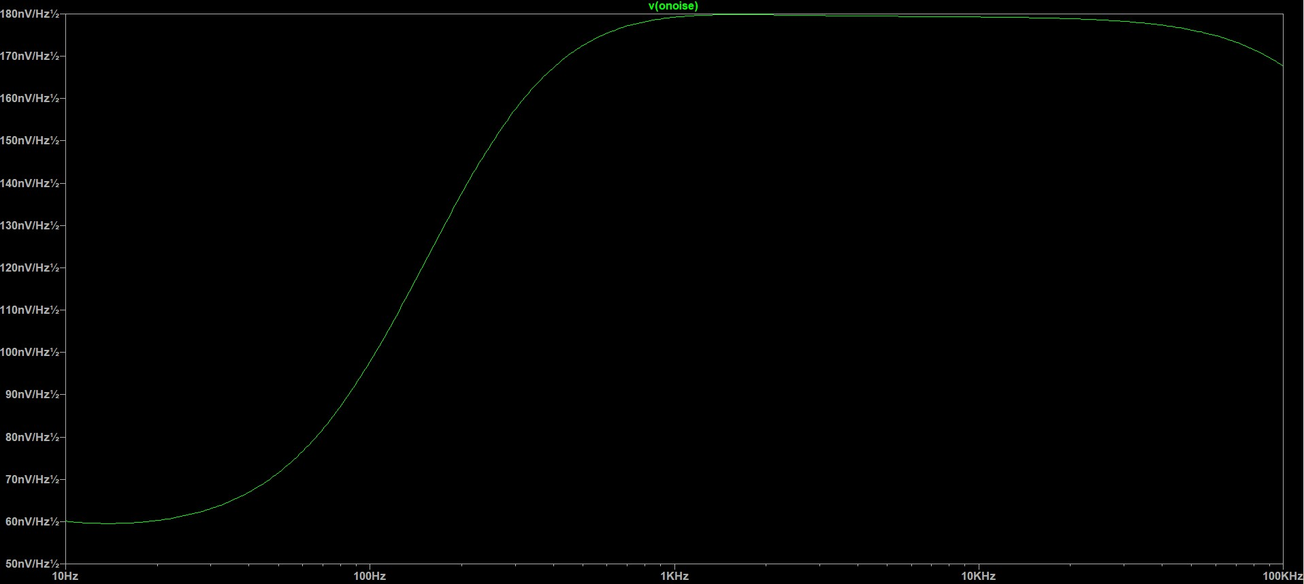
Simu/NOISE-EM.jpg
