juan-felipe-castilla/TP2_Analogica/Simu/Noise-out.jpg

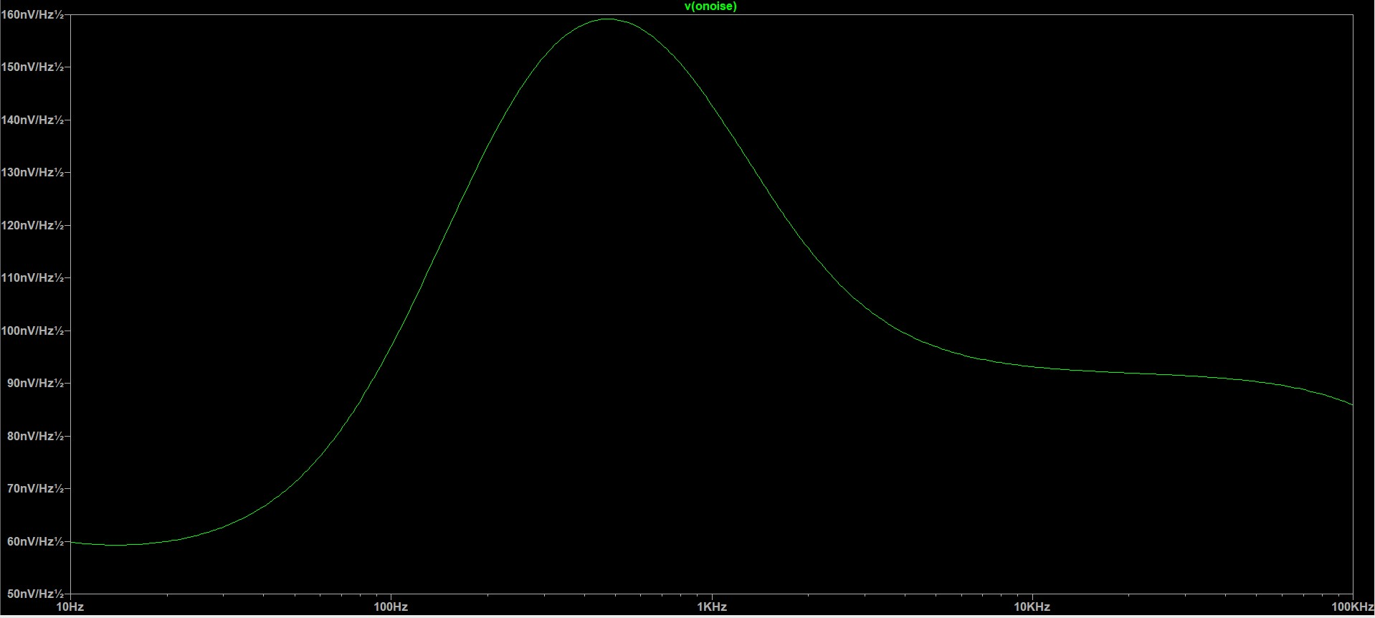
Simu/Noise-out.jpg
