juan-felipe-castilla/TP2_Analogica/Simu/Noise-totalcondirct.jpg

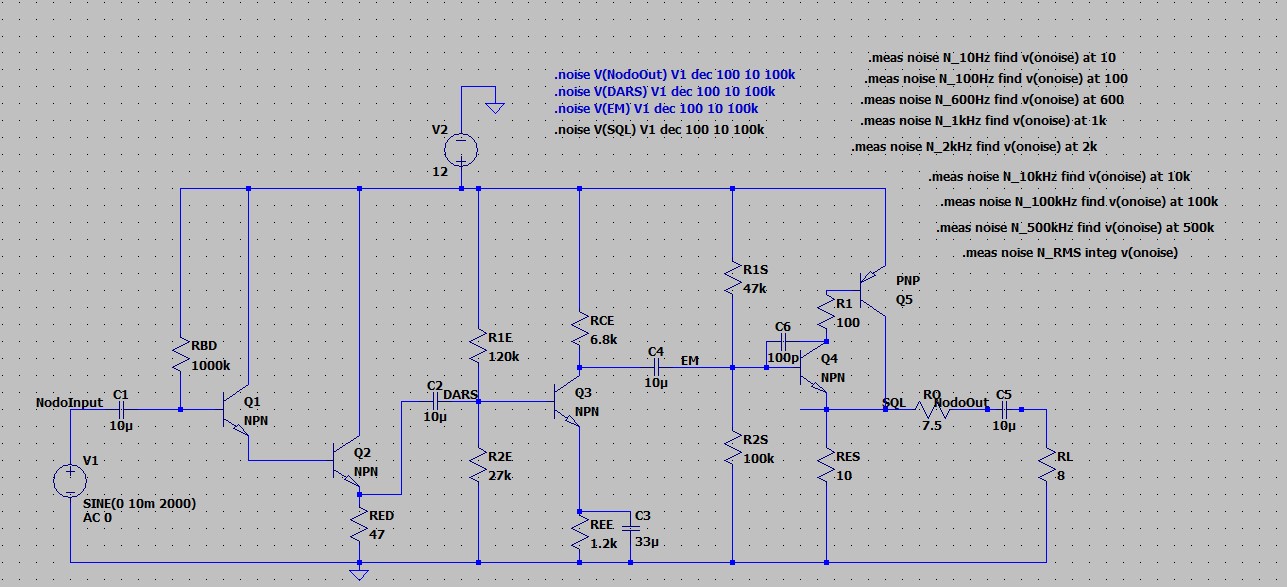
Simu/Noise-totalcondirct.jpg
