juan-felipe-castilla/TP2_Analogica/Simu/OpTotal.png

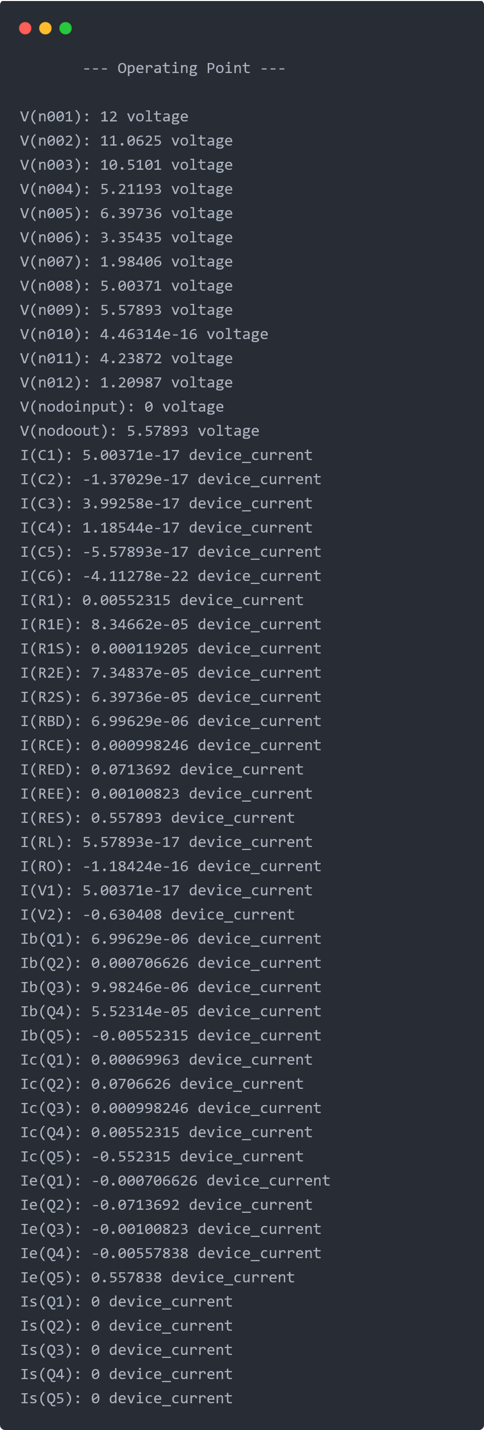
Simu/OpTotal.png
