juan-felipe-castilla/TP2_Analogica/Simu/RLMUERTE.jpg

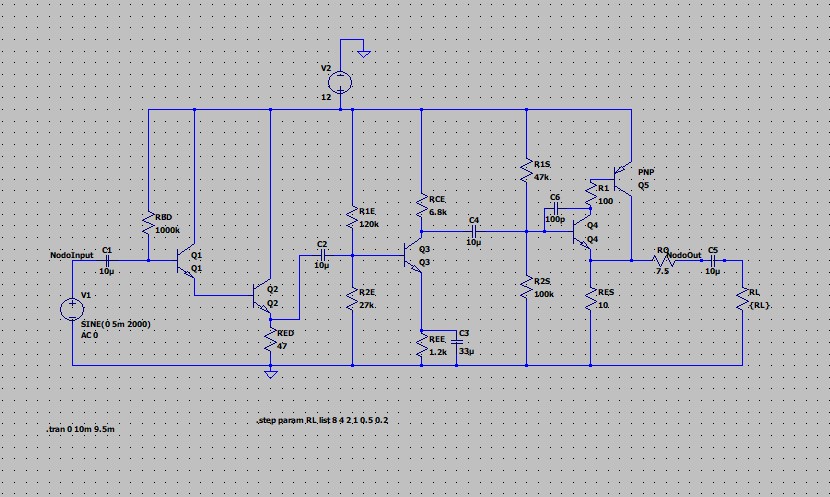
Simu/RLMUERTE.jpg
