juan-felipe-castilla/TP2_Analogica/Simu/RLMURTESALIDA.jpg

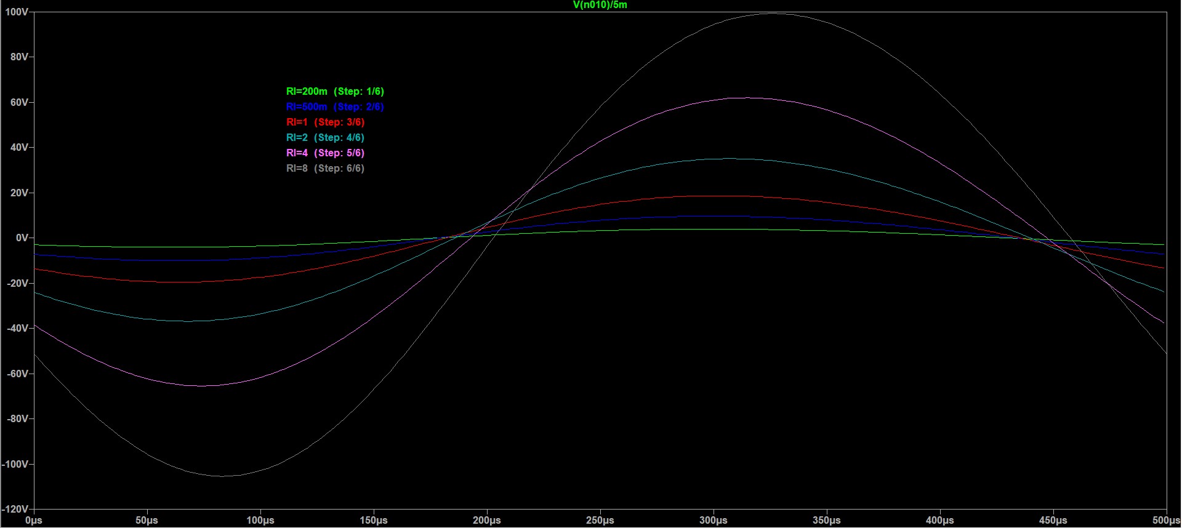
Simu/RLMURTESALIDA.jpg
