juan-felipe-castilla/TP2_Analogica/Simu/sql-aislado.jpg

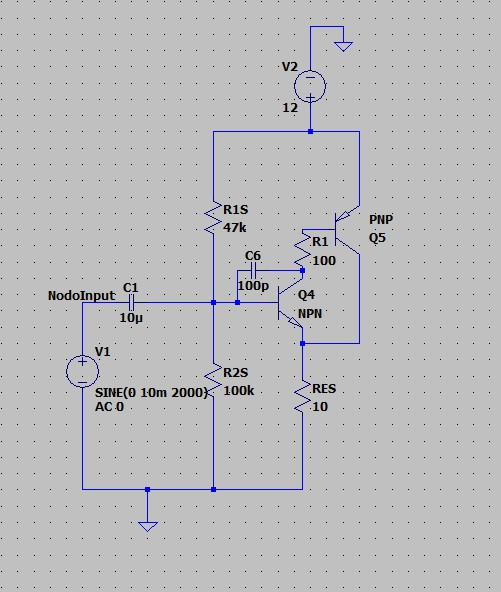
Simu/sql-aislado.jpg
