juan-felipe-castilla/TP2_Analogica/Simu/sql_impedanciaSalida.jpg

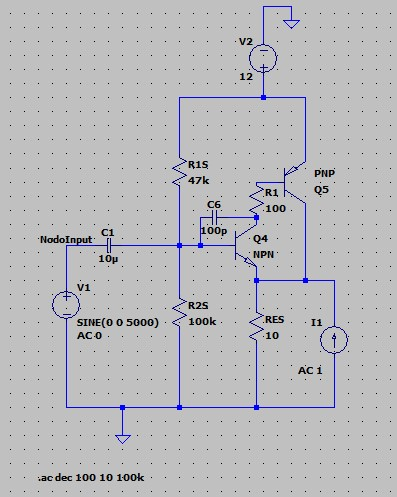
Simu/sql_impedanciaSalida.jpg
