juan-felipe-castilla/TP2_Analogica/Simu/SQL_ZIN.jpg

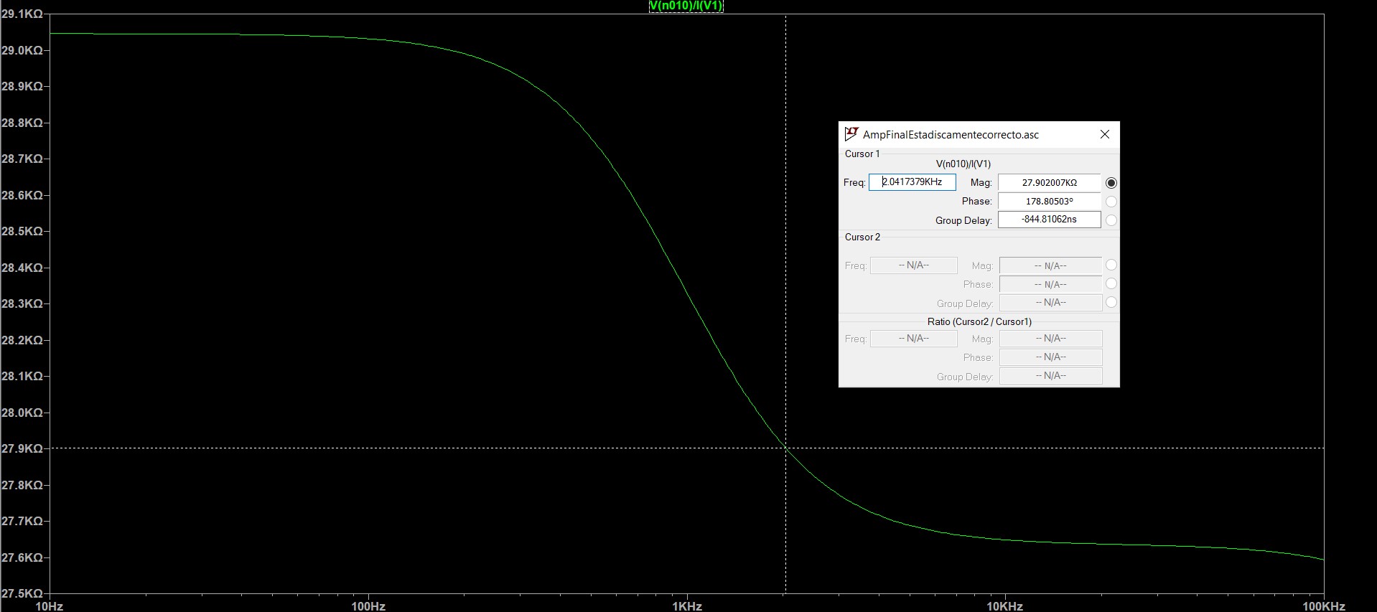
Simu/SQL_ZIN.jpg
