juan-felipe-castilla/TP2_Analogica/Simu/VCC-EMISOR.jpg

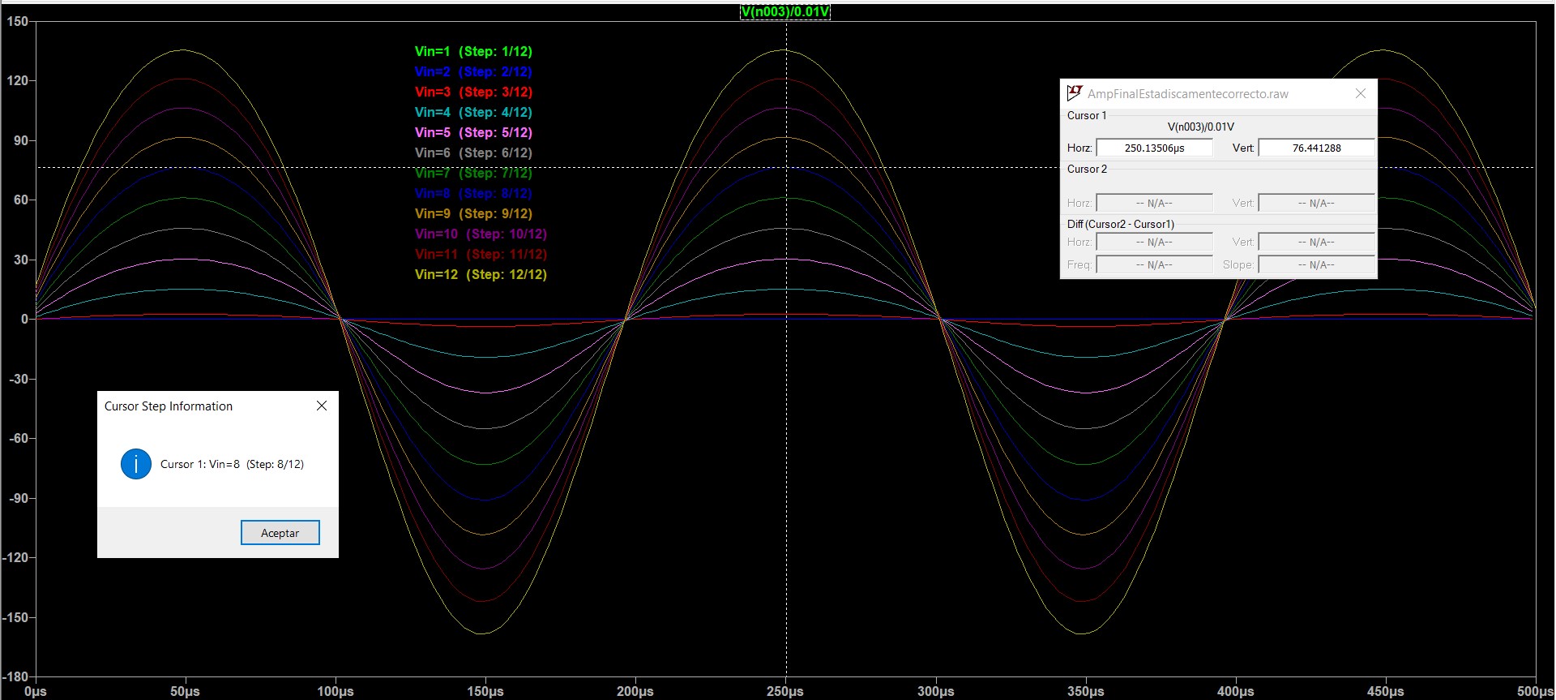
Simu/VCC-EMISOR.jpg
