juan-felipe-castilla/TP2_Analogica/Simu/vcc-sql.jpg

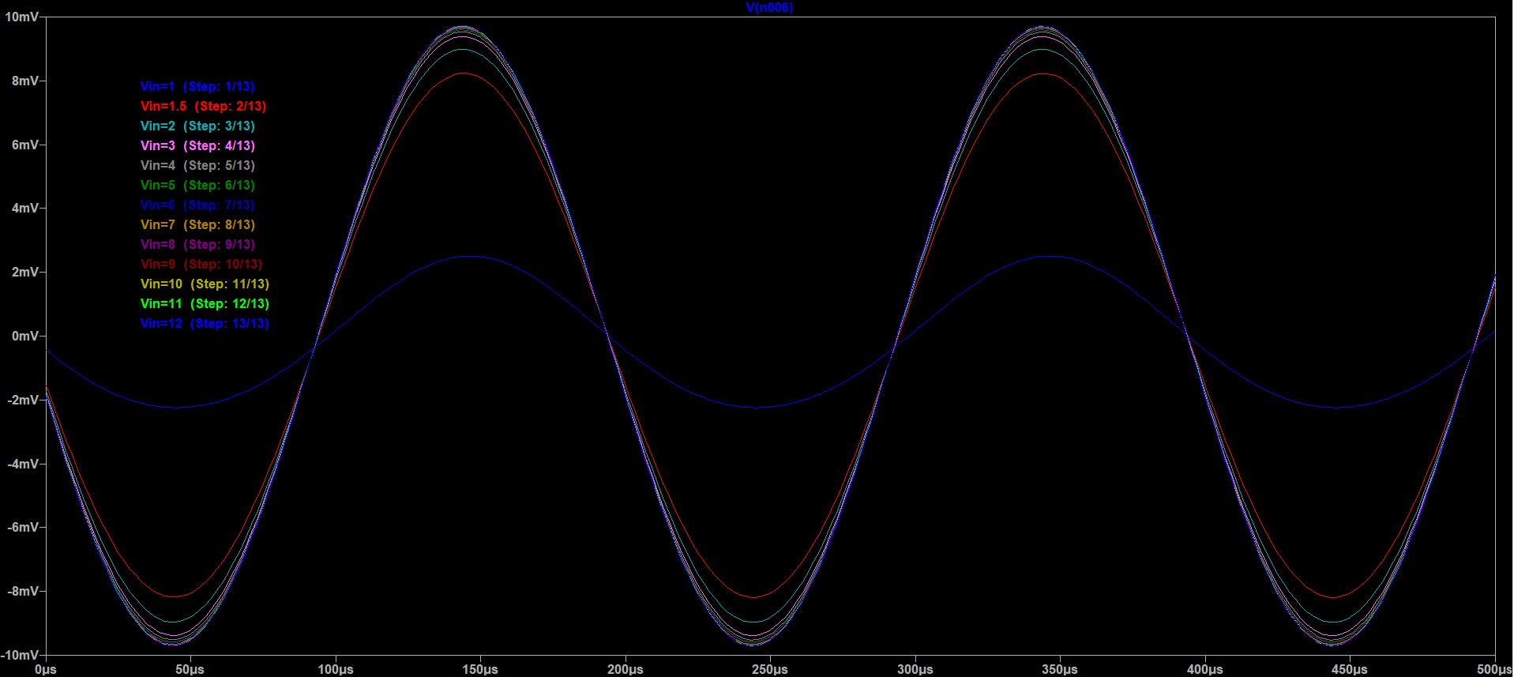
Simu/vcc-sql.jpg
