juan-felipe-castilla/TP2_Analogica/Simu/Volatajemuertearribadar.jpg

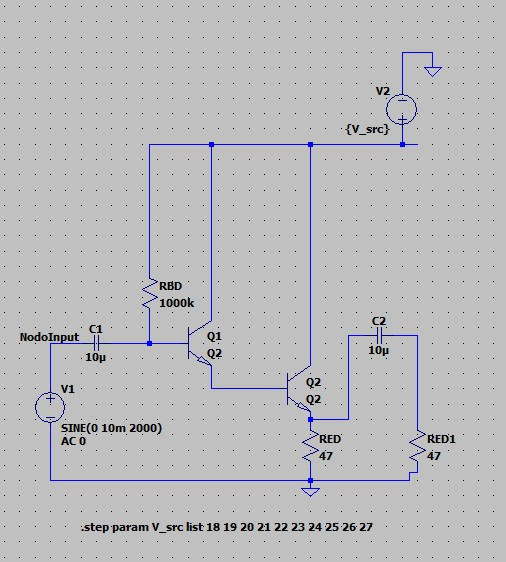
Simu/Volatajemuertearribadar.jpg
