juan-felipe-castilla/TP2_Analogica/Simu/VOLATAJEMUERTEARRIBAEMISOR.jpg

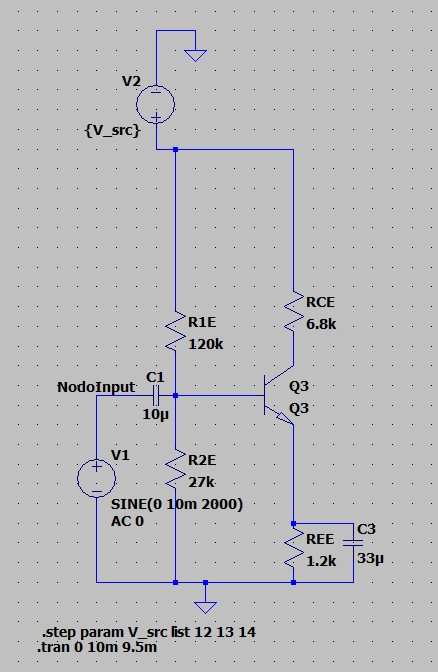
Simu/VOLATAJEMUERTEARRIBAEMISOR.jpg
