juan-felipe-castilla/TP2_Analogica/Simu/Volatajes-alimentacion-dar.jpg

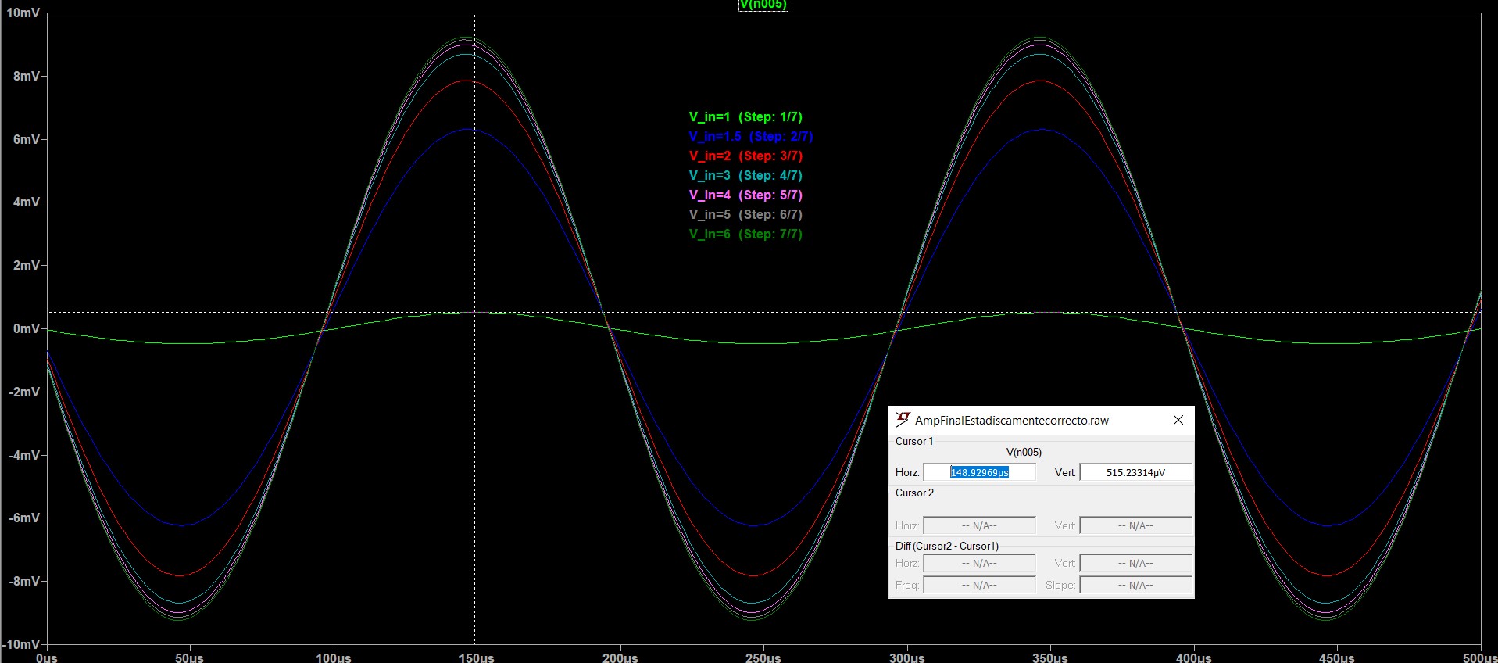
Simu/Volatajes-alimentacion-dar.jpg
