juan-felipe-castilla/TP2_Analogica/Simu/Voltaje-salida-arriba-dar.jpg

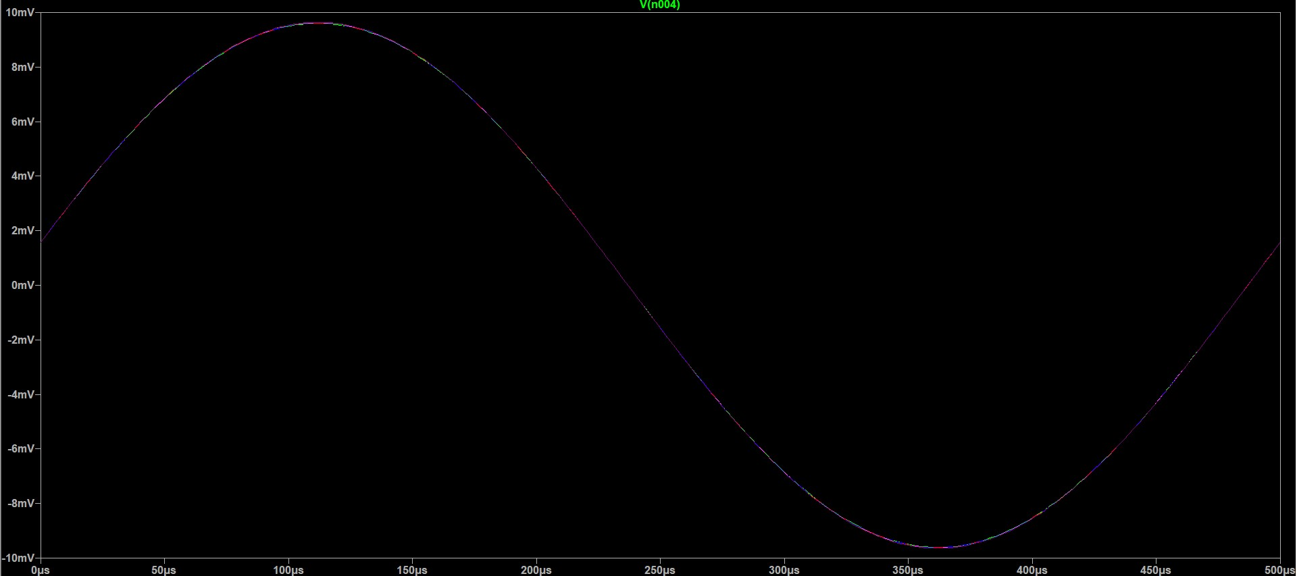
Simu/Voltaje-salida-arriba-dar.jpg
