juan-felipe-castilla/TP2_Analogica/Simu/Voltaje_salida_5k.jpg

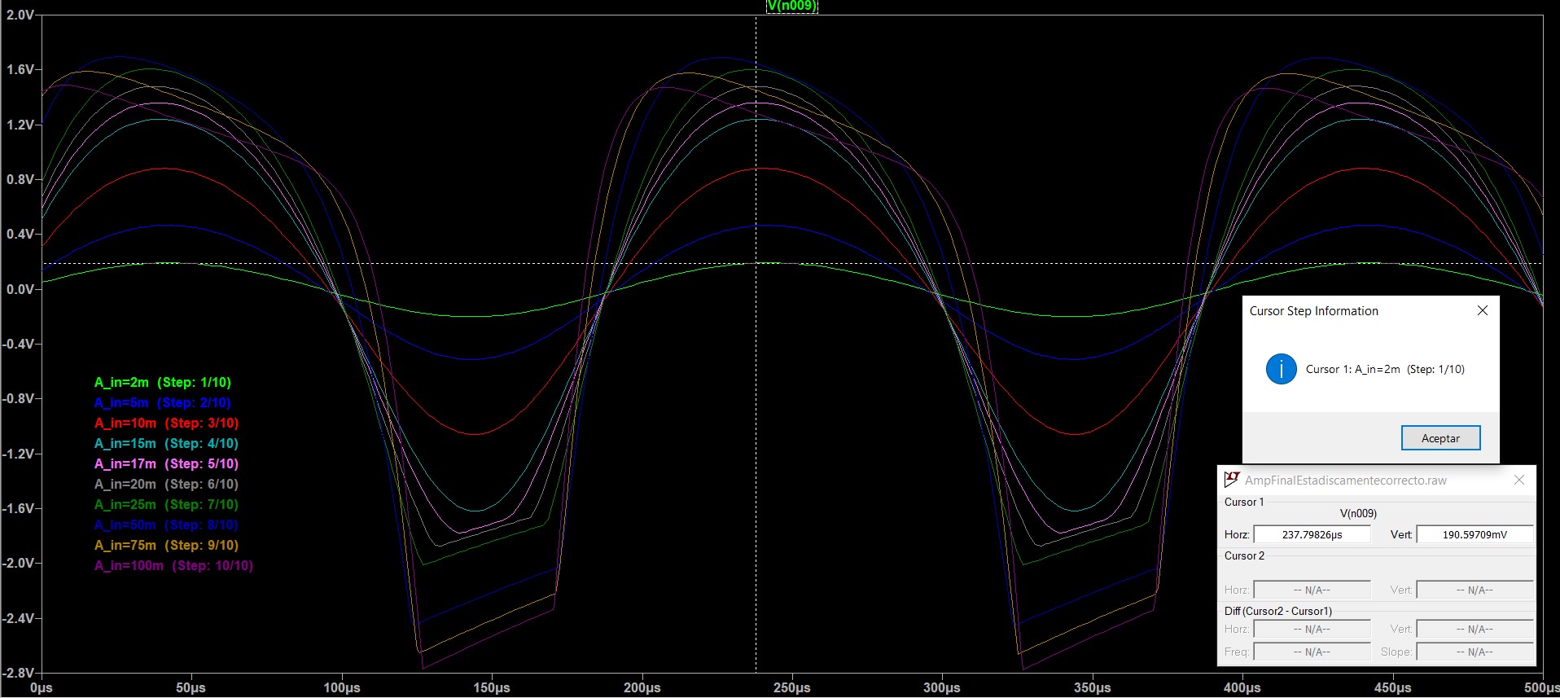
Simu/Voltaje_salida_5k.jpg
