juan-felipe-castilla/TP2_Analogica/Simu/Voltaje_salida_10m.jpg

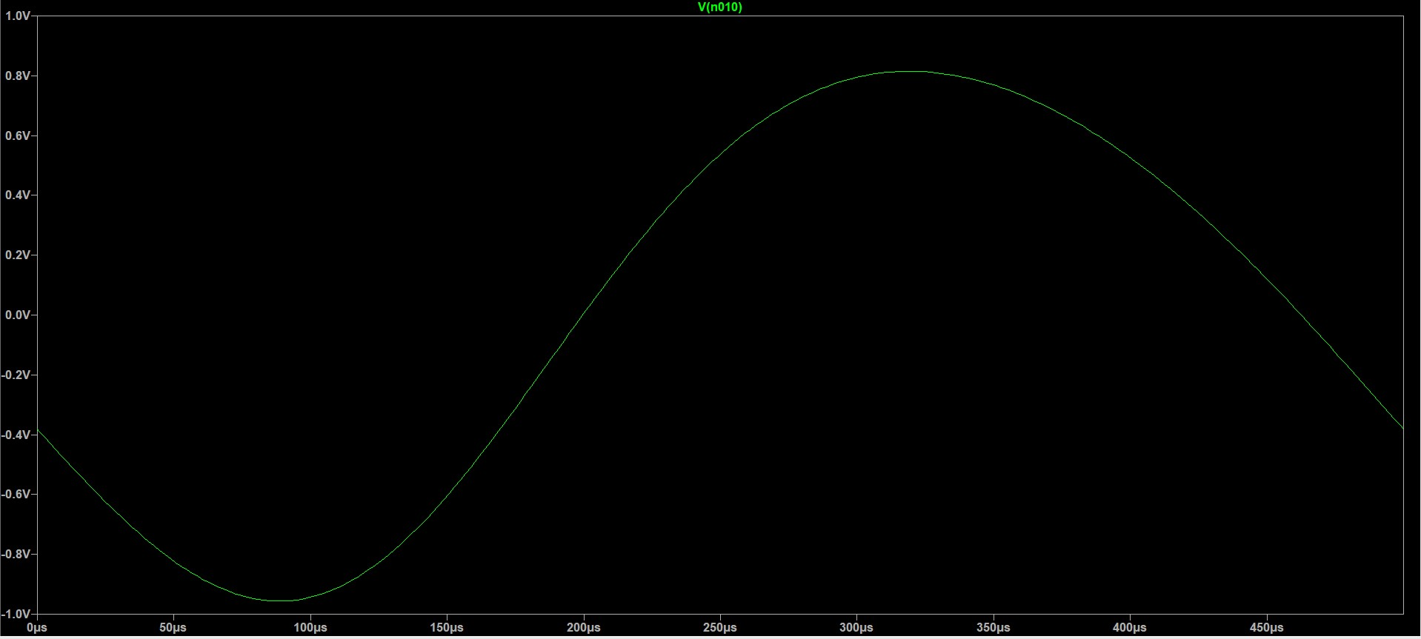
Simu/Voltaje_salida_10m.jpg
