juan-felipe-castilla/TP2_Analogica/Simu/VOLTAJEARRIBASALIDAEMISOR.jpg

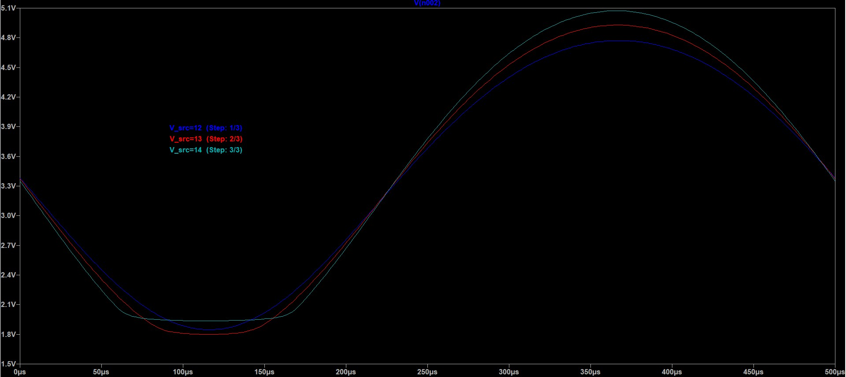
Simu/VOLTAJEARRIBASALIDAEMISOR.jpg
