juan-felipe-castilla/TP2_Analogica/Simu/voltajemuerteabajototal-salida.jpg

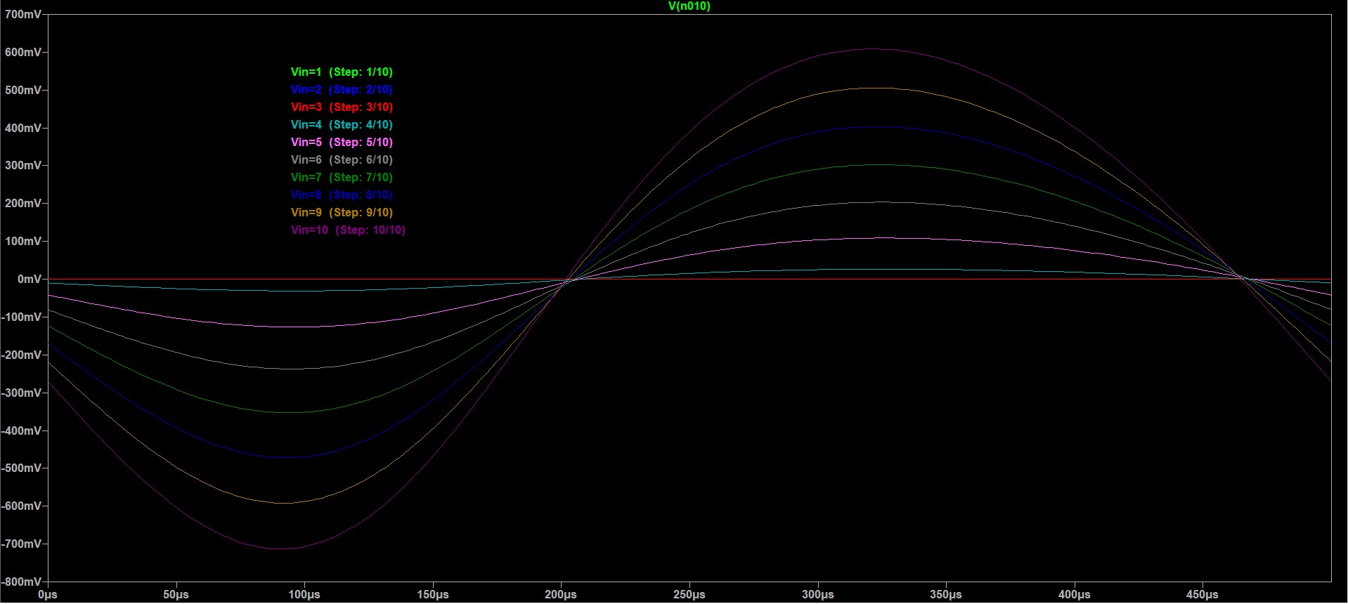
Simu/voltajemuerteabajototal-salida.jpg
