juan-felipe-castilla/TP2_Analogica/Simu/voltajemuertearribasql-salida.jpg

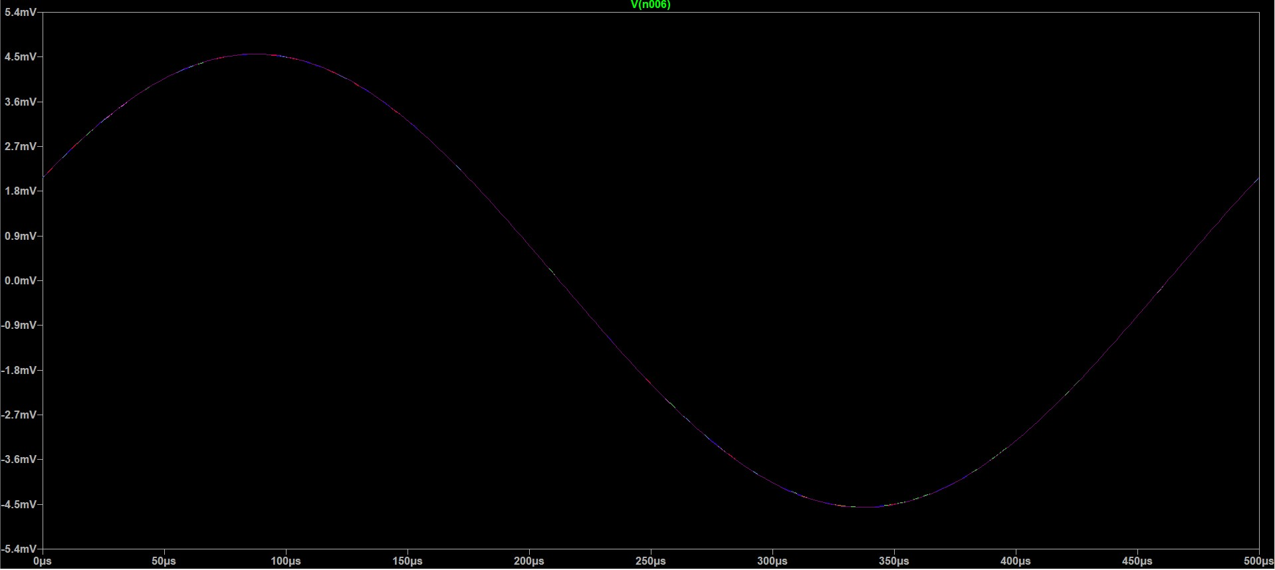
Simu/voltajemuertearribasql-salida.jpg
