juan-felipe-castilla/TP2_Analogica/Simu/VOLTAJEMUERTEARRIBASQL.jpg

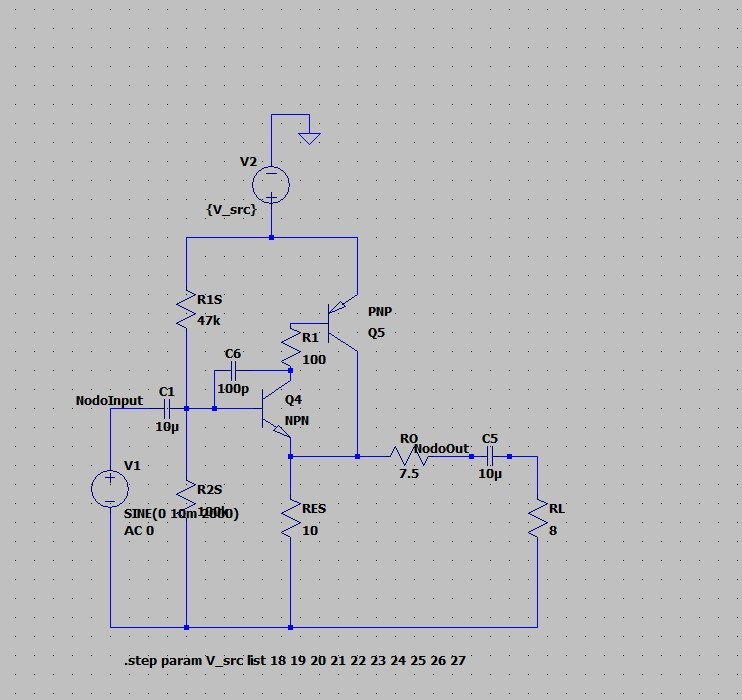
Simu/VOLTAJEMUERTEARRIBASQL.jpg
