juan-felipe-castilla/TP2_Analogica/Simu/voltajemuertearribatotal-salida.jpg

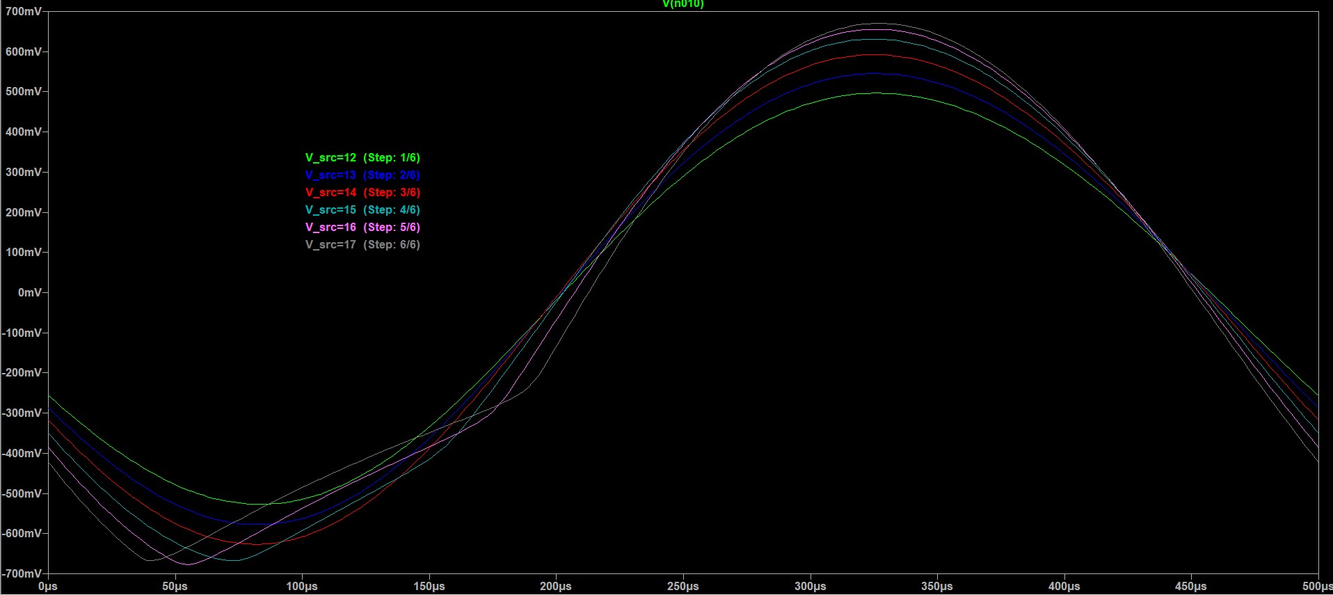
Simu/voltajemuertearribatotal-salida.jpg
