juan-felipe-castilla/TP2_Analogica/Simu/voltajemuertearribatotal.jpg

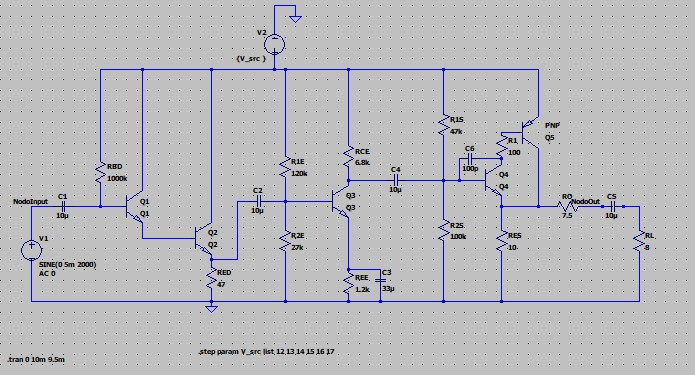
Simu/voltajemuertearribatotal.jpg
