juan-felipe-castilla/TP2_Analogica/Simu/Voutppdarlin.jpg

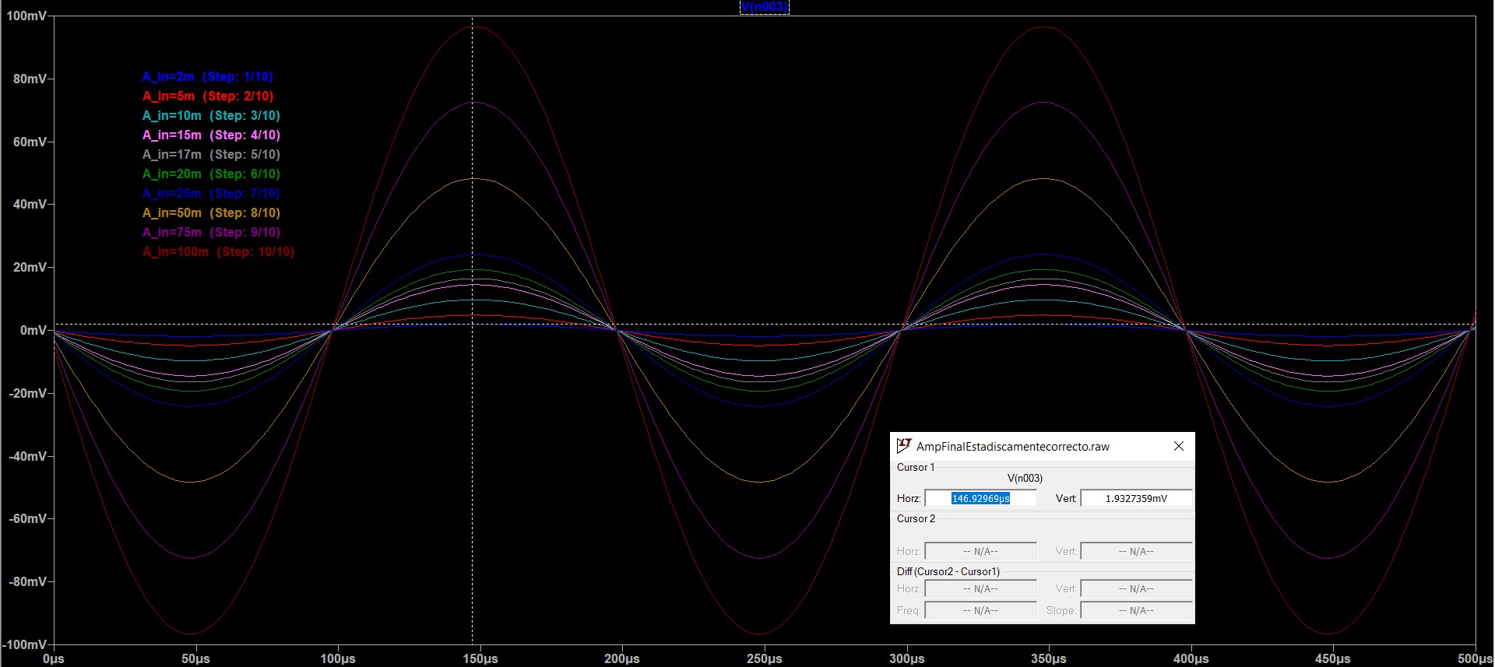
Simu/Voutppdarlin.jpg
