juan-felipe-castilla/TP2_Analogica/Simu/VPP-EMISOR.jpg

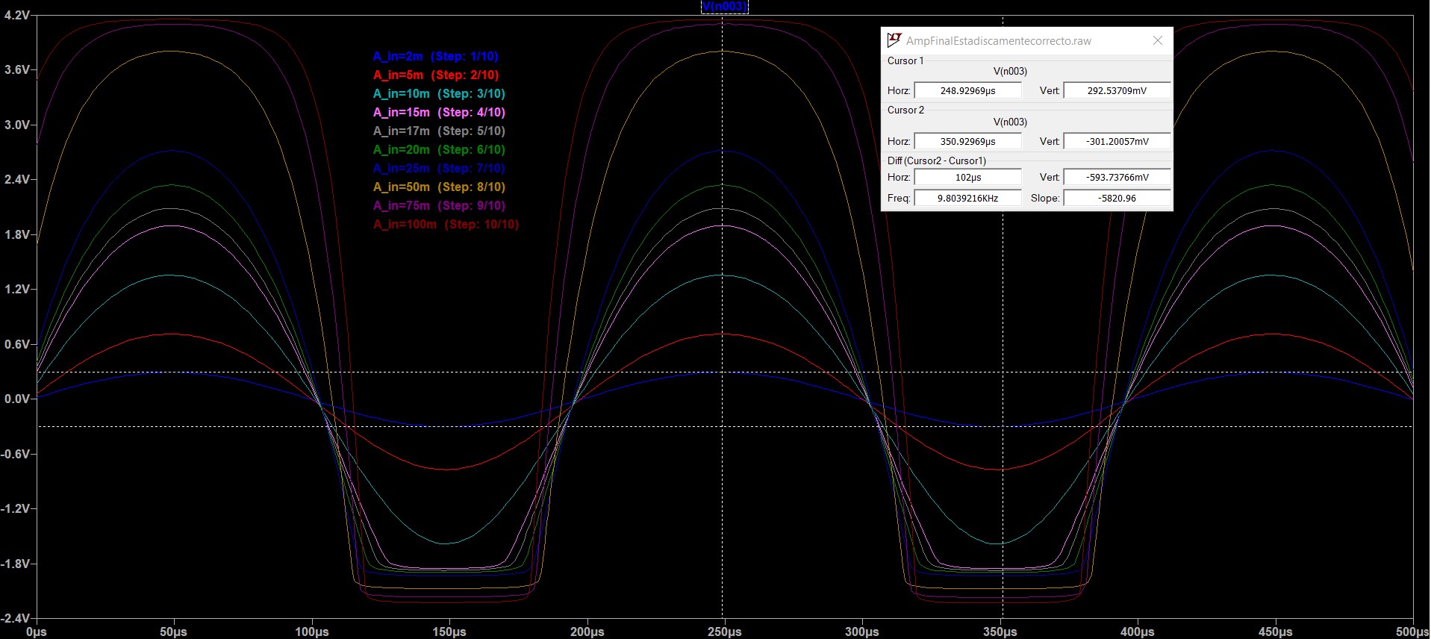
Simu/VPP-EMISOR.jpg
