juan-felipe-castilla/TP2_Analogica/Simu/VPP-SQL.jpg

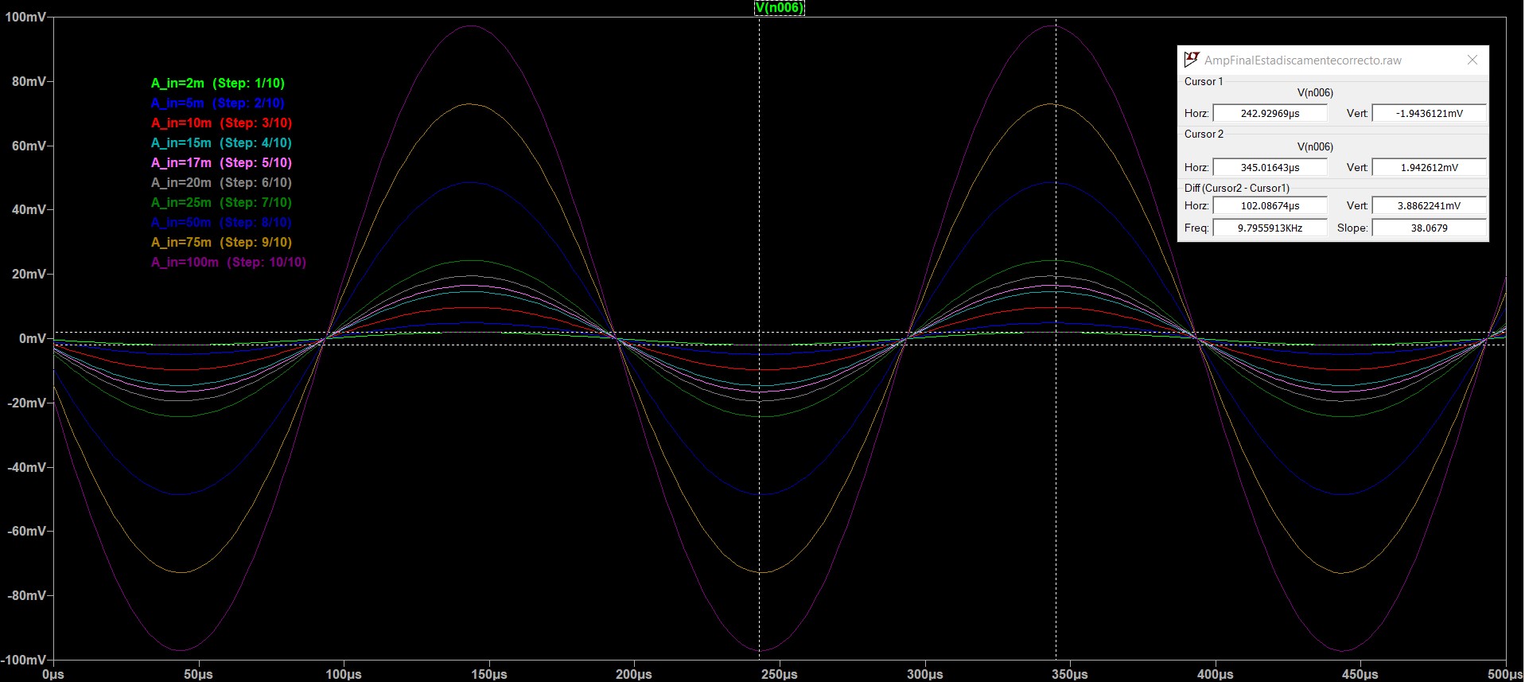
Simu/VPP-SQL.jpg
