juan-felipe-castilla/TP2_Analogica/Simu/z23.jpg

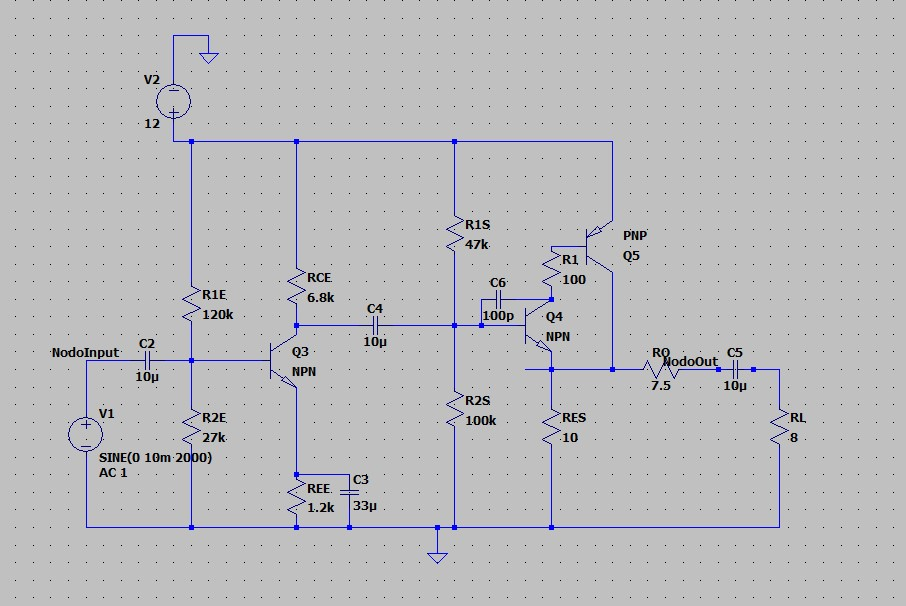
Simu/z23.jpg
