juan-felipe-castilla/TP2_Analogica/TP2_EA1/Bode.png

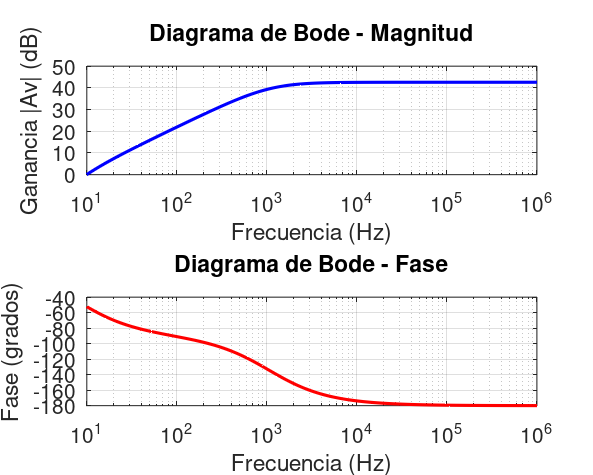
TP2_EA1/Bode.png
