juan-felipe-castilla/TP2_Analogica/TP2_EA1/Esquemático.jpeg

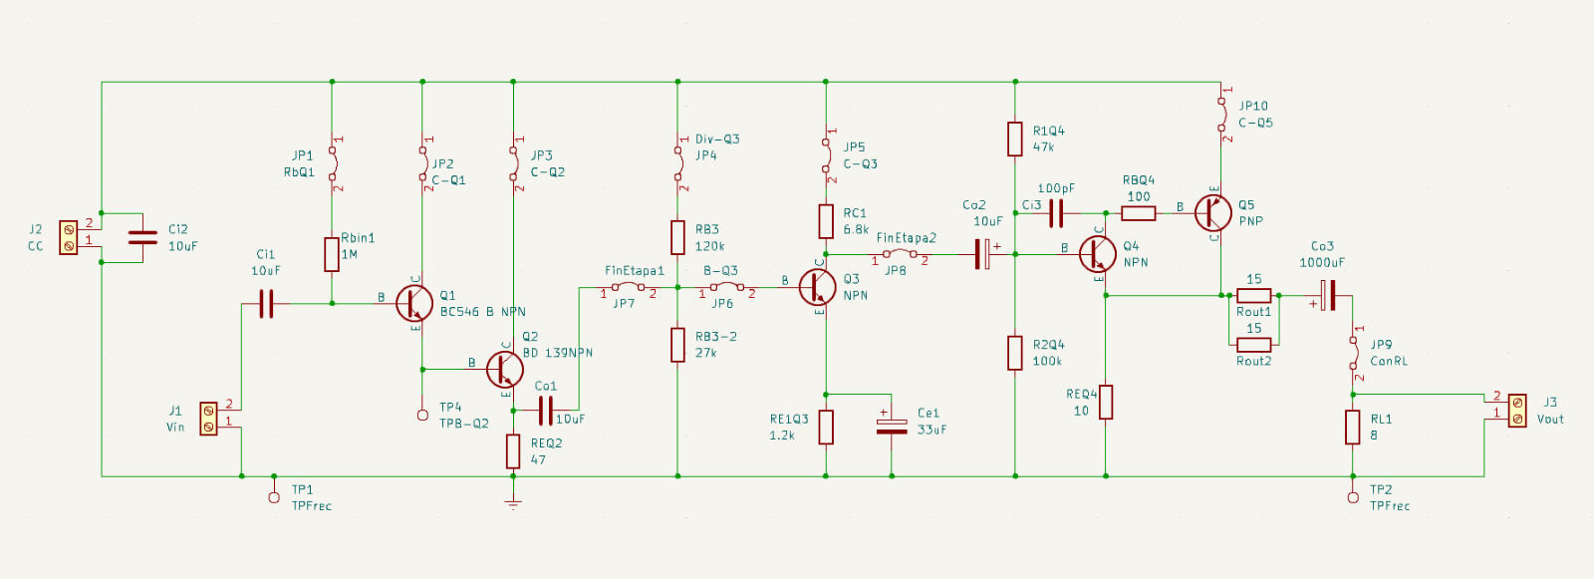
TP2_EA1/Esquemático.jpeg
