juan-felipe-castilla/TP2_Analogica/TP2_EA1/Impreso.jpeg

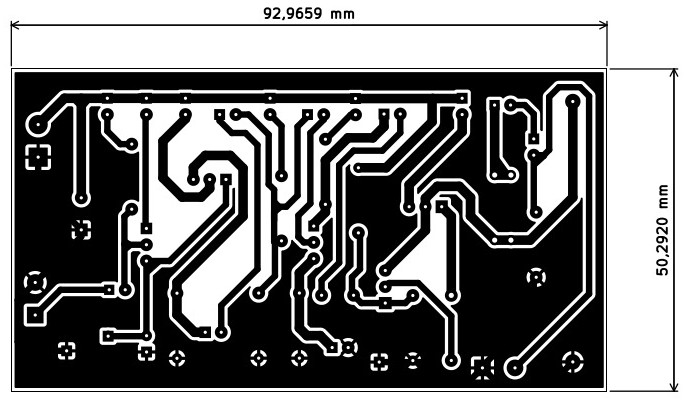
TP2_EA1/Impreso.jpeg
