juan-felipe-castilla/TP2_Analogica/TP2_EA1/RectaQ1.png

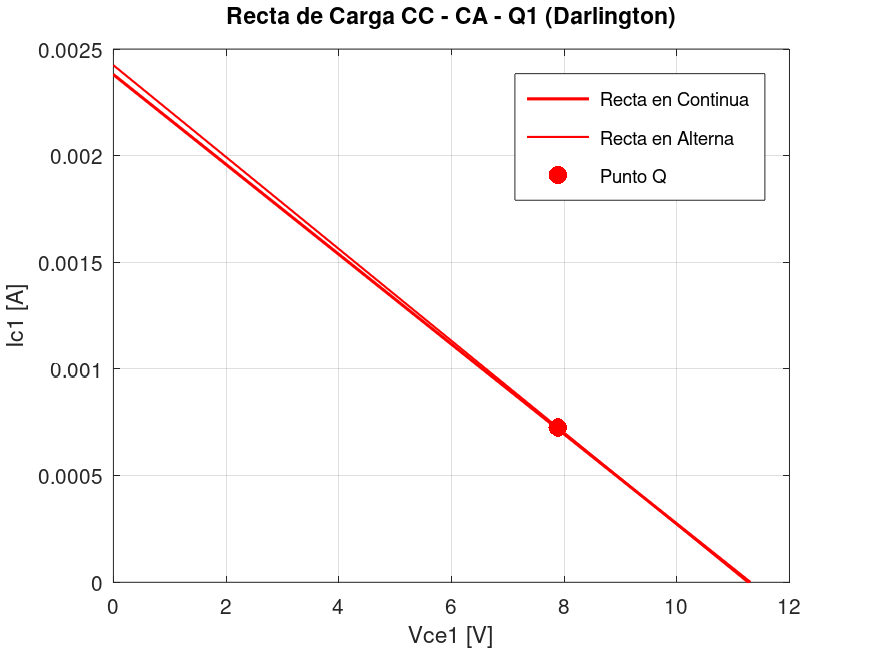
TP2_EA1/RectaQ1.png
