juan-felipe-castilla/TP2_Analogica/TP2_EA1/RectaQ2.png

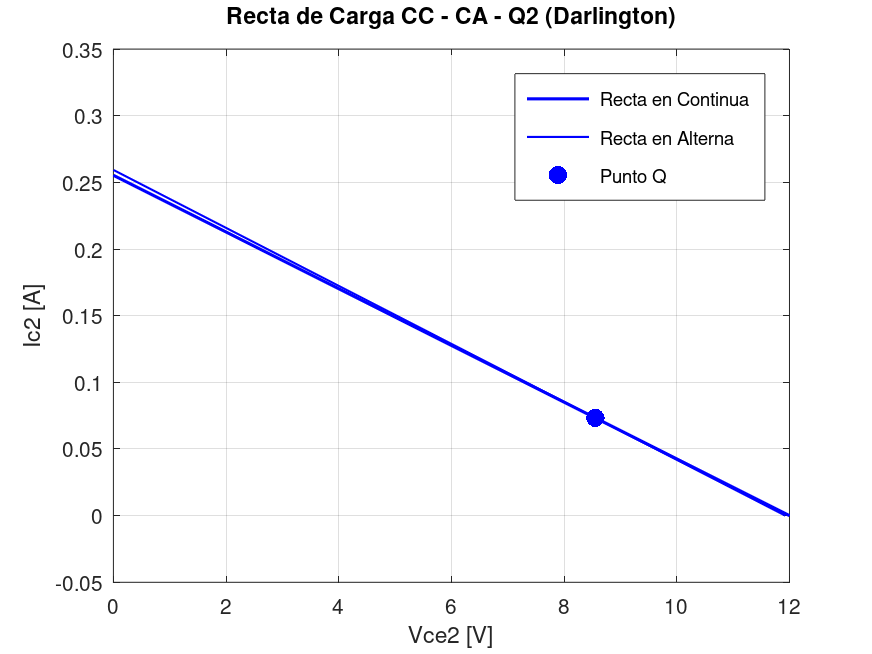
TP2_EA1/RectaQ2.png
