juan-felipe-castilla/TP2_Analogica/TP2_EA1/RectaQ4.png

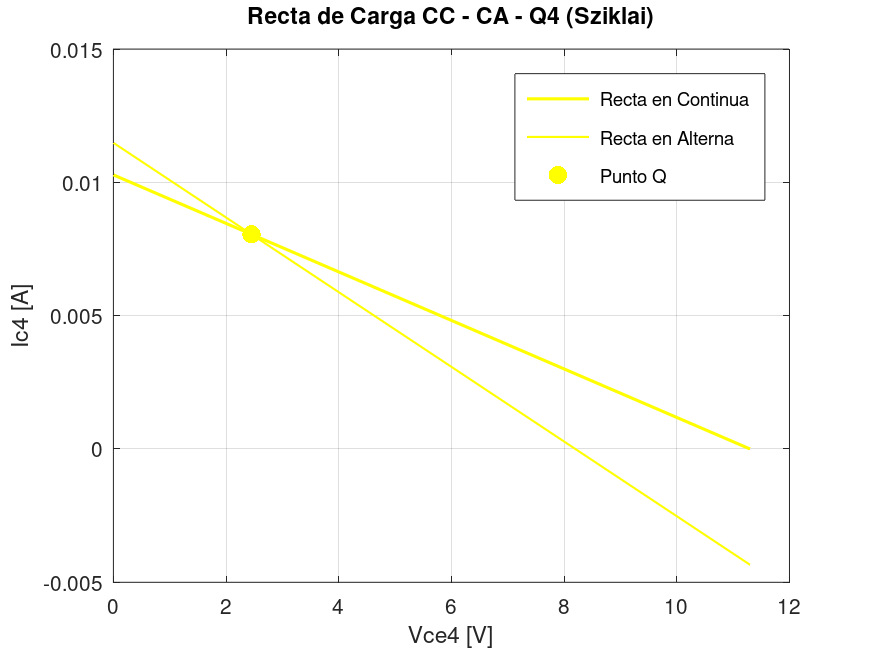
TP2_EA1/RectaQ4.png
