juan-felipe-castilla/TP2_Analogica/TP2_EA1/Trazas.jpeg

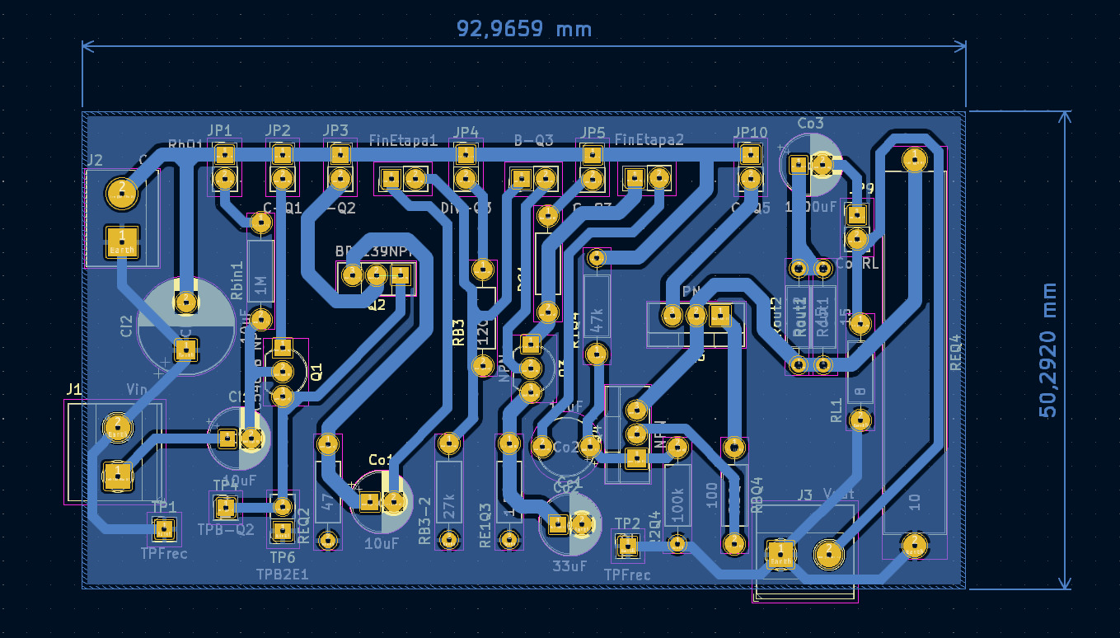
TP2_EA1/Trazas.jpeg
