juan-felipe-castilla/TP2_Analogica/FotosMed/Setup/Generador.jpeg

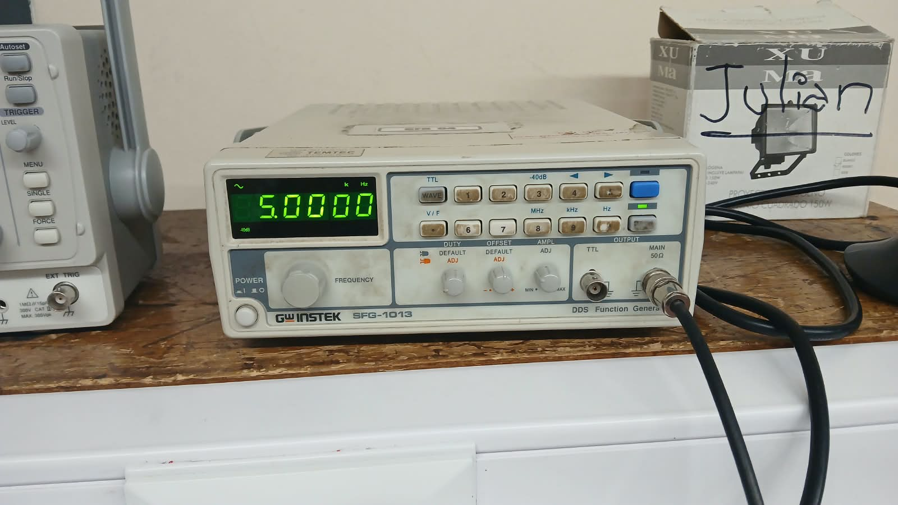
FotosMed/Setup/Generador.jpeg
