juan-felipe-castilla/TP2_Analogica/FotosMed/Setup/Osc.jpeg

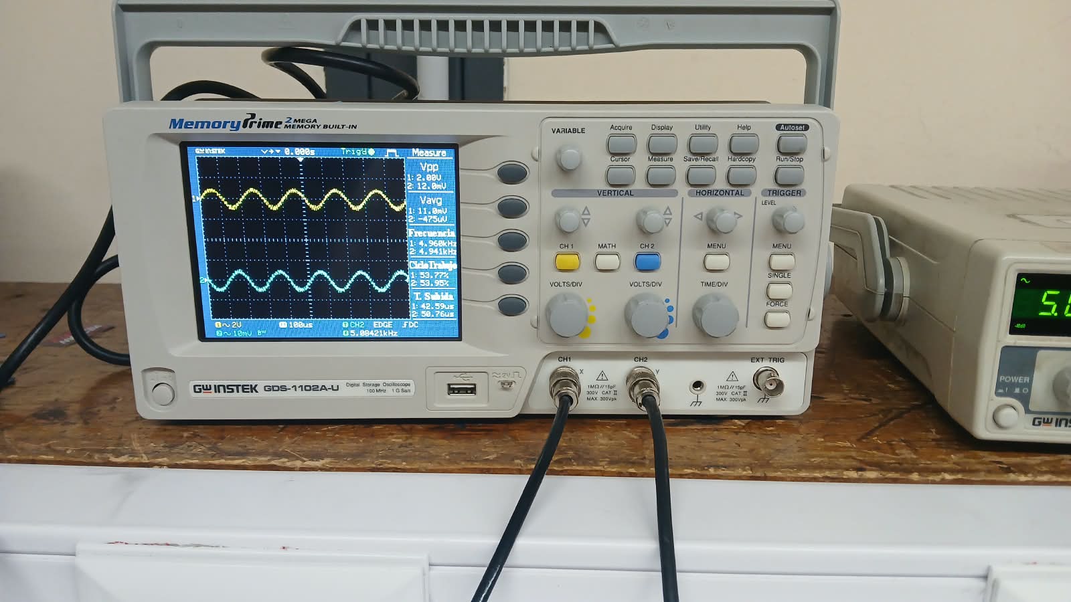
FotosMed/Setup/Osc.jpeg
