juan-felipe-castilla/TP2_Analogica/FotosMed/Setup/SetupGeneral1.jpeg

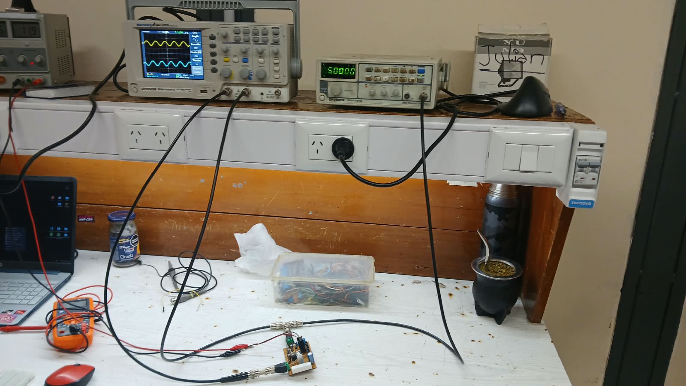
FotosMed/Setup/SetupGeneral1.jpeg
