juan-felipe-castilla/TP2_Analogica/FotosMed/Setup/WhatsApp Image 2026-10-07 at 09.15.06(3).jpeg

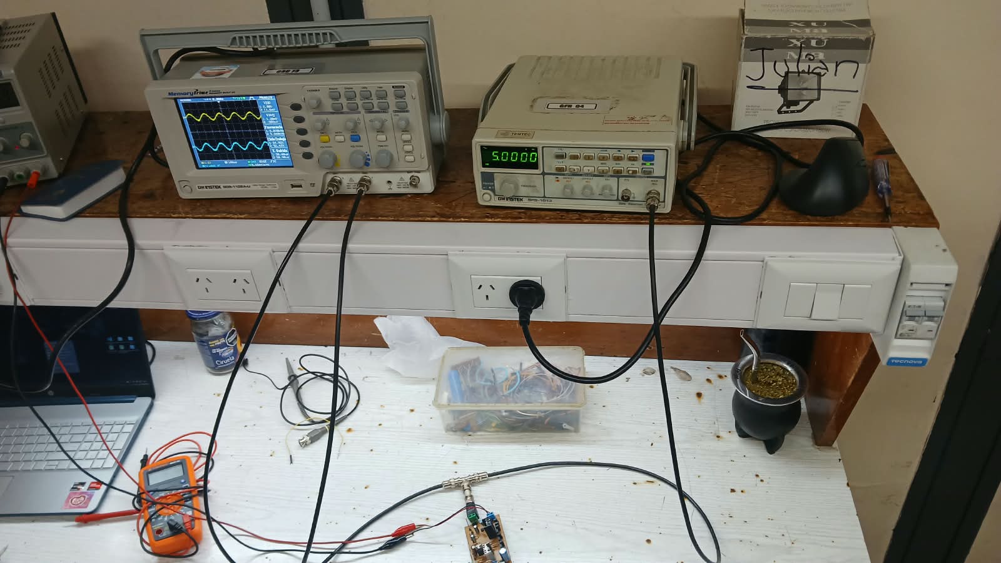
FotosMed/Setup/WhatsApp Image 2026-10-07 at 09.15.06(3).jpeg
