juan-felipe-castilla/TP2_Analogica/SetupMediciones/TensionesCorrientes/BarridoDeFrecuencia.png

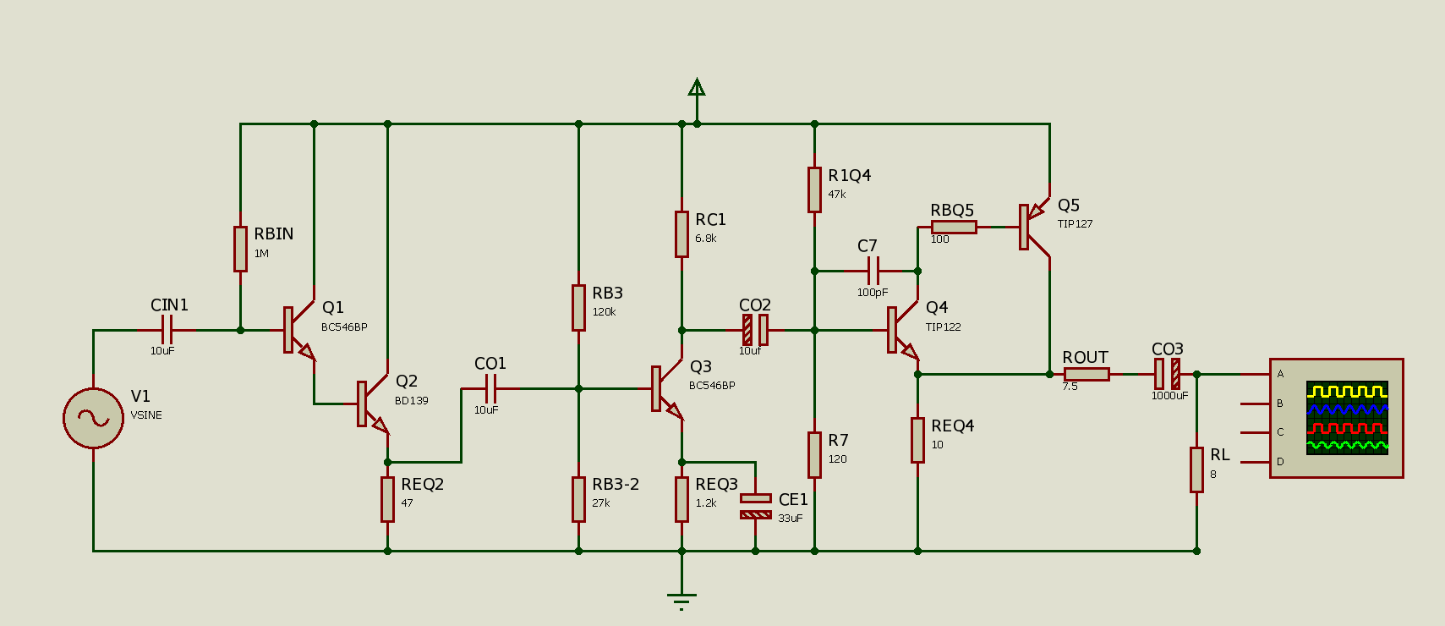
SetupMediciones/TensionesCorrientes/BarridoDeFrecuencia.png
