juan-felipe-castilla/TP2_Analogica/SetupMediciones/TensionesCorrientes/RdeCorte.png

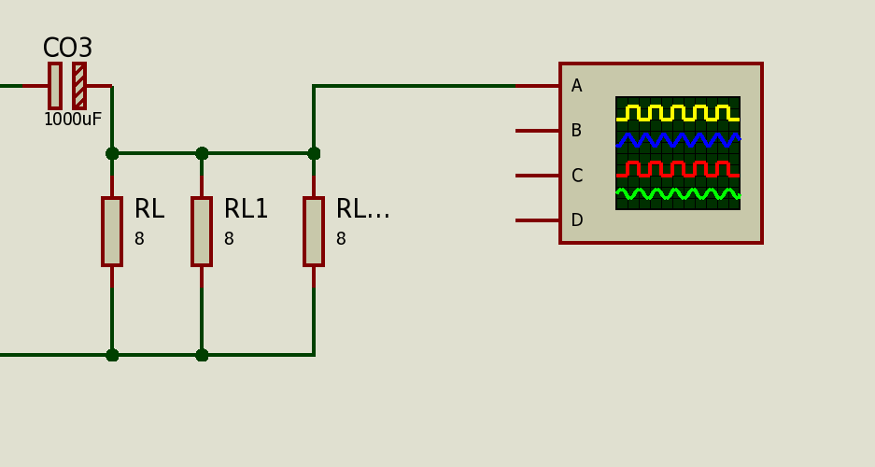
SetupMediciones/TensionesCorrientes/RdeCorte.png
