juan-felipe-castilla/TP2_Analogica/SetupMediciones/TensionesCorrientes/VMaxMinDAR.png

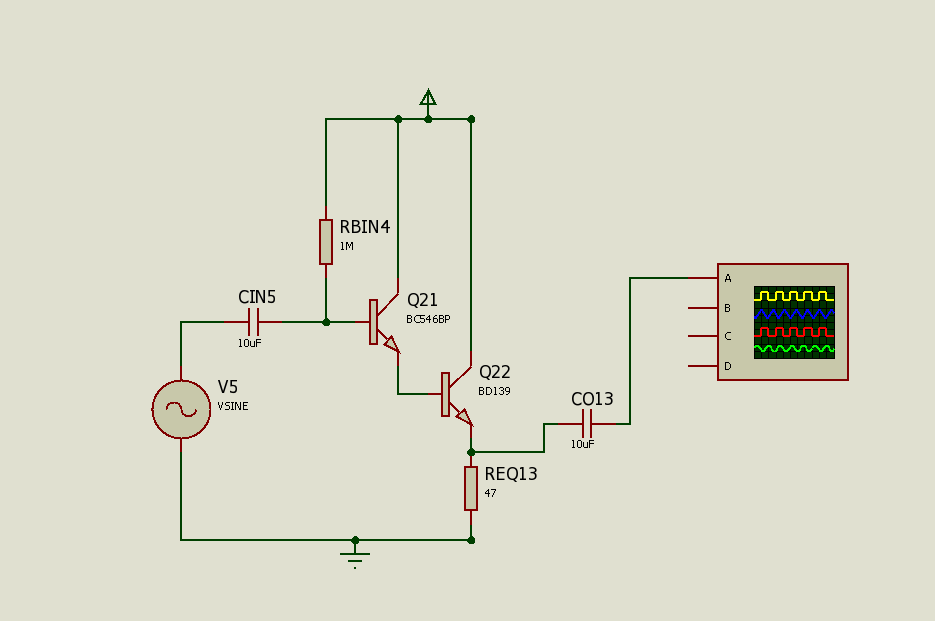
SetupMediciones/TensionesCorrientes/VMaxMinDAR.png
