juan-felipe-castilla/TP2_Analogica/SetupMediciones/TensionesCorrientes/VMaxMinEC.png

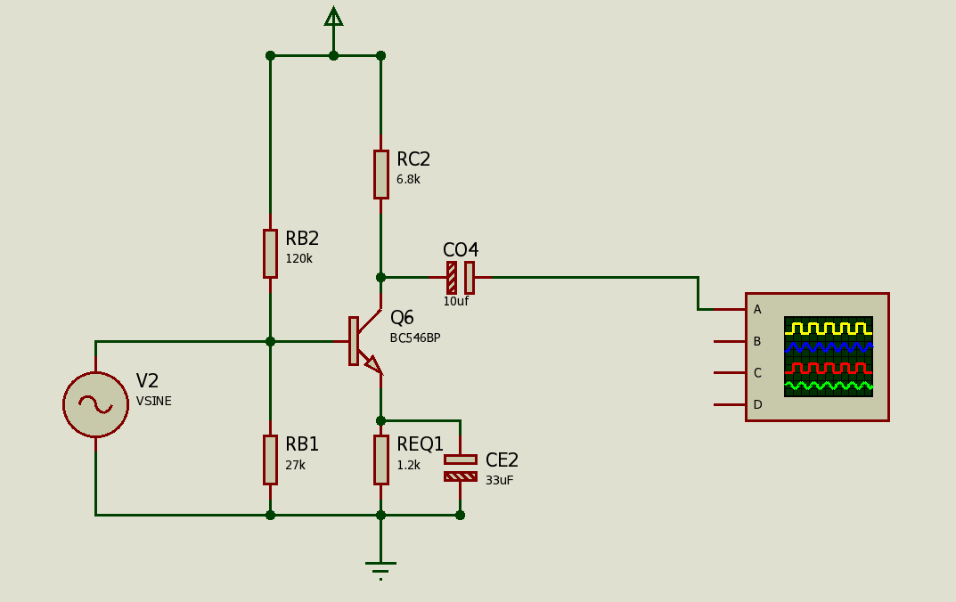
SetupMediciones/TensionesCorrientes/VMaxMinEC.png
