juan-felipe-castilla/TP2_Analogica/SetupMediciones/TensionesCorrientes/VMaxMinSQL.png

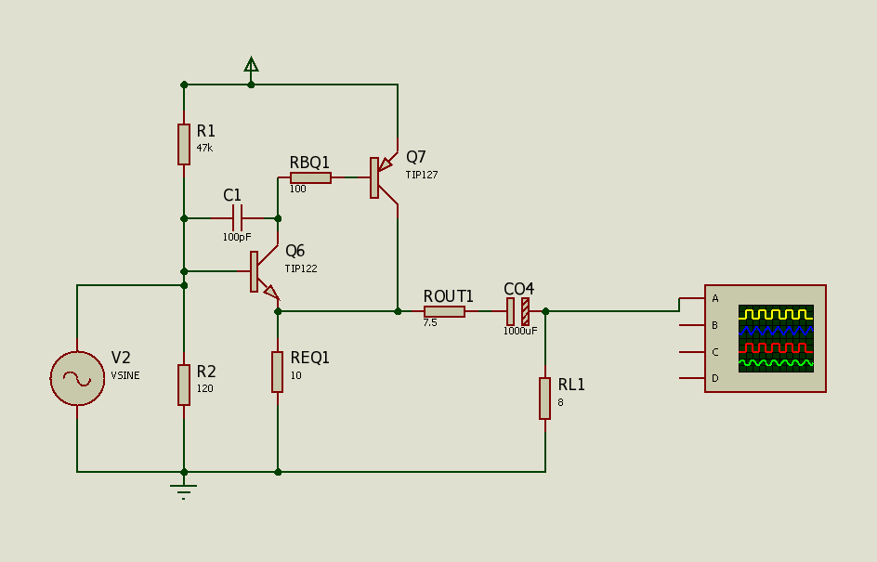
SetupMediciones/TensionesCorrientes/VMaxMinSQL.png
