juan-felipe-castilla/TP2_Analogica/SetupMediciones/TensionesCorrientes/VResitecnias.png

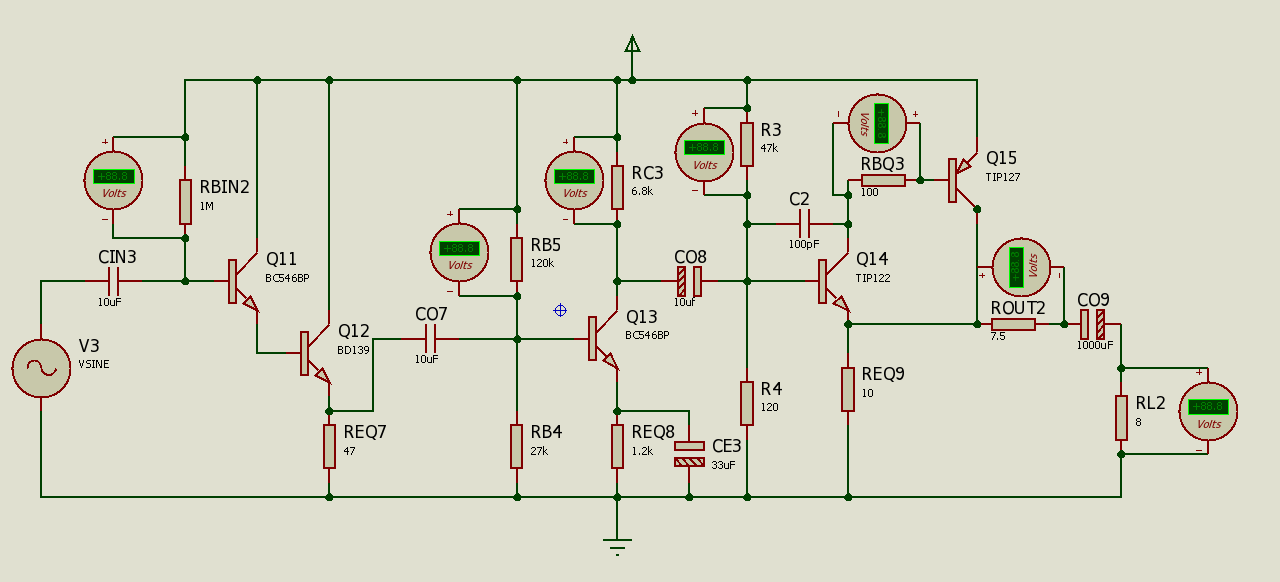
SetupMediciones/TensionesCorrientes/VResitecnias.png
