juan-felipe-castilla/TP2_Analogica/SetupMediciones/ZIN/Zin23.png

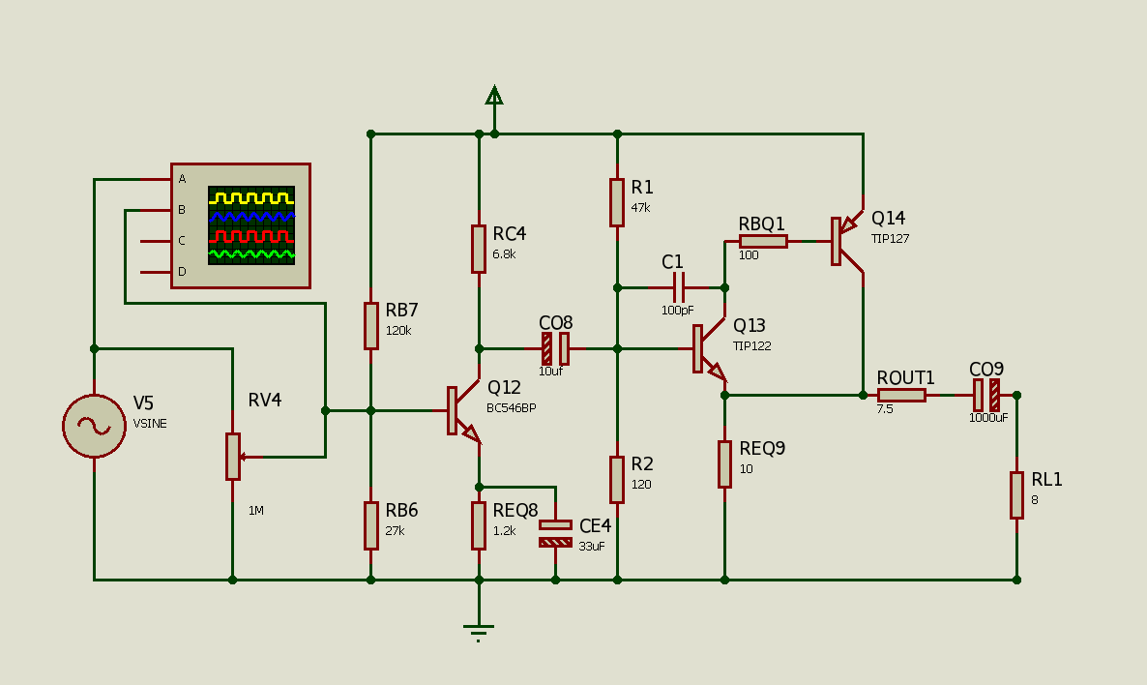
SetupMediciones/ZIN/Zin23.png
