juan-felipe-castilla/TP2_Analogica/SetupMediciones/ZIN/ZinDAR.png

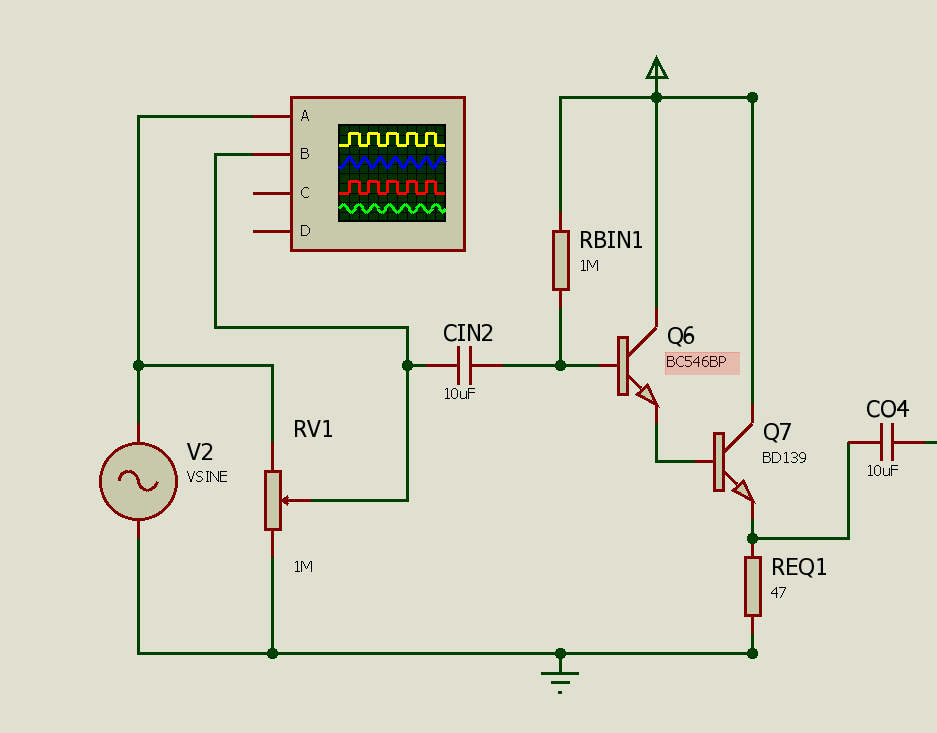
SetupMediciones/ZIN/ZinDAR.png
