juan-felipe-castilla/TP2_Analogica/SetupMediciones/ZIN/ZinEC.png

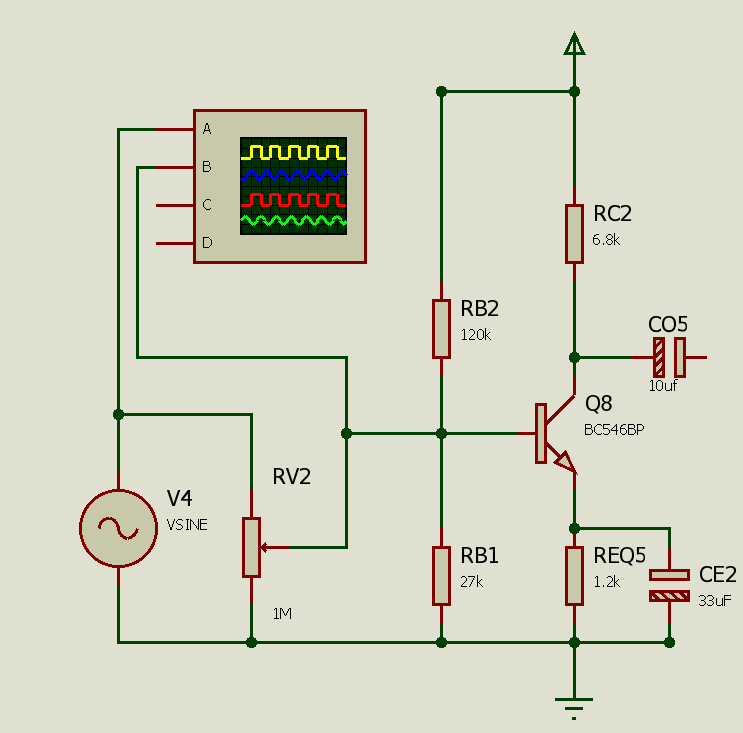
SetupMediciones/ZIN/ZinEC.png
