juan-felipe-castilla/TP2_Analogica/SetupMediciones/ZIN/ZinSQL.png

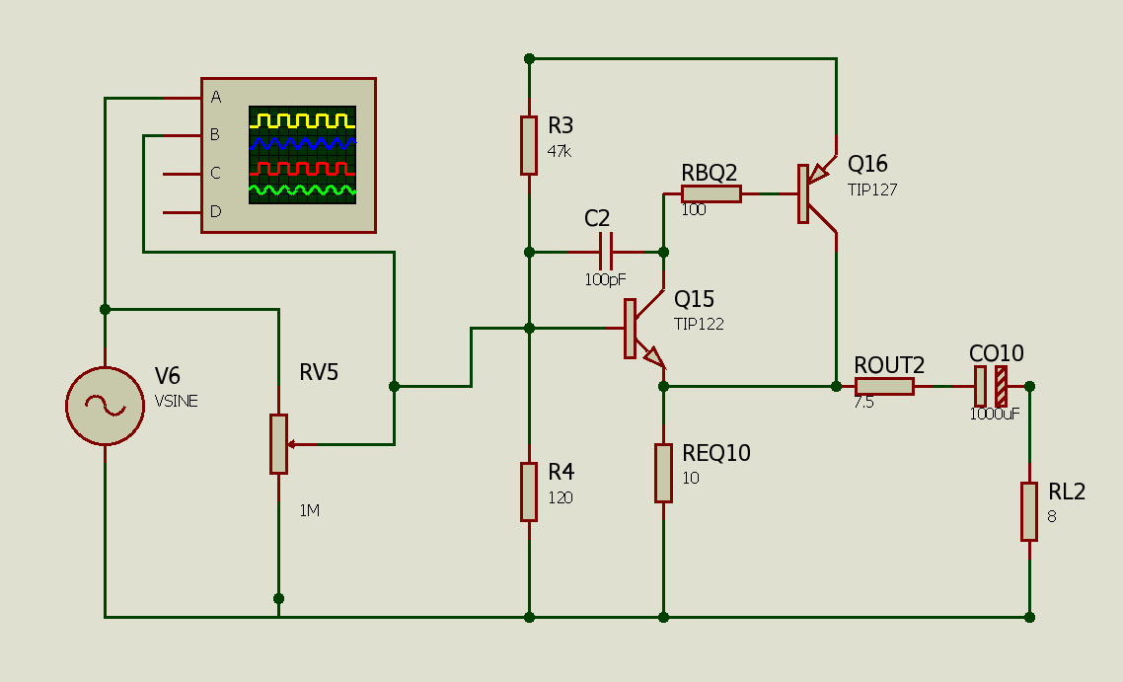
SetupMediciones/ZIN/ZinSQL.png
