juan-felipe-castilla/TP2_Analogica/SetupMediciones/ZIN/ZinTotal.png

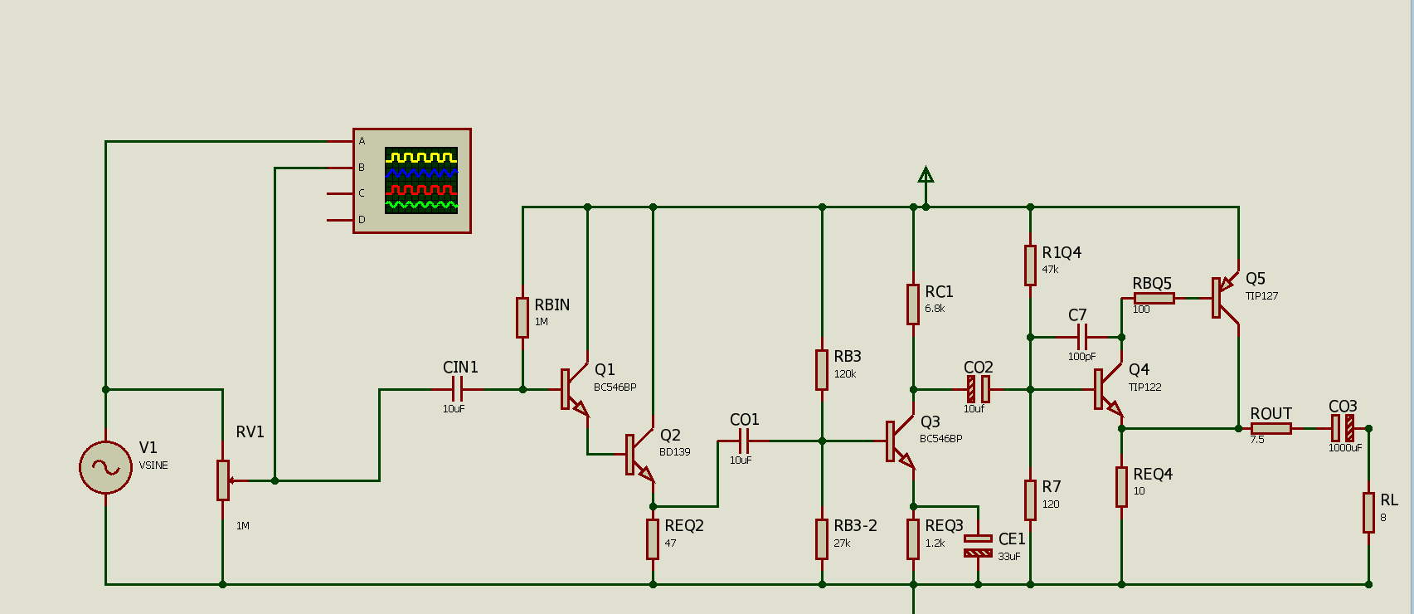
SetupMediciones/ZIN/ZinTotal.png
