juan-felipe-castilla/TP2_Analogica/SetupMediciones/ZOUT/Zout12Cargada.png

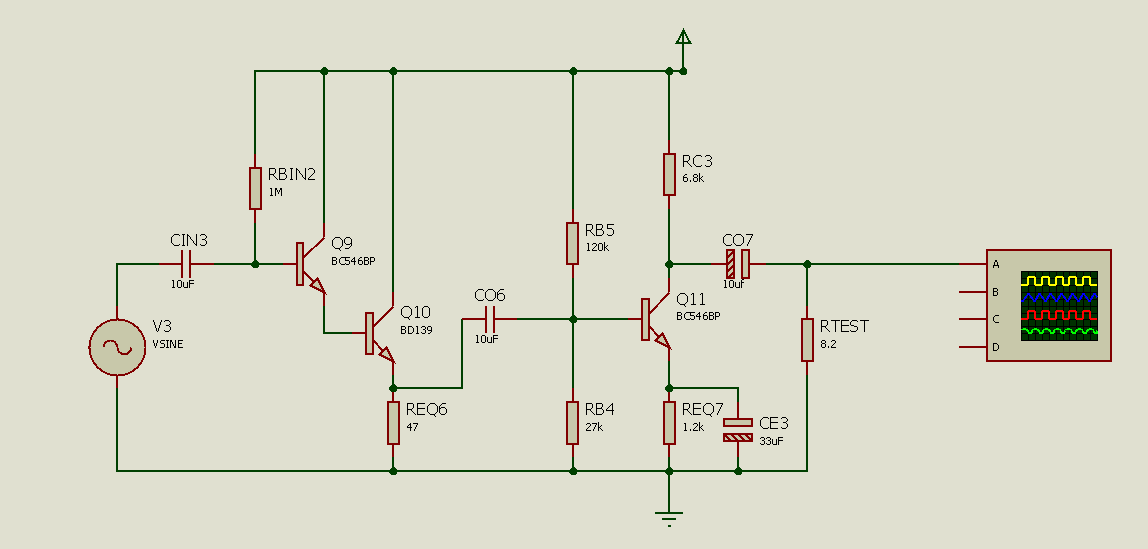
SetupMediciones/ZOUT/Zout12Cargada.png
