juan-felipe-castilla/TP2_Analogica/SetupMediciones/ZOUT/ZoutCarga.png

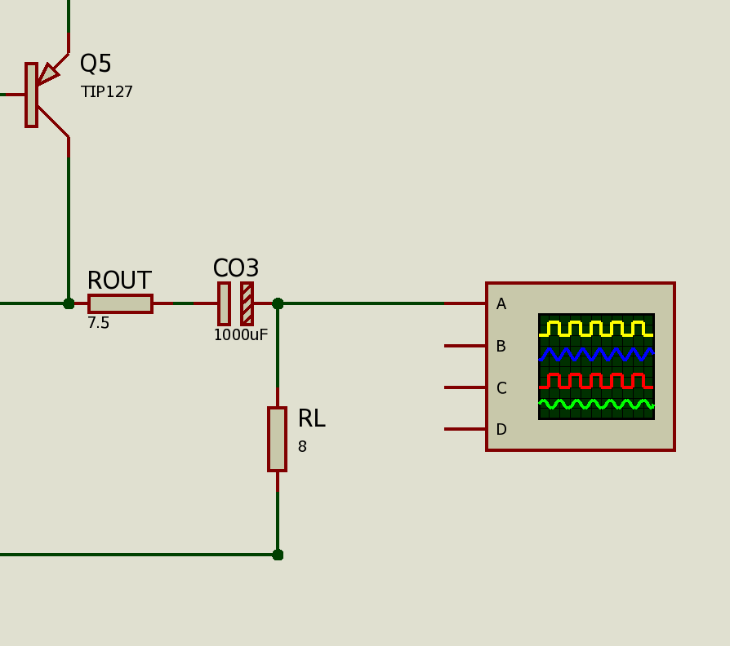
SetupMediciones/ZOUT/ZoutCarga.png
