juan-felipe-castilla/TP2_Analogica/SetupMediciones/ZOUT/ZoutDARCargado.png

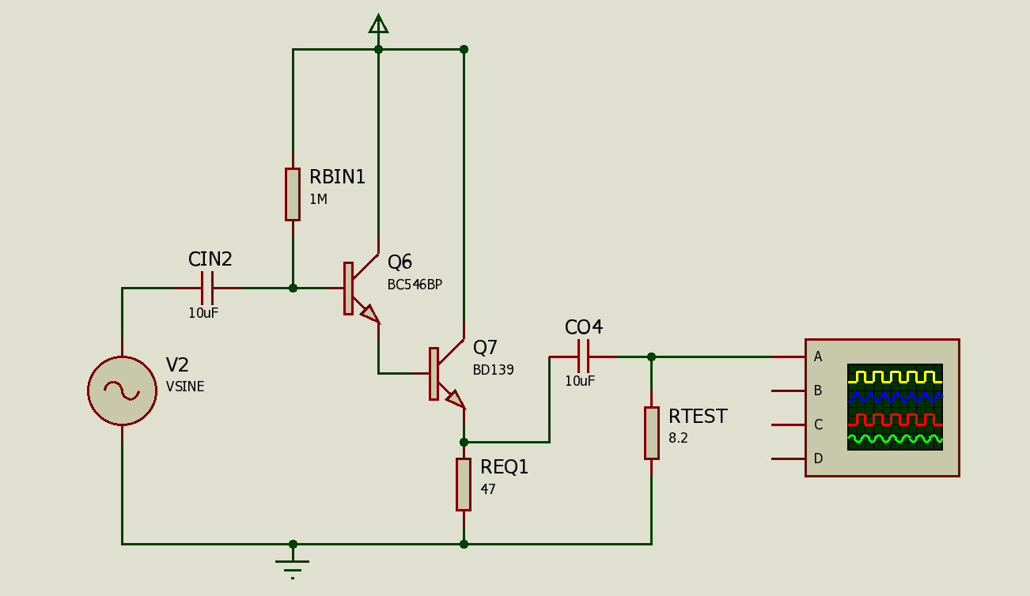
SetupMediciones/ZOUT/ZoutDARCargado.png
