juan-felipe-castilla/TP2_Analogica/SetupMediciones/ZOUT/ZoutDARSinCarga.png

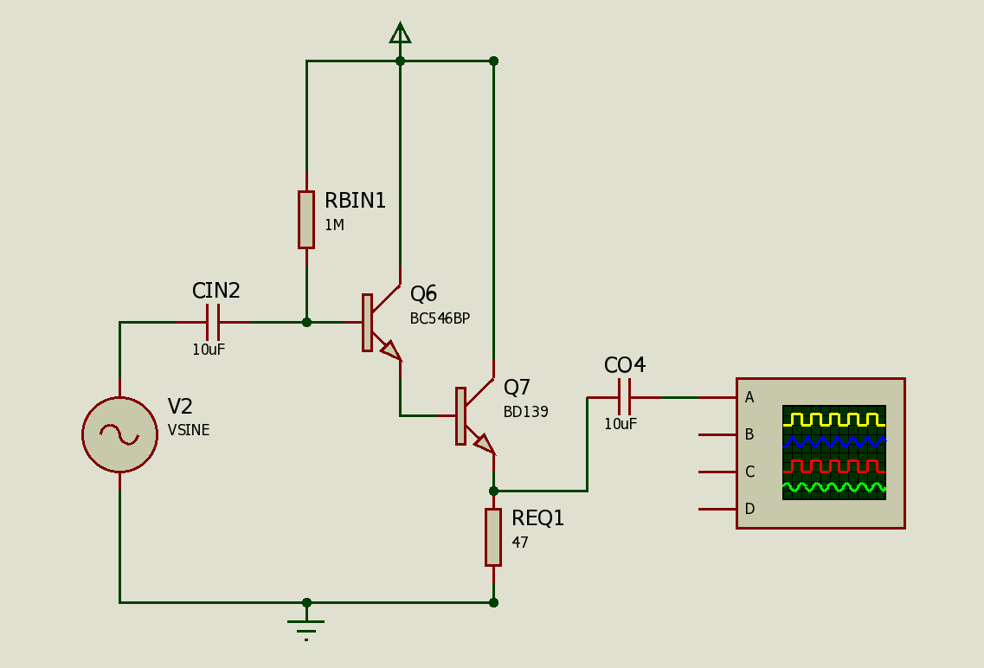
SetupMediciones/ZOUT/ZoutDARSinCarga.png
