juan-felipe-castilla/TP2_Analogica/SetupMediciones/ZOUT/ZoutSinCarga.png

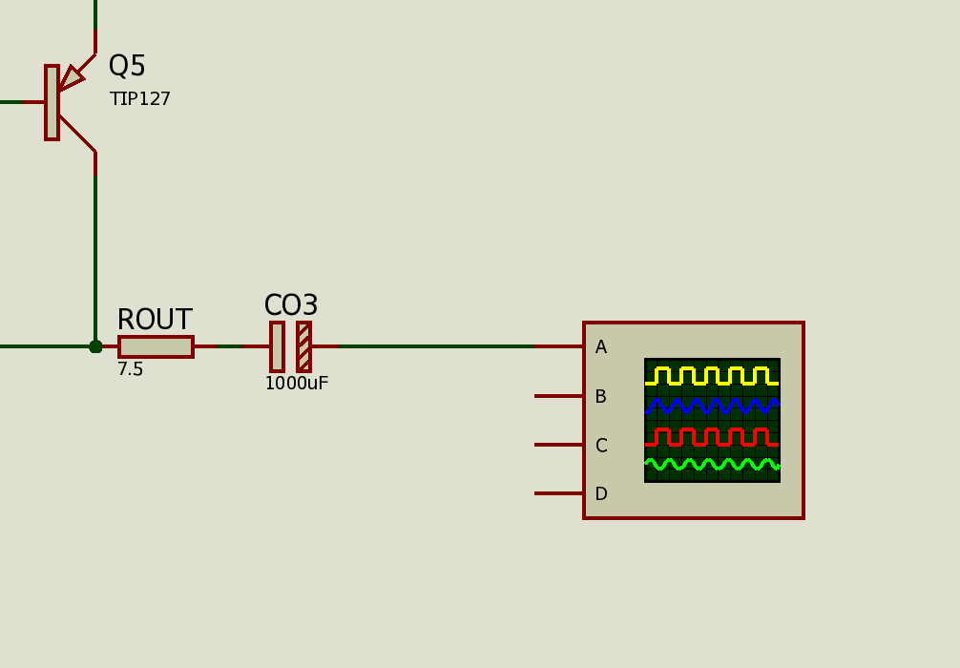
SetupMediciones/ZOUT/ZoutSinCarga.png
