juan-felipe-castilla/TP2_Analogica/Pythons/CodigosPython/Amp2Etapas.asc

C1: cap; 10µ
C2: cap; 10µ
C3: cap; 33µ
C4: cap; 10µ
C5: cap; 10µ
Q1: npn; Mi_BC547C
Q2: npn; Mi_BC547C
Q3: npn; Mi_BC547C
Q4: npn; Mi_BC547C
Q5: pnp; Mi_BD140
R1: res; {R1}
R3: res; {R3}
R4: res; {R4}
R5: res; {R5}
R6: res; {R6}
R7: res; {R7}
R8: res; {R8}
R9: res; {R9}
R10: res; {R10}
RBin: res; 1000k
REin: res; {REin}
RL: res; 8
V1: voltage; SINE(0 {Vval} 2000); AC 0
V2: voltage; 12
Named nets: 0, NodoInput, nodoout
.step param Vval list 10m 20m 30m 40m
.four 2000 V(nodoout)
.inc valores_finales.txt
.model Mi_BC547C NPN(Bf={BETA_NPN})
.model Mi_BD140 PNP(Bf={BETA_PNP})
.tran 0 10m 8m
