juan-felipe-castilla/TP2_Analogica/Pythons/CodigosPython/AMPFINAL.asc

C1: cap; 10µ
C2: cap; 10µ
C3: cap; 33µ
C4: cap; 10µ
C5: cap; 10µ
Q1: npn
Q2: npn
Q3: npn
Q4: npn
Q5: pnp
R1E: res; 120k
R1S: res; 47k
R2E: res; 27k
R2S: res; 100k
RBD: res; 1000k
RCE: res; 6.8k
RED: res; 47
REE: res; 1.2k
RES: res; 10
RL: res; 8
RO: res; 7.5
V1: voltage; SINE(0 10m 2000); AC 1
V2: voltage; 12
Named nets: 0, NodoInput, NodoOut
.model Q1 NPN(IS=4.679E-14 NF=1.01 ISE=2.642E-15 NE=1.581 BF=458.7 IKF=0.1371 VAF=52.64 NR=1.019 ISC=2.337E-14 NC=1.164 BR=11.57 IKR=0.1144 VAR=364.5 RB=1 IRB=1.00E-06 RBM=1 RE=0.2598 RC=1 XTB=0 EG=1.11 XTI=3 CJE=1.229E-11 VJE=0.5591 MJE=0.3385 TF=4.689E-10 XTF=160 VTF=2.828 ITF=0.8842 PTF=0 CJC=4.42E-12 VJC=0.1994 MJC=0.2782 XCJC=0.6193 TR=1.00E-32 CJS=0 VJS=0.75 MJS=0.333 FC=0.7936 Vceo=45 Icrating=100m mfg=Philips)
.model Q2 NPN(IS=4.679E-14 NF=1.01 ISE=2.642E-15 NE=1.581 BF=458.7 IKF=0.1371 VAF=52.64 NR=1.019 ISC=2.337E-14 NC=1.164 BR=11.57 IKR=0.1144 VAR=364.5 RB=1 IRB=1.00E-06 RBM=1 RE=0.2598 RC=1 XTB=0 EG=1.11 XTI=3 CJE=1.229E-11 VJE=0.5591 MJE=0.3385 TF=4.689E-10 XTF=160 VTF=2.828 ITF=0.8842 PTF=0 CJC=4.42E-12 VJC=0.1994 MJC=0.2782 XCJC=0.6193 TR=1.00E-32 CJS=0 VJS=0.75 MJS=0.333 FC=0.7936 Vceo=45 Icrating=100m mfg=Philips)
.model Q3 NPN(IS=4.679E-14 NF=1.01 ISE=2.642E-15 NE=1.581 BF=458.7 IKF=0.1371 VAF=52.64 NR=1.019 ISC=2.337E-14 NC=1.164 BR=11.57 IKR=0.1144 VAR=364.5 RB=1 IRB=1.00E-06 RBM=1 RE=0.2598 RC=1 XTB=0 EG=1.11 XTI=3 CJE=1.229E-11 VJE=0.5591 MJE=0.3385 TF=4.689E-10 XTF=160 VTF=2.828 ITF=0.8842 PTF=0 CJC=4.42E-12 VJC=0.1994 MJC=0.2782 XCJC=0.6193 TR=1.00E-32 CJS=0 VJS=0.75 MJS=0.333 FC=0.7936 Vceo=45 Icrating=100m mfg=Philips)
.model Q4 NPN(IS=4.679E-14 NF=1.01 ISE=2.642E-15 NE=1.581 BF=458.7 IKF=0.1371 VAF=52.64 NR=1.019 ISC=2.337E-14 NC=1.164 BR=11.57 IKR=0.1144 VAR=364.5 RB=1 IRB=1.00E-06 RBM=1 RE=0.2598 RC=1 XTB=0 EG=1.11 XTI=3 CJE=1.229E-11 VJE=0.5591 MJE=0.3385 TF=4.689E-10 XTF=160 VTF=2.828 ITF=0.8842 PTF=0 CJC=4.42E-12 VJC=0.1994 MJC=0.2782 XCJC=0.6193 TR=1.00E-32 CJS=0 VJS=0.75 MJS=0.333 FC=0.7936 Vceo=45 Icrating=100m mfg=Philips)
.MODEL Q5 PNP (IS=2.9537E-13 BF=201.4 NF=1.0 BR=23.765 NR=1.021 ISE=1.8002E-13 NE=1.5 ISC=7.0433p NC=1.38 VAF=137.0 VAR=8.41 IKF=1.0993 IKR=0.10 RB=1.98 RBM=0.01 IRB=0.011 RE=0.1109 RC=0.01 CJE=2.1982E-10 VJE=0.7211 MJE=0.3685 FC=0.5 CJC=6.8291E-11 VJC=0.5499 MJC=0.3668 XCJC=0.5287 XTB=1.4883 EG=1.2343 XTI=3.0 Vceo=80 Icrating=3 mfg=fairchild)
==================================================
RESUMEN FINAL: Se encontraron 3 configuraciones exitosas
==================================================
Opción 1:
  Ganancia: 76.88
  MES (Excursión Real): 1.38 V pico
  Impedancia Entrada: 878049.11 Ohms
  Impedancia Salida: 7.65 Ohms
  Resistencias: {'BETA_NPN': 325, 'BETA_PNP': 343, 'REin': 68, 'R1': 7.5, 'R3': 120000, 'R4': 22000, 'R5': 4700, 'R6': 10, 'R7': 1000, 'R8': 68000, 'R9': 68000, 'R10': 22}
  -> Archivo 'valores_finales.txt' generado con éxito para LTspice.
--------------------------------------------------
Opción 2:
  Ganancia: 91.35
  MES (Excursión Real): 1.95 V pico
  Impedancia Entrada: 833311.68 Ohms
  Impedancia Salida: 7.63 Ohms
  Resistencias: {'BETA_NPN': 325, 'BETA_PNP': 343, 'REin': 47, 'R1': 7.5, 'R3': 180000, 'R4': 33000, 'R5': 6800, 'R6': 10, 'R7': 1200, 'R8': 100000, 'R9': 47000, 'R10': 22}
--------------------------------------------------
Opción 3:
  Ganancia: 84.27
  MES (Excursión Real): 2.27 V pico
  Impedancia Entrada: 833069.62 Ohms
  Impedancia Salida: 8.28 Ohms
  Resistencias: {'BETA_NPN': 325, 'BETA_PNP': 343, 'REin': 47, 'R1': 8.2, 'R3': 120000, 'R4': 27000, 'R5': 4700, 'R6': 10, 'R7': 1000, 'R8': 47000, 'R9': 47000, 'R10': 10}
.tran 0 10m 8m
